uncreatednet/wikilab-ufabc/folhas/completo.pdf

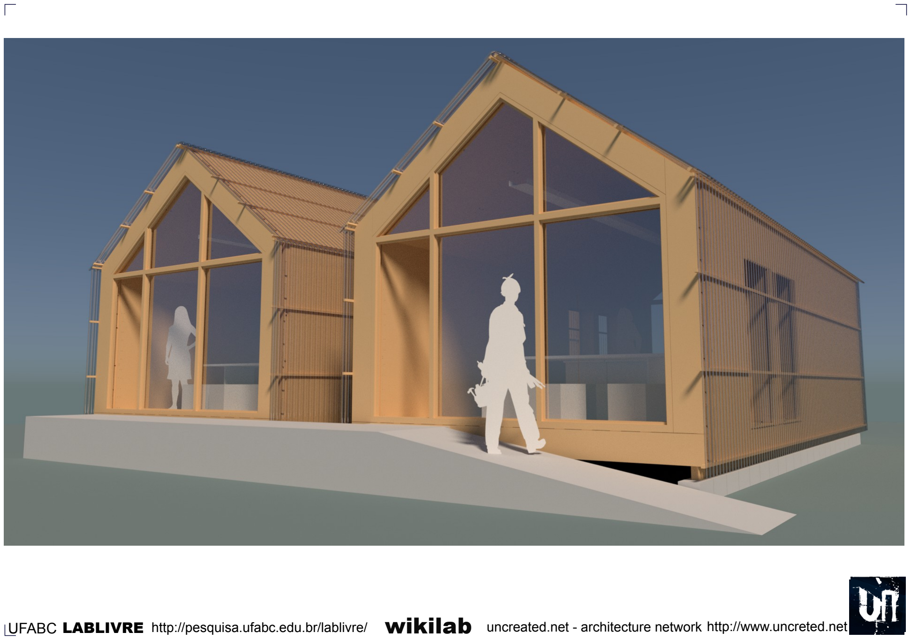
[picture p20: page 1]

UFABC LABLIVRE http://pesquisa.ufabc.edu.br/lablivre/ wikilab uncreated.net - architecture network http://www.uncreted.net

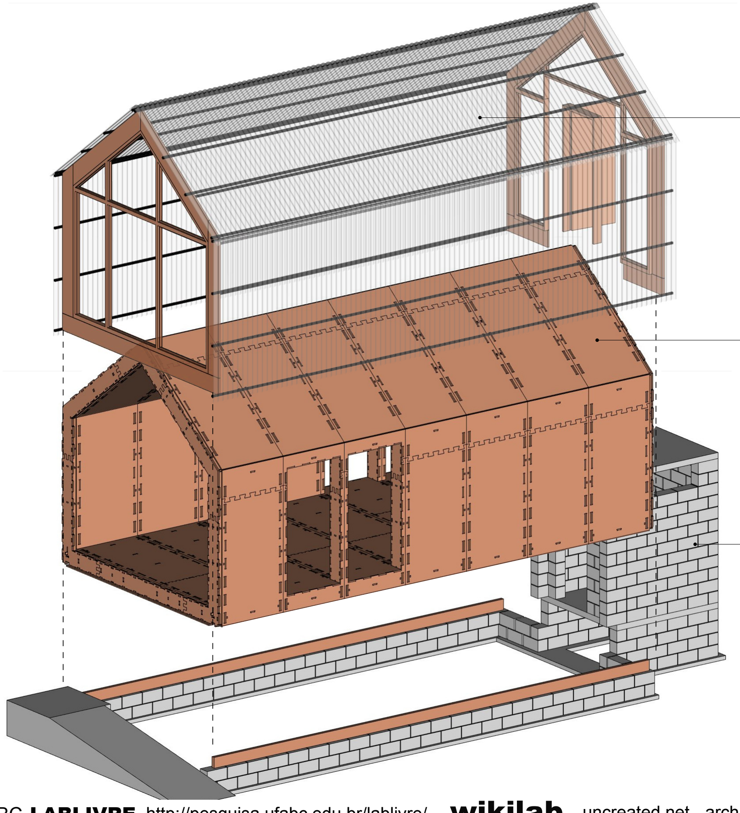
[picture p21: figure]

Fase 1

Feita por empreiteira
Construção da base de alvenaria Equipamentos sanitários
Vigas-guia

Fase 2

Feita por voluntários e comunidade Montagem dos módulos Wikihouse

Fase 3

Feita por voluntários e comunidade com apoio de empreiteira
Montagem da cobertura
Colocação dos caixilhos

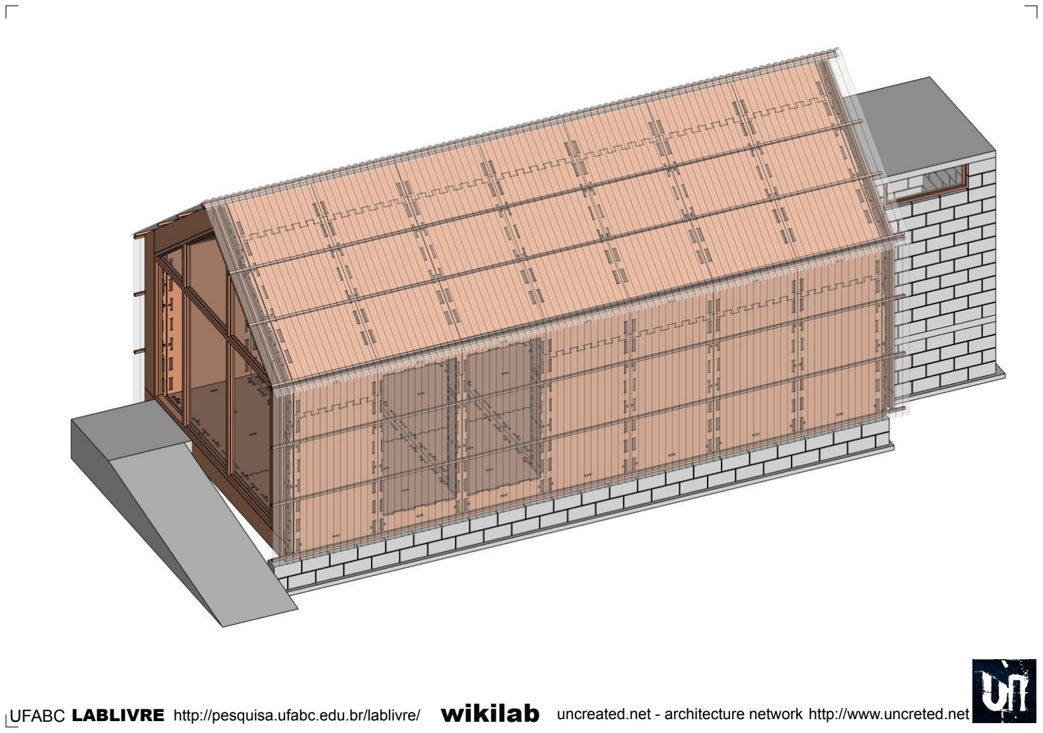
[picture p22: page 3]
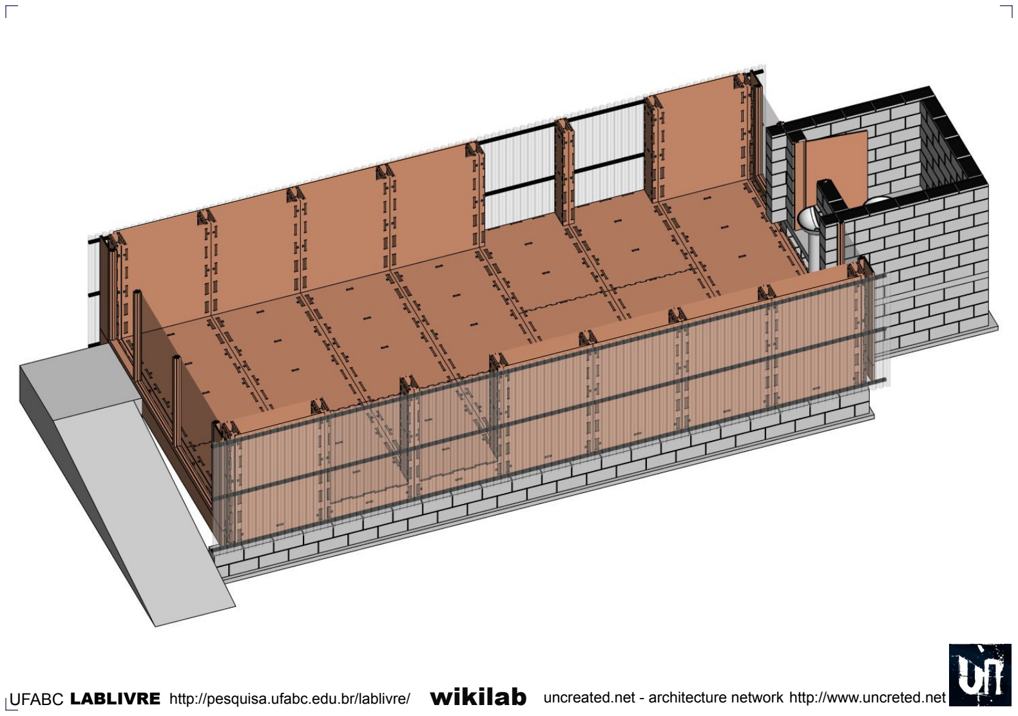
[picture p23: page 4]
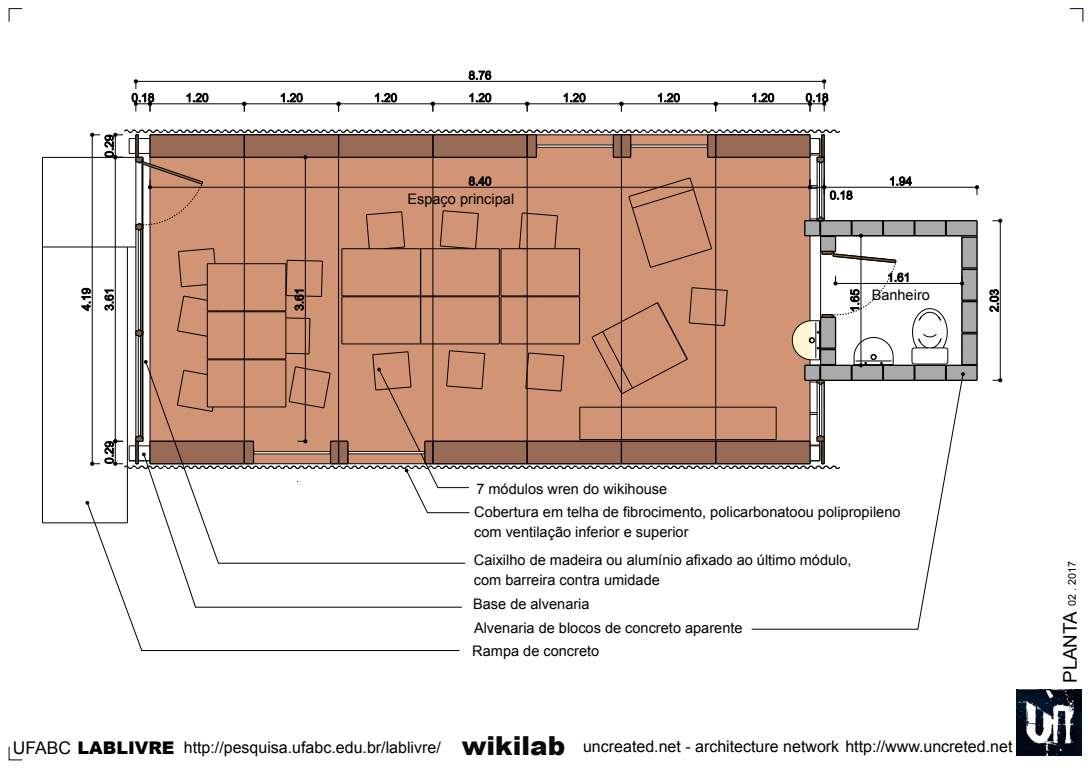
[picture p24: page 5]
wikilab; Espaço principal; Banheiro; UFABC LABLIVRE; PLANTA 02 . 2017; http://pesquisa.ufabc.edu.br/lablivre/; uncreated.net - architecture network http://www.uncreted.net

7 módulos wren do wikihouse
Cobertura em telha de fibrocimento, policarbonatoou polipropileno
com ventilação inferior e superior
Caixilho de madeira ou alumínio afixado ao último módulo,
com barreira contra umidade
Base de alvenaria
Alvenaria de blocos de concreto aparente
Rampa de concreto

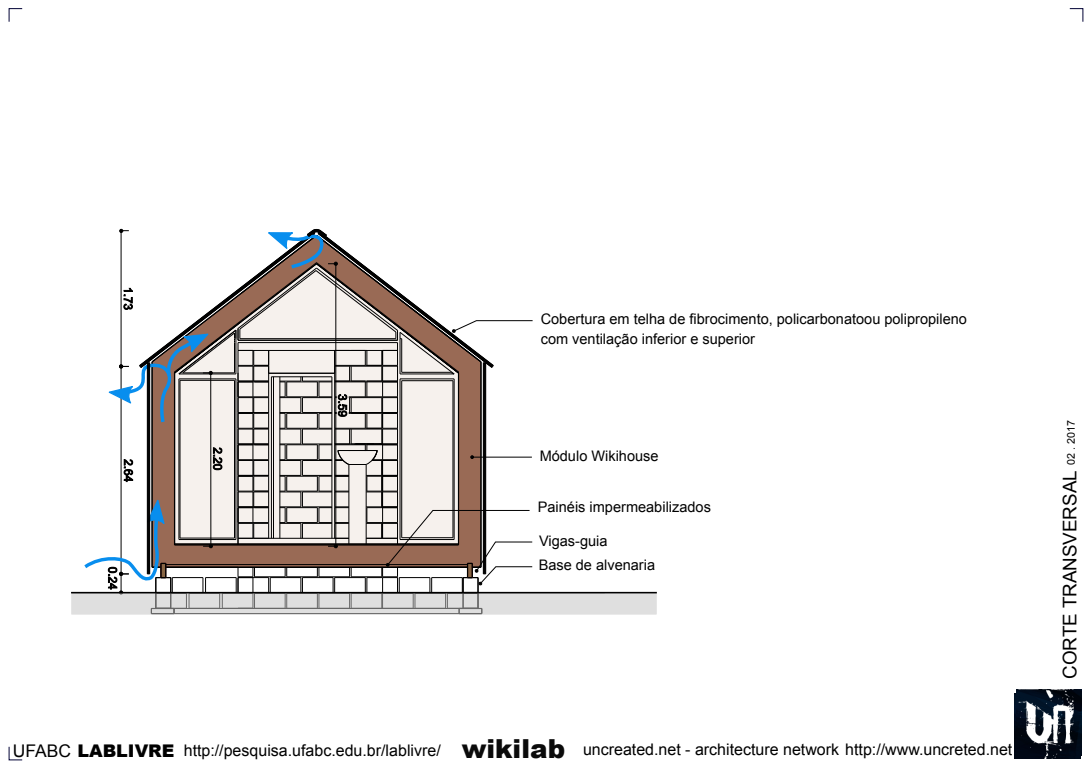
[picture p25: page 6]
CORTE TRANSVERSAL 02 . 2017; Módulo Wikihouse; Painéis impermeabilizados

Cobertura em telha de fibrocimento, policarbonatoou polipropileno
com ventilação inferior e superior

Vigas-guia
Base de alvenaria

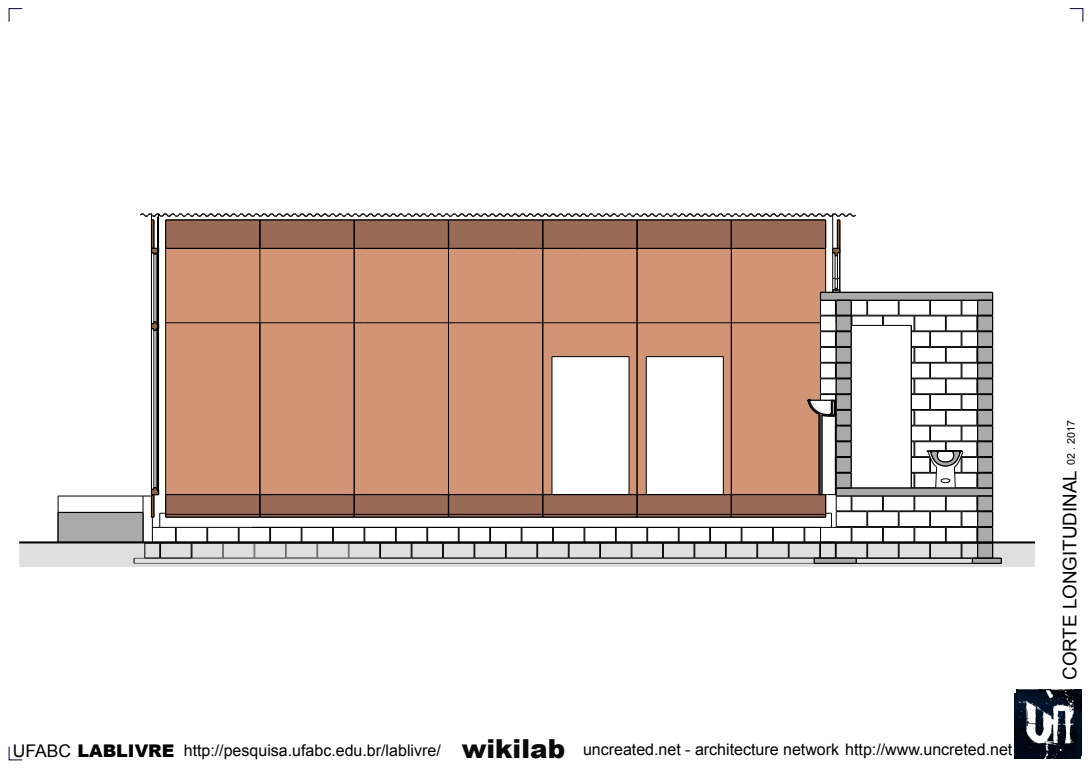
[picture p26: page 7]
CORTE LONGITUDINAL 02 . 2017

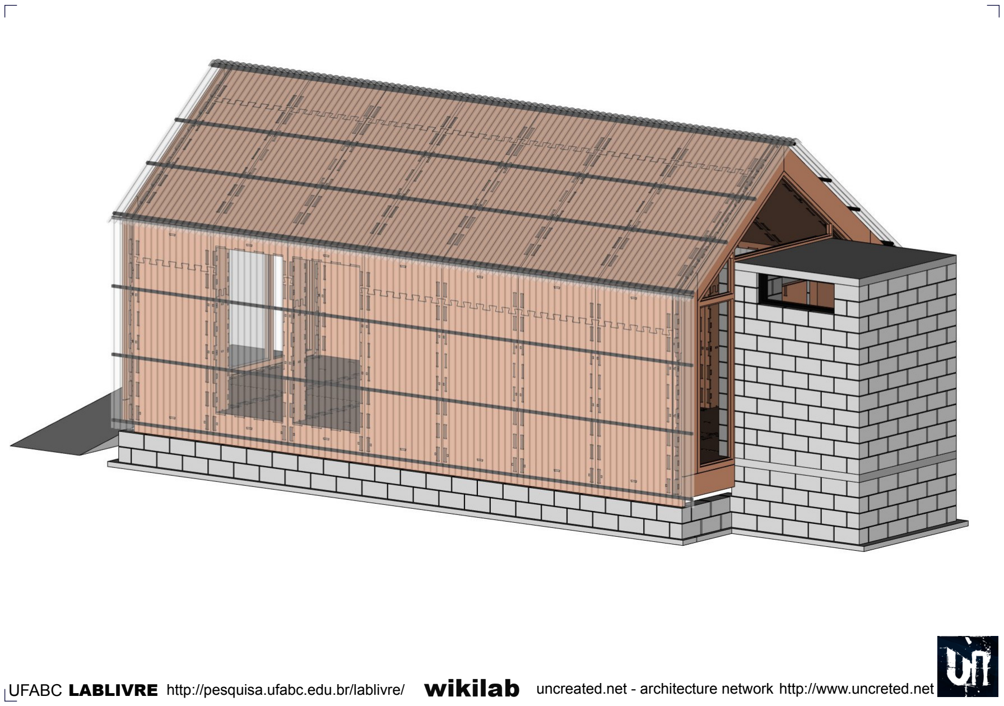
[picture p27: page 8]
