uncreatednet/wikilab-ufabc/elétrico/final/1718-EL-MC-01-R00.pdf

1/16

DESCRIÇÃO DA REVISÃO / PROPÓSITO DA EMISSÃO

0 | AVG | CS | MI | 09/10/17 | EMISSÃO INICIAL / PARA INFORMAÇÃO
REVISÃO | ELABORADO | VERIFICADO | APROVADO
ELÉTRICA | N° DOC: | 1718-EL-MC-01

MEMÓRIA DE CÁLCULO DE SPDA

N° CLIENTE: | ---
OS: | 1718 | REV.:
DATA: | 09/10/2017 | FL.:

0

CLIENTE: | IGMA - CONSTRUÇÕES LTDA | LOCAL: | SÃO BERNARDO DO CAMPO
PROJETO: | WIKILAB | ATIVIDADE: | ELÉTRICA

MARIO IKEDA
Engenheiro Eletricista
CREA Nº0600918701

DATA

### ELÉTRICA MEMÓRIA DE CÁLCULO DE SPDA

### PDF created with pdfFactory Pro trial version www.pdffactory.com

2/16
CLIENTE: | IGMA - CONSTRUÇÕES LTDA | LOCAL: | SÃO BERNARDO DO CAMPO
PROJETO: | WIKILAB | ATIVIDADE: | ELÉTRICA
Revisão | 0 | 1 | 2 | 3 | 4 | 5 | Revisão | 0 | 1 | 2 | 3 | 4 | 5 | Revisão | 0 | 1 | 2 | 3 | 4 | 5
Folha | | | | | | | Folha | | | | | | | Folha
1 | X | | | | | | 21 | | | | | | | 41
2 | X | | | | | | 22 | | | | | | | 42
3 | X | | | | | | 23 | | | | | | | 43
4 | X | | | | | | 24 | | | | | | | 44
5 | X | | | | | | 25 | | | | | | | 45
6 | X | | | | | | 26 | | | | | | | 46
7 | X | | | | | | 27 | | | | | | | 47
8 | X | | | | | | 28 | | | | | | | 48
9 | X | | | | | | 29 | | | | | | | 49
10 | X | | | | | | 30 | | | | | | | 50
11 | X | | | | | | 31 | | | | | | | 51
12 | X | | | | | | 32 | | | | | | | 52
13 | X | | | | | | 33 | | | | | | | 53
14 | X | | | | | | 34 | | | | | | | 54
15 | X | | | | | | 35 | | | | | | | 55
16 | X | | | | | | 36 | | | | | | | 56
17 | | | | | | | 37 | | | | | | | 57
18 | | | | | | | 38 | | | | | | | 58
19 | | | | | | | 39 | | | | | | | 59
20 | | | | | | | 40 | | | | | | | 60

DOCUMENTOS DE REFERÊNCIA

NOTAS

CONTROLE DE REVISÃO DO DOCUMENTO
1. Deverá ser emitidoo documento completo onde será indicadoa folha revisada, conforme tabela abaixo.
01) Projeto Executivo - Wikilab

3/16
CLIENTE: | IGMA - CONSTRUÇÕES LTDA | LOCAL: | SÃO BERNARDO DO CAMPO
PROJETO: | WIKILAB | ATIVIDADE: | ELÉTRICA

1- Objetivo:

Este documento tem por finalidade determinar a necessidade, de implantação de uma proteção contra descargas atmosféricas e nos casos onde for necessária a implantação calcular os parâmetros necessários para a elaboração do projeto de SPDA.

2- Introdução:

Descargas atmosféricas para a terra podem ser perigosas para as estruturas e para as linhas de energia e de sinal.
Os perigos para uma estrutura podem resultar em:
a) Danos à estrutura e ao seu conteúdo;
b) Falhas aos sistemas eletroeletrônicos associados;
c) Ferimentos a seres vivos dentro ou perto das estruturas.

Os efeitos consequentes dos danos e falhas podem ser estendidos às vizinhanças da estrutura ou podem envolver o meio ambiente.
Para reduzir as perdas devidos às descargas atmosféricas, podem ser necessárias medidas de proteção. Quando estas são necessárias, e em qual medida, deve ser determinado pela análise de risco.
O risco, definido pela norma ABNT NBR 5419:2015 como a provável perda média anual em uma estrutura devido às descargas atmosféricas, depende de:
a) O número anual de descargas atmosféricas que influenciam a estrutura;
b) A probabilidade de dano por uma das descargas atmosféricas que influenciam;
c) A quantidade média das perdas causadas.

As descargas atmosféricas que influenciam a estrutura podem ser divididas em:

a) Descargas diretas à estrutura;
b) Descargas próximas à estrutura, diretas às linhas conectadas (linhas de energia, linhas de telecomunicações) ou perto das linhas.

Descargas atmosféricas diretas à estrutura ou a uma linha conectada podem causar danos físicos e perigo à vida.
Descargas atmosféricas próximas à estrutura ou à linha, assim como as descargas atmosféricas diretas à estrutura ou à linha, podem causar falhas dos sistemas eletroeletrônicos devido às sobretensões resultantes do acoplamento resistivo e indutivo destes sistemas com a corrente da descarga atmosférica.
Entretanto, as falhas causadas pelas sobretensões atmosféricas nas instalações do usuário e nas linhas de suprimento de energia podem também gerar sobretensões do tipo de chaveamento nas instalações.

NOTA: O mau funcionamento dos sistemas eletroeletrônicos não é coberto pela série ABNT NBR 5419:2015. Para tanto, recomenda-se consultar a IEC 61000-4-5.

O número das descargas atmosféricas que influenciam a estrutura depende das dimensões e das características das estruturas e das linhas conectadas, das características do ambiente da estrutura e das linhas, assim como da densidade de descargas atmosféricas para a terra na região onde estão localizadas a estrutura e as linhas.
A probabilidade de danos devido à descarga atmosférica depende da estrutura, das linhas conectadas, e das características da corrente da descarga atmosférica, assim como do tipo e da eficiência das medidas de proteção efetuadas.
A quantidade média da perda consequente depende da extensão dos danos e dos efeitos consequentes, os quais podem ocorrer como resultado de uma descarga atmosférica.

4/16
CLIENTE: | IGMA - CONSTRUÇÕES LTDA | LOCAL: | SÃO BERNARDO DO CAMPO
PROJETO: | WIKILAB | ATIVIDADE: | ELÉTRICA

O efeito das medias de proteção resulta das características de cada medida de proteção e pode reduzir as probabilidades de danos ou a quantidade média da perda consequente.
A decisão de prover uma proteção contra descargas atmosféricas pode ser tomada independente-mente do resultado da análise de risco, onde exista o desejo de que não haja este.

3- Referências normativas:

ABNT NBR 5419-1:2015 – Proteção contra descargas atmosféricas – Parte 1: Princípios Gerais; ABNT NBR 5419-2:2015 – Proteção contra descargas atmosféricas – Parte 2: Gerenciamento de Risco;
ABNT NBR 5419-3:2015 –Proteção contra descargas atmosféricas – Parte 3: Danos físicos a estrutura e perigos à vida;
ABNT NBR 5419-4:2015 –Proteção contra descargas atmosféricas – Parte 4: Sistemas elétricos e eletrônicos internos na estrutura;

4- Símbolos e abreviaturas:

a | Taxa de amortização
AD | Área de exposição equivalente para descargas atmosféricas a uma estrutura isolada
ADJ | Área de exposição equivalente para descargas atmosféricas a uma estrutura adjacente
AD | Área de exposição equivalente atribuída a uma saliência elevada na cobertura
AI | Área de exposição equivalente para descargas atmosféricas perto de uma linha
AL | Área de exposição equivalente para descargas atmosféricas em uma linha
AM | Área de exposição equivalente para descargas atmosféricas perto de uma estrutura
B | Edificação
CD | Fator de localização
CDJ | Fator de localização de uma estrutura adjacente
CE | Fator ambiental
CI | Fator de uma instalação de uma linha
CL | Custo anual das perdas totais na ausência de medidas de proteção
CLD | Fator dependente da blindagem, aterramento e condições de isolação da linha para
descargas atmosféricas na linha
CLI Fator dependente da blindagem, aterramento e condições de isolação da linha para descargas atmosféricas perto da linha
CLZ | Custo de perdas em uma zona
CP | Custo das medidas de proteção
COM | Custo anual das medidas de proteção selecionadas
CRL | Custo anual de perdas residuais
CRLZ | Custo de perdas residuais em uma zona
CT | Fator de tipo de linha para um transformador AT/BT na linha
Ca | Valor de animais em uma zona, em espécie
Cb | Valor do edifício relevante a zona, em espécie
Cc | Valor do conteúdo em uma zona, em espécie
Ce | Valor total dos bens em locais perigosos fora da estrutura, em espécie
Cs | Valor dos sistemas internos (incluindo suas atividades) em uma zona, em espécie
Ct | Valor total da estrutura, em espécie
Cz | Valor do patrimônio cultural em uma zona, em espécie
D1 | Ferimentos a seres vivos por choque elétrico
D2 | Danos físicos
D3 | Falhas de sistemas eletroeletrônicos
hZ | Fator de aumento de perda quando um perigo especial está presente
H | Altura da estrutura
HJ | Altura de uma estrutura adjacente
i | Taxa de juros
KMS | Fator relevante ao desempenho das medidas de proteção contra LEMP
KS1 | Fator relevante à efetividade da blindagem por malha de uma estrutura

5/16
CLIENTE: | IGMA - CONSTRUÇÕES LTDA | LOCAL: | SÃO BERNARDO DO CAMPO
PROJETO: | WIKILAB | ATIVIDADE: | ELÉTRICA
KS2 | Fator relevante à efetividade da blindagem por malha dos campos internos de uma estrutura
KS3 | Fator relevante as características do cabeamento interno
KS4 | Fator relevante à tensão suportável de impulso de um sistema
L | Comprimento da estrutura
La | Comprimento da estrutura adjacente
LA | Perda relacionada aos ferimentos a seres vivos por choque elétrico (descargas atmosféricas
à estrutura)
LB Perda em uma estrutura relacionada a danos físicos (descargas atmosféricas à estrutura) Comprimento de uma seção da linha
LC | Perda relacionada a falha dos sitemas internas (descargas atmosféricas à estrutura)
LE | Perda adicional quando os danos envolvem estruturas ao redor
LF | Perda em uma estrutura devido a danos físicos
LFE | Perda devido a danos físicos fora da estrutura
LFT | Perda total devido a danos físicos dentro e fora da estrutura
LM | Perda relacionada à falha de sistemas internas (descargas atmosféricas perto de uma
estrutura)
LO | Perda em uma estrutura devido à falha de sistemas internos
LT | Perda devido a ferimentos por choque elétrico
LU | Perda relacionada a ferimentos de seres vivos por choque elétrico (descargas atmosféricas
na linha
LV | Perda em uma estrutura devido a danos físicos (descargas atmosféricas na linha)
LW | Perda devido à falha de sistemas internos (descargas atmosféricas na linha)
LX | Perda consequente a danos relevantes a estrutura
LZ | Perda relacionada à falha de sistemas internos (descargas atmosféricas na linha)
L1 | Perda de vida humana
L2 | Perda de serviço ao público
L3 | Perda de patrimônio cultural
L4 | Perda de valor econômico
m | Taxa de manutenção
NX | Número de eventos perigosos por ano
ND | Número de eventos perigosos devido às descargas atmosféricas em uma estrutura
NDJ | Número de eventos perigosos devido às descargas atmosféricas em uma estrutura adjacente
NG | Densidade de descargas atmosféricas para a terra
NI | Número de eventos perigosos devido às descargas atmosféricas perto de uma linha
NL | Número de eventos perigosos devido às descargas atmosféricas a uma linha
NM | Número de eventos perigosos devido às descargas atmosféricas perto de uma estrutura
nZ | Número de possíveis pessoas em perigo (vítimas ou usuários não servidos)
nt | Número total de pessoas (ou usuários atendidos) esperado
P | Probabilidade de danos
PA | Probabilidade de ferimentos de seres vivos por choque elétrico (descargas atmosféricas à
estrutura)
PB | Probabilidade de danos físicos à estrutura (descargas atmosféricas à estrutura)
PC | Probabilidade de falha de sistemas internos (descargas atmosféricas à estrutura)
PEB | Probabilidade de reduzir PU e PV dependendo das características da linha e da tensão
suportável do equipamento quando EB (ligação equipotencial) é instalada
PLD Probabilidade de reduzir PU, PV e PW dependendo das características da linha e da tensão suportável do equipamento (descargas atmosféricas na linha conectada)
PLI Probabilidade de reduzir PZ dependendo das características da linha e da tensão suportável do equipamento (descargas atmosféricas perto da linha conectada)
PM Probabilidade de falha de sistemas internos (descargas atmosféricas perto da linha conectada)
PMSI Probabilidade de reduzir PM dependendo da blindagem, cabeamento e da tensão suportável do equipamento
PSPD Probabilidade de reduzir PC, PM, PW e PZ quando um sistema coordenado de DPS está instalado
PTA Probabilidade de reduzir PA dependendo das medidas de proteção contra tensões de toque e

6/16
CLIENTE: | IGMA - CONSTRUÇÕES LTDA | LOCAL: | SÃO BERNARDO DO CAMPO
PROJETO: | WIKILAB | ATIVIDADE: | ELÉTRICA

passo
PU Probabilidade de ferimentos de seres vivos por choque elétrico (descargas atmosféricas perto da linha conectada)
PV | Probabilidade de danos físicos à estrutura (descargas atmosféricas perto da linha conectada)
PW | Probabilidade de falha de sistemas internos (descargas atmosféricas na conectada)
PX | Probabilidade de danos relevantes à estrutura (descargas atmosféricas à estrutura)
PZ | Probabilidade de falha de sistemas internos (descargas atmosféricas perto da linha
conectada)
rt | Fator de redução associado ao tipo de superfície do solo
rf | Fator redutor de perda dependente do risco de incêndio
rp | Fator redutor de perda devido às precauções contra incêndio
R | Risco
RA | Componente de risco (ferimentos a seres vivos - descarga atmosférica na estrutura)
RB | Componente de risco (danos físicos na estrutura - descarga atmosférica na estrutura)
RC | Componente de risco (falha dos sistemas internos - descarga atmosférica na estrutura)
RM | Componente de risco (falha dos sistemas internos - descarga atmosférica perto da estrutura)
RS | Resistência da blindagem por unidade de comprimento de um cabo
RT | Risco tolerável
RU | Componente de risco (ferimentos a seres vivos - descarga atmosférica na linha conectada)
RV | Componente de risco (danos físicos na estrutura - descarga atmosférica na linha conectada)
RW | Componente de risco (falha dos sistemas internos - descarga atmosférica na linha conectada)
RX | Componente de risco para uma estrutura
RZ | Componente de risco (falha dos sistemas internos - descarga atmosférica perto da linha)
R1 | Risco de perda de vida humana em uma estrutura
R2 | Risco de perda de serviço ao público em uma estrutura
R3 | Risco de perda de patrimônio cultural em uma estrutura
R4 | Risco de perda de valor econômico em uma estrutura
R'4 | Risco R4

quando medidas de proteção forem adotadas
S | Estrutura
S | Economia anual de dinheiro
SL | Seção de uma linha
S1 | Fonte de dano - descargas atmosféricas na estrutura
S2 | Fonte de dano - descargas atmosféricas perto da estrutura
S3 | Fonte de dano - descargas atmosféricas na linha
S4 | Fonte de dano - descargas atmosféricas perto da linha
te | Tempo, em horas por ano, da presença de pessoas em locais perigosos fora da estrutura
tz | Tempo, em horas por ano, que pessoas estão presentes em um local perigoso
TD | Dias de tempestades por ano
UW | Tensão suportável nominal de impulso de um sistema
w | Largura da malha
W | Largura da estrutura
WJ | Largura da estrutura adjacente
X | Identificador subscrito do componente de risco relevante
ZS | Zonas de uma estrutura

7/16
CLIENTE: | IGMA - CONSTRUÇÕES LTDA | LOCAL: | SÃO BERNARDO DO CAMPO
PROJETO: | WIKILAB | ATIVIDADE: | ELÉTRICA

5- Análise da quantidade de perda Lx

:

A perda Lx se refere à quantidade relativa média de um tipo particular de dano para um evento perigoso causado por uma descarga atmosférica considerando a sua extensão e os efeitos. O valor de perda Lx varia com o tipo de perda considerada:

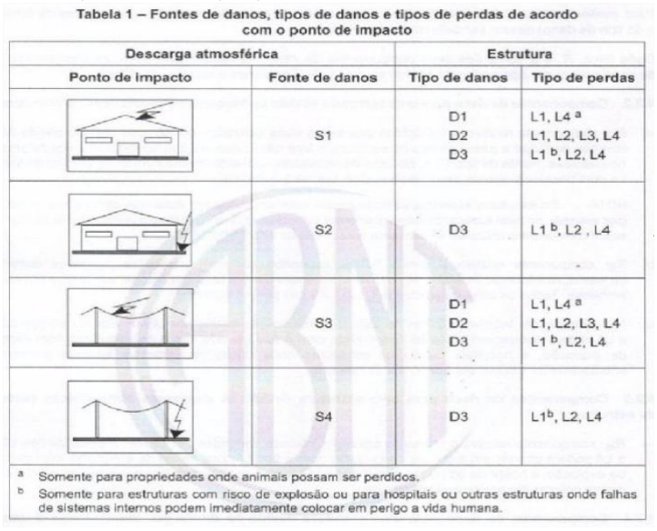
[picture p28: figure]

Tabela 1, ABNT NBR 5419-2:2015, pg.15

Fontes dos danos
a) S1: descargas atmosféricas na estrutura;
b) S2: descargas atmosféricas perto da estrutura;
c) S3: descargas atmosféricas na linha;
d) S4: descargas atmosféricas perto da linha.
Tipos de danos:
a) D1: ferimentos aos seres vivos por choque elétrico;
b) D2: danos físicos;
c) D3: falhas de sistemas eletroeletrônicos.
Tipos de perdas:
a) L1: perda de vida humana (incluindo ferimentos permanentes);
b) L2: perda de serviço ao público;
c) L3: perda de patrimônio cultural;
d) L4: perda de valores econômicos (estrutura, conteúdo e perdas de atividades).

8/16
CLIENTE: | IGMA - CONSTRUÇÕES LTDA | LOCAL: | SÃO BERNARDO DO CAMPO
PROJETO: | WIKILAB | ATIVIDADE: | ELÉTRICA

Relevância de perdas para o tipo de estrutura:

É de responsabilidade da autoridade que tenha jurisdição identificar o valor do risco tolerável. Valores representativos de risco tolerável RT, onde as descargas atmosféricas envolvem perdas de vida humana ou perda de valores sociais ou culturais, são fornecidos na Tabela 4 da ABNT NBR 5419-2:2015.
Em princípio, para perda de valor econômico (L4), a rotina a ser seguida é a comparação custo/ benefício dada no anexo D da NBR 5419-2:2015. Se os dados para esta análise não estão disponíveis, o valor representativo de risco tolerável RT= 10⁻³ pode ser utilizado.

6-Características da estrutura e do meio ambiente:

Para a determinação do valor da Densidade de descargas atmosféricas para terra NG, consultar o site: http://www.inpe.br/webelat/ABNT_NBR5419_Ng/

| O valor adotado é de | Ng.

Os dados da dimensão da estrutura (largura, comprimento e altura) são obtidos através de levantamento de campo ou informações de projeto e foram adotadas as seguintes dimensões:

Comprimento (m): | Largura (m): | Altura (m):

Os dados para o fator de localização da estrutura CD são dados na tabela A.1 da ABNT NBR 5419-2:2015, e foi adotada a seguinte opção:

Os dados para a probabilidade PB de uma descarga atmosférica em uma estrutura causar danos físicos são dados na tabela B.2 da ABNT NBR 5419-2:2015, e foi adotada a seguinte opção:

Na tabela B.7 da ABNT NBR 5419-2:2015 é dado o valor da probabilidade PEB em função do NP para o qual os DPS foram projetados. Para a definição de valor para ligação equipotencial foi adotado:

Para os valores da blindagem espacial externa, dados na Tabela B.5 da ABNT NBR 5419-2:2015, foi adotada a seguinte opção:

7-Linha de energia:

Definir o comprimento de uma seção da linha LL

(em m). Quando o comprimento LL

da seção da
linha é desconhecido, LL = 1000 m é assumido conforme itens A.4 e A.5, da ABNT NBR 5419-2:2015.

Comprimento (m):

O fator de instalação da linha CI

é encontrado na Tabela A.2 da ABNT NBR 5419-2:2015 e foi adotada a seguinte opção:

10,7

4,7

25

Enterrado

10,9 | 4,5
Área de exposição equivalente da estrutura (m²): | 1107,91003546

Estrutura cercada por objetos mais altos

Não blindado (grandes laços > 10 m²)

DPS: III-IV

Estrutura não protegida por SPDA

9/16
CLIENTE: | IGMA - CONSTRUÇÕES LTDA | LOCAL: | SÃO BERNARDO DO CAMPO
PROJETO: | WIKILAB | ATIVIDADE: | ELÉTRICA

O fator tipo de linha CT é encontrado na Tabela A.3 da ABNT NBR 5419-2:2015 e foi adotada a seguinte opção:

O fator ambiental da linha CE é encontrado na Tabela A.4 da ABNT NBR 5419-2:2015 e foi adotada a seguinte opção:

O valor para a blindagem da linha (Ω/Km) é encontrado na Tabela B.8 da ABNT NBR 5419-2:2015 e foi adotada a seguinte opção:

Os valores CLD (Fator dependente da blindagem, aterramento e condições de isolação da linha para descargas atmosféricas na linha) e CLI (Fator dependente da blindagem, aterramento e condições de isolação da linha para descargas atmosféricas perto da linha) podem ser encontrados na Tabela B.4 da ABNT NBR 5419-2:2015 e foi adotada a seguinte opção:

CLD =

CLI =

Os dados da dimensão da estrutura adjacente (largura, comprimento e altura) são obtidos através de levantamento de campo ou informações de projeto e foram adotadas as seguintes dimensões:

Comprimento (m): | Largura (m): | Altura (m):

Os dados do fator de localização da estrutura adjacente são obtidos na Tabela A.1 da ABNT NBR 5419-2:2015 e foi adotada a seguinte opção:

A tensão suportável nominal de impulso dos sitemas internos UW é dado em (KV) em valor constante constante de 2,5.
O fator KS4 é dado na equação Ks4 = 1/UW. O valor máximo de KS4 é limitado a 1. Se existirem equipamentos com níveis diferentes de tensão suportável a impulso em um sistema interno, o fator KS4 correspondente ao menor nível de tensão suportável de impulso deve ser escolhido.

KS4 =

O valor de PLD ,Probabilidade de reduzir PU, PV e PW dependendo das características da linha e da tensão suportável do equipamento (descargas atmosféricas na linha conectada) é dado na Tabela B.8 da ABNT NBR 5419-2:2015 e foi adotado o seguinte valor:

PLD =

O valor de PLI, probabilidade de reduzir PZ dependendo das características da linha e da tensão suportável do equipamento (descargas atmosféricas perto da linha conectada) é dado na Tabela B.9 da ABNT NBR 5419-2:2015 e foi adotado o seguinte valor:

PLI =

Linha de energia ou sinal

Urbano

0

Nenhuma

0,40

1,00

0,30

Linha aérea ou enterrada, não blindada ou com blindagem não interligada

Linha enterrada não blindada

Linha enterrada não blindada

0 | 0

10/16
CLIENTE: | IGMA - CONSTRUÇÕES LTDA | LOCAL: | SÃO BERNARDO DO CAMPO
PROJETO: | WIKILAB | ATIVIDADE: | ELÉTRICA

8-Linha de sinal:

Definir o comprimento de uma seção da linha LL

(em m). Quando o comprimento LL

da seção da
linha é desconhecido, LL = 1000 m é assumido conforme itens A.4 e A.5, da ABNT NBR 5419-2:2015.

Comprimento (m):

O fator de instalação da linha CI

é encontrado na Tabela A.2 da ABNT NBR 5419-2:2015 e foi adotada a seguinte opção:

O fator tipo de linha CT é encontrado na Tabela A.3 da ABNT NBR 5419-2:2015 e foi adotada a seguinte opção:

O fator ambiental da linha CE é encontrado na Tabela A.4 da ABNT NBR 5419-2:2015 e foi adotada a seguinte opção:

O valor para a blindagem da linha (Ω/Km) é encontrado na Tabela B.8 da ABNT NBR 5419-2:2015 e foi adotada a seguinte opção:

Os valores CLD (Fator dependente da blindagem, aterramento e condições de isolação da linha para descargas atmosféricas na linha) e CLI (Fator dependente da blindagem, aterramento e condições de isolação da linha para descargas atmosféricas perto da linha) podem ser encontrados na Tabela B.4 da ABNT NBR 5419-2:2015 e foi adotada a seguinte opção:

CLD =

CLI =

Os dados da dimensão da estrutura adjacente (largura, comprimento e altura) são obtidos através de levantamento de campo ou informações de projeto e foram adotadas as seguintes dimensões:

Comprimento (m): | Largura (m): | Altura (m):

Os dados do fator de localização da estrutura adjacente são obtidos na Tabela A.1 da ABNT NBR 5419-2:2015 e foi adotada a seguinte opção:

A tensão suportável nominal de impulso dos sitemas internos UW é dado em (KV) em valor constante constante de 2,5.
O fator KS4 é dado na equação Ks4 = 1/UW. O valor máximo de KS4 é limitado a 1. Se existirem equipamentos com níveis diferentes de tensão suportável a impulso em um sistema interno, o fator KS4 correspondente ao menor nível de tensão suportável de impulso deve ser escolhido.

KS4 =

0 | 0

25

Enterrado

Linha de energia ou sinal

Urbano

Linha aérea ou enterrada, não blindada ou com blindagem não interligada

Linha enterrada não blindada

Linha enterrada não blindada

0

Nenhuma

0,40

11/16
CLIENTE: | IGMA - CONSTRUÇÕES LTDA | LOCAL: | SÃO BERNARDO DO CAMPO
PROJETO: | WIKILAB | ATIVIDADE: | ELÉTRICA

O valor de PLD ,Probabilidade de reduzir PU, PV e PW dependendo das características da linha e da tensão suportável do equipamento (descargas atmosféricas na linha conectada) é dado na Tabela B.8 da ABNT NBR 5419-2:2015 e foi adotado o seguinte valor:

PLD =

O valor de PLI, probabilidade de reduzir PZ dependendo das características da linha e da tensão suportável do equipamento (descargas atmosféricas perto da linha conectada) é dado na Tabela B.9 da ABNT NBR 5419-2:2015 e foi adotado o seguinte valor:

PLI =

9- Fatores para definição das Zonas:

Para avaliar cada componente de risco, a estrutura pode ser dividida em zonas ZS cada uma com características homogêneas. Entretanto, a estrutura pode ser, ou pode assumir ser, uma zona única.

a) Zonas ZS são principalmente definidas por:
* tipo de solo ou piso (componentes de risco RA e RU);
* compartimentos à prova de fogo (componentes de risco RB e RV);
* blindagem espacial (componentes de risco RC e RM).
b) Zonas adicionais podem ser definidas de acordo com:
* leiaute dos sistemas internos (componentes de risco RC e RM);
* medidas de proteção existentes ou a serem instaladas (todos componentes de risco);
* valores de perdas LX (todos componentes de risco).

A divisão da estrutura em zona ZS deve levar em conta a exequibilidade da implementação da maioria das medidas de proteção adequadas.

Fatores válidos para a zona:

Para a definição do fator de redução rt

em função do tipo da superfície do solo ou piso, são dados os valores na Tabela C.3 da ABNT NBR 5419-2:2015 e foi adotado a seguinte opção:

Os valores da probabilidade PTA de uma descarga atmosférica em uma estrutura causar ferimentos a seres vivos por meio de choque elétrico, são dados na Tabela B.1 da ABNT NBR 5419-2:2015 e foi adotado a seguinte opção:

Os valores da probabilidade PTU de uma descarga atmosférica em uma linha que adentre a estrutura causar choque a seres vivos devido a tensões de toque perigosas, não são aplicáveis para área externa e são dados na Tabela B.6 da ABNT NBR 5419-2:2015 e foi adotado a seguinte opção:

Agricultura, concreto

Z1

Não Aplicável

0,20

Zona | Nº pessoas | Tempo de Presença (Horas)
Z1 | Externo | 1 | 8760
Z2 | Interno | 21 | 8760

1,00

Nenhuma medida de proteção

12/16
CLIENTE: | IGMA - CONSTRUÇÕES LTDA | LOCAL: | SÃO BERNARDO DO CAMPO
PROJETO: | WIKILAB | ATIVIDADE: | ELÉTRICA

Os valores do fator de redução rf

em função do risco de incêndio ou explosão na estrutura são dados na Tabela C.5 da ABNT NBR 5419-2:2015 e foi adotado a seguinte opção:

Os valores do fator de redução rp

em função das providências tomadas para reduzir as consequências de um incêndio, são dados na Tabela C.4 da ABNT NBR 5419-2:2015 e foi adotado a seguinte opção:

Os valores da blindagem espacial interna, dentro de uma ZPR (zona de proteção contra descarga atmosférica), em uma distância de segurança do limite da malha no mínimo igual à largura da malha Wm, fator KS2 para SPDA ou blindagem tipo malha espacial podem ser avaliado como
KS2 = 0,12 x Wm2, onde Wm2 é a largura da blindagem em forma de grade, ou dos condutores de descidas do SPDA tipo malha ou o espaçamento entre as colunas metálicas da estrutura, ou o espaçamento entre as estruturas de concreto armado como um SPDA natural. Para blindagens metálicas contínuas com espessura não inferior a 0,1 mm KS1 = KS2 = 10⁻⁴

NOTA 1: Onde uma rede de equipotencialização tipo malha for utilizada de acordo com a ABNT NBR 5419-4, valores de KS1 e KS2 podem ser repartidos ao meio.
Onde o laço de indução estiver passando próximo aos condutores do limite da malha da ZPR a uma distância da blindagem menor que a distância de segurança, os valores de KS1 e KS2 devem ser dobrados onde a distância para a blindagem varia de 0,1 Wm a 0,2 Wm. Para uma cascata de ZPR, o valor final de KS2 é o produto dos KS2 resultantes de cada ZPR.

NOTA 2: Os valores máximos de KS1 e KS2 são limitados a 1.

O valor do fator KS3 dependendo da fiação interna (Energia e Telecom) não é aplicável para área externa e é obtido na Tabela B.5 da ABNT NBR 5419-2:2015. Foi adotado a seguinte opção:

Energia

Telecom

O valor de probabilidade de PSPD (probabilidade de reduzir PC, PM, PW e PZ quando um sistema coordenado de DPS está instalado) em função do NP (nível de proteção) para o qual o DPS foi projetado (Energia e Telecom), não é aplicável para área externa, é dado na Tabela B.3 da ABNT NBR 5419-2:2015 e foi adotado a seguinte opção:

Energia

Telecom

NOTA 1: Um sistema DPS coordenado é efetivo na redução de PC (probabilidade de falha de sistemas internos - descargas atmosféricas à estrutura) somente em estruturas protegidas por um SPDA ou estruturas com colunas metálicas contínuas ou com colunas de concreto armado atuando como um SPDA natural, onde os requisitos de interligação e aterramento descritos na ABNT NBR 5419-3 forem satisfeitos.

NOTA 2: Os valores de PSBD podem ser reduzidos para os DPS que tenham características melhores de proteção (maior corrente nominal IN, menor nível de proteção Up

, etc.) comparados com os
requisitos definidos para NP I nos locais relevantes da instalação (ver ABNT NBR 5419-1:2015, Tabela A.3 para informação das probabilidades de corrente da descarga atmosférica e ABNT NBR 5419-1:2015, Anexo E e ABNT NBR 5419-4:2015, Anexo D ou a divisão da corrente da descarga atmosférica). Os mesmos anexos podem ser utilizados para DPS que tenham maiores probabilidades
PSPD.

Incêndio - Baixo

Extintores, inst. Oper. Manual, hidrantes, etc.

Não Aplicável

Não Aplicável

Nenhum

Nenhum

13/16
CLIENTE: | IGMA - CONSTRUÇÕES LTDA | LOCAL: | SÃO BERNARDO DO CAMPO
PROJETO: | WIKILAB | ATIVIDADE: | ELÉTRICA

Os valores do fator Hz aumentando a quantidade relativa de perda na presença de um perigo especial, são dados na Tabela C.6 da ABNT NBR 5419-2:2015 e foi adotado a seguinte opção:

Os valores do tipo de perda L1: Valores médios típicos de LT, LF e LO, são obtidos na Tabela C.2 da ABNT NBR 5419-2:2015 e foi adotado a seguinte opção:

Tipo de Dano D1

Tipo de Dano D2

Tipo de Dano D3

NOTA 1: Os valores da Tabela C.2 se referem ao atendimento contínuo de pessoas na estrutura.

NOTA 2: No caso de uma estrutura com risco de explosão, os valores para LF e LO podem necessitar de uma avaliação mais detalhada, considerando o tipo de estrutura, risco de explosão, o conceito de zona de áreas perigosas e as medidas para encontrar o risco.

O fator para pessoas em perigo é dado na fórmula:

Os valores do tipo de perda L4: Valores médios típicos de LT, LF e LO, são obtidos na Tabela C.12 da ABNT NBR 5419-2:2015 e foi adotado a seguinte opção:

Tipo de Dano D2

Tipo de Dano D3

Fatores válidos para a zona:

Para a definição do fator de redução rt

em função do tipo da superfície do solo ou piso, são dados os valores na Tabela C.3 da ABNT NBR 5419-2:2015 e foi adotado a seguinte opção:

Os valores da probabilidade PTA de uma descarga atmosférica em uma estrutura causar ferimentos a seres vivos por meio de choque elétrico, são dados na Tabela B.1 da ABNT NBR 5419-2:2015 e foi adotado a seguinte opção:

Os valores da probabilidade PTU de uma descarga atmosférica em uma linha que adentre a estrutura causar choque a seres vivos devido a tensões de toque perigosas, não são aplicáveis para área externa e são dados na Tabela B.6 da ABNT NBR 5419-2:2015 e foi adotado a seguinte opção:

Os valores do fator de redução rf

em função do risco de incêndio ou explosão na estrutura são dados na Tabela C.5 da ABNT NBR 5419-2:2015 e foi adotado a seguinte opção:

Os valores do fator de redução rp

em função das providências tomadas para reduzir as consequências de um incêndio, são dados na Tabela C.4 da ABNT NBR 5419-2:2015 e foi adotado a seguinte opção:

Incêndio - Baixo

Nenhuma medida de proteção

Nenhuma medida de proteção

Nenhum

Não aplicável

Não aplicável

Mármore, cerâmica

Sem perigo especial

Todos os tipos

Hospital, hotel, escola, ed. cívico

Z2

# ÷ × ÷ 8760 (Horas)

14/16
CLIENTE: | IGMA - CONSTRUÇÕES LTDA | LOCAL: | SÃO BERNARDO DO CAMPO
PROJETO: | WIKILAB | ATIVIDADE: | ELÉTRICA

Os valores da blindagem espacial interna, dentro de uma ZPR (zona de proteção contra descarga atmosférica), em uma distância de segurança do limite da malha no mínimo igual à largura da malha Wm, fator KS2 para SPDA ou blindagem tipo malha espacial podem ser avaliado como
KS2 = 0,12 x Wm2, onde Wm2 é a largura da blindagem em forma de grade, ou dos condutores de descidas do SPDA tipo malha ou o espaçamento entre as colunas metálicas da estrutura, ou o espaçamento entre as estruturas de concreto armado como um SPDA natural. Para blindagens metálicas contínuas com espessura não inferior a 0,1 mm KS1 = KS2 = 10⁻⁴

NOTA 1: Onde uma rede de equipotencialização tipo malha for utilizada de acordo com a ABNT NBR 5419-4, valores de KS1 e KS2 podem ser repartidos ao meio.
Onde o laço de indução estiver passando próximo aos condutores do limite da malha da ZPR a uma distância da blindagem menor que a distância de segurança, os valores de KS1 e KS2 devem ser dobrados onde a distância para a blindagem varia de 0,1 Wm a 0,2 Wm. Para uma cascata de ZPR, o valor final de KS2 é o produto dos KS2 resultantes de cada ZPR.

NOTA 2: Os valores máximos de KS1 e KS2 são limitados a 1.

O valor do fator KS3 dependendo da fiação interna (Energia e Telecom) não é aplicável para área externa e é obtido na Tabela B.5 da ABNT NBR 5419-2:2015. Foi adotado a seguinte opção:

Energia

Telecom

O valor de probabilidade de PSPD (probabilidade de reduzir PC, PM, PW e PZ quando um sistema coordenado de DPS está instalado) em função do NP (nível de proteção) para o qual o DPS foi projetado (Energia e Telecom), não é aplicável para área externa, é dado na Tabela B.3 da ABNT NBR 5419-2:2015 e foi adotado a seguinte opção:

Energia

Telecom

NOTA 1: Um sistema DPS coordenado é efetivo na redução de PC (probabilidade de falha de sistemas internos - descargas atmosféricas à estrutura) somente em estruturas protegidas por um SPDA ou estruturas com colunas metálicas contínuas ou com colunas de concreto armado atuando como um SPDA natural, onde os requisitos de interligação e aterramento descritos na ABNT NBR 5419-3 forem satisfeitos.

NOTA 2: Os valores de PSBD podem ser reduzidos para os DPS que tenham características melhores de proteção (maior corrente nominal IN, menor nível de proteção Up

, etc.) comparados com os
requisitos definidos para NP I nos locais relevantes da instalação (ver ABNT NBR 5419-1:2015, Tabela A.3 para informação das probabilidades de corrente da descarga atmosférica e ABNT NBR 5419-1:2015, Anexo E e ABNT NBR 5419-4:2015, Anexo D ou a divisão da corrente da descarga atmosférica). Os mesmos anexos podem ser utilizados para DPS que tenham maiores probabilidades
PSPD.

Os valores do fator Hz aumentando a quantidade relativa de perda na presença de um perigo especial, são dados na Tabela C.6 da ABNT NBR 5419-2:2015 e foi adotado a seguinte opção:

Os valores do tipo de perda L1: Valores médios típicos de LT, LF e LO, são obtidos na Tabela C.2 da ABNT NBR 5419-2:2015 e foi adotado a seguinte opção:

Extintores, inst. Oper. Manual, hidrantes, etc.

Não blindado (grandes laços > 10 m²)

Não blindado (grandes laços > 10 m²)

Nenhum

Nenhum

Baixo nível de pânico (2 pav. até 100 pessoas)

15/16
CLIENTE: | IGMA - CONSTRUÇÕES LTDA | LOCAL: | SÃO BERNARDO DO CAMPO
PROJETO: | WIKILAB | ATIVIDADE: | ELÉTRICA

Tipo de Dano D1

Tipo de Dano D2

Tipo de Dano D3

NOTA 1: Os valores da Tabela C.2 se referem ao atendimento contínuo de pessoas na estrutura.

NOTA 2: No caso de uma estrutura com risco de explosão, os valores para LF e LO podem necessitar de uma avaliação mais detalhada, considerando o tipo de estrutura, risco de explosão, o conceito de zona de áreas perigosas e as medidas para encontrar o risco.

O fator para pessoas em perigo é dado na fórmula:

Os valores do tipo de perda L4: Valores médios típicos de LT, LF e LO, são obtidos na Tabela C.12 da ABNT NBR 5419-2:2015 e foi adotado a seguinte opção:

Tipo de Dano D2

Tipo de Dano D3

10- Cálculo das quantidades relevantes:

Cálculo das áreas de exposição equivalentes da estrutura e das linhas:

Cálculo do número anual de eventos perigosos esperados:

| Símbolo | Resultado (m²)
Estrutura | ND | 2,96E-03
| NM | 8,57E+00
Linha de energia | NL/P | 5,35E-04
| NI/P | 5,35E-02
| NDA/P | 0
Linha de sinal | NL/T | 5,35E-04
| NI/T | 5,35E-02
| NDA/T | 0,00E+00
| Símbolo | Resultado (m²)
Estrutura | AD | 1,11E+03
| AM | 8,01E+05
Linha de energia | AL/P | 1,00E+03
| AI/P | 1,00E+05
| ADA/P | 0
Linha de sinal | AL/T | 1,00E+03
| AI/T | 1,00E+05
| ADA/T | 0,00E+00

Não aplicável

Não aplicável

Todos os tipos

Hospital, hotel, escola, ed. cívico

Nenhum

# ÷ × ÷ 8760 (Horas)

16/16
CLIENTE: | IGMA - CONSTRUÇÕES LTDA | LOCAL: | SÃO BERNARDO DO CAMPO
PROJETO: | WIKILAB | ATIVIDADE: | ELÉTRICA

11- Risco R1 - Decisão das medidas de proteção:

R1 ≥ RT: Proteção contra descargas atmosféricas é necessária. (RT = 1).

12- Risco R1 - Seleção das medidas de proteção:

Resultado após seleção da medida de proteção:

R1 ≥ RT: Proteção contra descargas atmosféricas é necessária. (RT = 1).

13- Conclusão:

De acordo com os dados fornecidos para este projeto, analisados conforme a norma ABNT NBR 5419:2015 PARTES 1 a 4, a estrutura dispensa a instalação do Sistema de Proteção de Descarga atmosférica (SPDA).

R1= | 0,04 | Proteção contra descargas atmosféricas foi atendida

Proteção contra descargas atmosféricas é desnecessária

Tipos de danos | Símbolo | Z1 | Z2 | Estrutura
D1 Ferimentos devido a choque | RA | 0,001 | 0,003 | 0,004
| RU=RU/P+RU/T | 0,000 | 0,001 | 0,002
D2 Danos físicos | RB | 0,001 | 0,028 | 0,029
| RV=RV/P+RV/T | 0,000 | 0,001 | 0,001
D3 Falha de sistemas interno | RC | 0,000 | 0,000 | 0,000
| RM | 0,000 | 0,000 | 0,000
| RW=RW/P+RW/T | 0,000 | 0,000 | 0,000
| RZ=RZ/P+RZ/T | 0,000 | 0,000 | 0,000
TOTAL | | 0,003 | 0,03265 | R1= 0,04
SPDA | Nenhuma aplicação
Ligação equipotencial | Nenhuma aplicação
R1= | 0,04
Tipos de danos | Símbolo | Z1 | Z2 | Estrutura
D1 Ferimentos devido a choque | RA | 0,001 | 0,003 | 0,004
| RU=RU/P+RU/T | 0,000 | 0,001 | 0,002
físicos | RB | 0,001 | 0,028 D2 Danos | 0,029
| RV=RV/P+RV/T | 0,000 | 0,001 | 0,001
D3 Falha de sistemas interno | RC | 0,000 | 0,000 | 0,000
| RM | 0,000 | 0,000 | 0,000
| RW=RW/P+RW/T | 0,000 | 0,000 | 0,000
| RZ=RZ/P+RZ/T | 0,000 | 0,000 | 0,000
TOTAL | | 0,003 | 0,033 | R1= 0,04
