uncreatednet/wikilab-ufabc/elétrico/final/1718-EL-MC-02-R00.pdf

1/6

DESCRIÇÃO DA REVISÃO / PROPÓSITO DA EMISSÃO

0 | AVG | CS | MI | 09/10/17 | EMISSÃO INICIAL / PARA INFORMAÇÃO
REVISÃO | ELABORADO | VERIFICADO | APROVADO
ELÉTRICA | N° DOC: | 1718-EL-MC-02

MEMÓRIA DE CÁLCULO DE ILUMINAÇÃO

N° CLIENTE: | ---
OS: | 1718 | REV.:
DATA: | 09/10/2017 | FL.:

0

CLIENTE: | IGMA - CONSTRUÇÕES LTDA | LOCAL: | SÃO BERNARDO DO CAMPO
PROJETO: | WIKILAB | ATIVIDADE: | ELÉTRICA

MARIO IKEDA
Engenheiro Eletricista
CREA Nº0600918701

DATA

### ELÉTRICA MEMÓRIA DE CÁLCULO DE ILUMINAÇÃO

### PDF created with pdfFactory Pro trial version www.pdffactory.com

2/6
CLIENTE: | IGMA - CONSTRUÇÕES LTDA | LOCAL: | SÃO BERNARDO DO CAMPO
PROJETO: | WIKILAB | ATIVIDADE: | ELÉTRICA
Revisão | 0 | 1 | 2 | 3 | 4 | 5 | Revisão | 0 | 1 | 2 | 3 | 4 | 5 | Revisão | 0 | 1 | 2 | 3 | 4 | 5
Folha | | | | | | | Folha | | | | | | | Folha
1 | X | | | | | | 21 | | | | | | | 41
2 | X | | | | | | 22 | | | | | | | 42
3 | X | | | | | | 23 | | | | | | | 43
4 | X | | | | | | 24 | | | | | | | 44
5 | X | | | | | | 25 | | | | | | | 45
6 | X | | | | | | 26 | | | | | | | 46
7 | | | | | | | 27 | | | | | | | 47
8 | | | | | | | 28 | | | | | | | 48
9 | | | | | | | 29 | | | | | | | 49
10 | | | | | | | 30 | | | | | | | 50
11 | | | | | | | 31 | | | | | | | 51
12 | | | | | | | 32 | | | | | | | 52
13 | | | | | | | 33 | | | | | | | 53
14 | | | | | | | 34 | | | | | | | 54
15 | | | | | | | 35 | | | | | | | 55
16 | | | | | | | 36 | | | | | | | 56
17 | | | | | | | 37 | | | | | | | 57
18 | | | | | | | 38 | | | | | | | 58
19 | | | | | | | 39 | | | | | | | 59
20 | | | | | | | 40 | | | | | | | 60

DOCUMENTOS DE REFERÊNCIA

NOTAS

CONTROLE DE REVISÃO DO DOCUMENTO
1. Deverá ser emitidoo documento completo onde será indicadoa folha revisada, conforme tabela abaixo.

1- MATERIAIS MISCELÂNEAS (PARAFUSOS, PORCAS, ARRUELAS, BUCHAS ETC.) DEVERÃO SER FORNECIDOS PELA MONTADORA COM ESPECIFICAÇÃO CONFORME DETALHES TÍPICOS.

01) Projeto Executivo - Wikilab

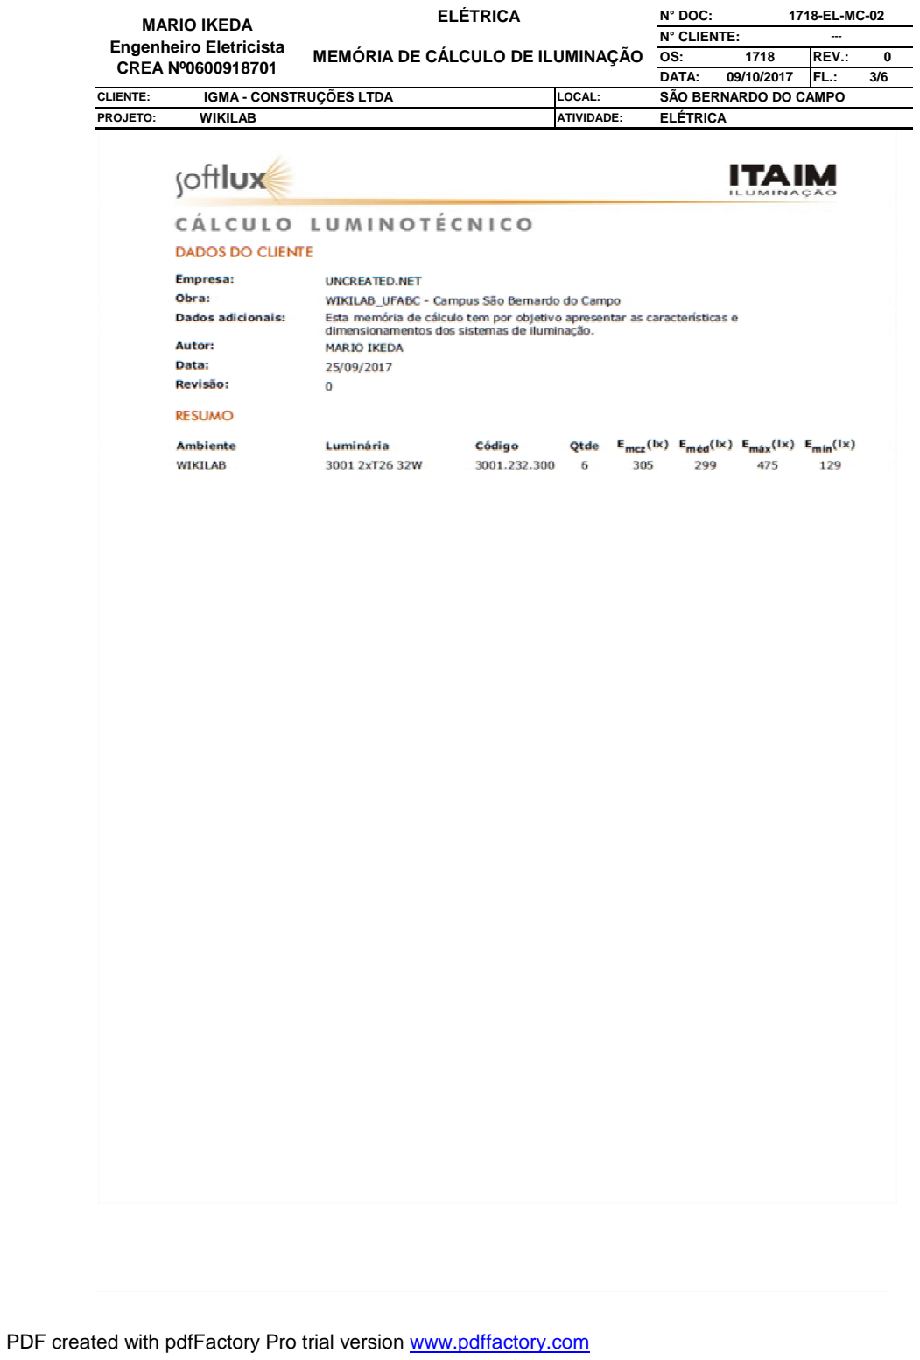
[picture p29: page 3]

3/6
CLIENTE: | IGMA - CONSTRUÇÕES LTDA | LOCAL: | SÃO BERNARDO DO CAMPO
PROJETO: | WIKILAB | ATIVIDADE: | ELÉTRICA

4/6
CLIENTE: | IGMA - CONSTRUÇÕES LTDA | LOCAL: | SÃO BERNARDO DO CAMPO
PROJETO: | WIKILAB | ATIVIDADE: | ELÉTRICA

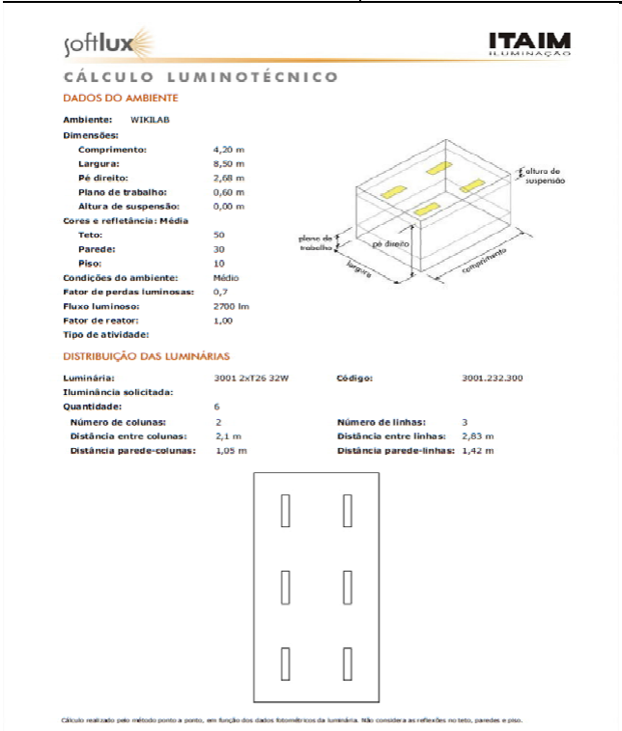
[picture p30: figure]

5/6
CLIENTE: | IGMA - CONSTRUÇÕES LTDA | LOCAL: | SÃO BERNARDO DO CAMPO
PROJETO: | WIKILAB | ATIVIDADE: | ELÉTRICA

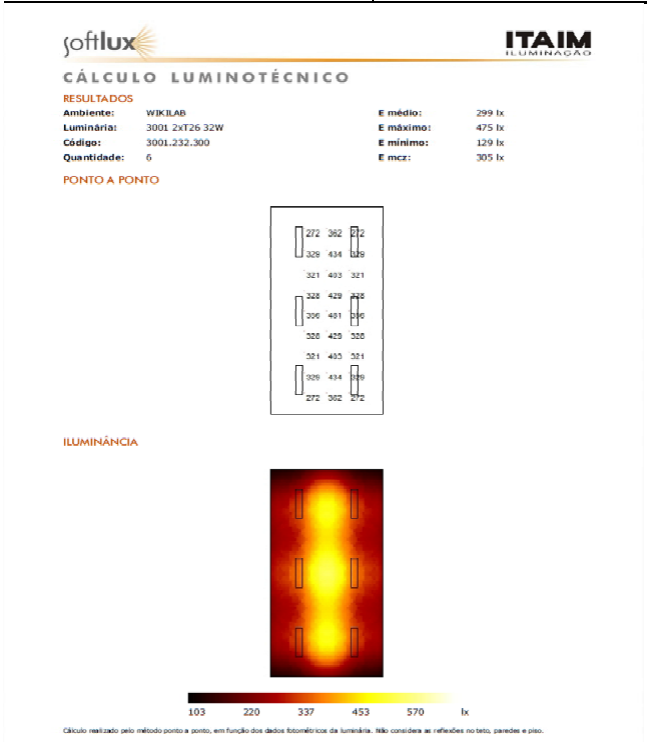
[picture p31: figure]

6/6
CLIENTE: | IGMA - CONSTRUÇÕES LTDA | LOCAL: | SÃO BERNARDO DO CAMPO
PROJETO: | WIKILAB | ATIVIDADE: | ELÉTRICA

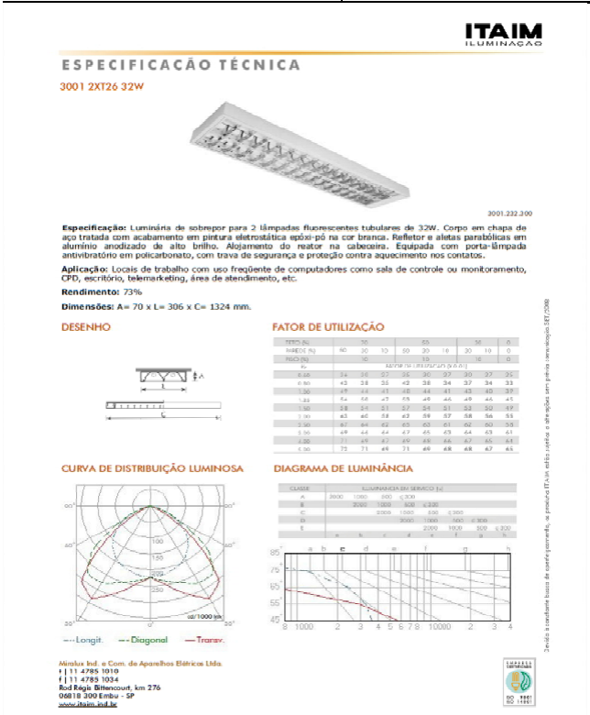
[picture p32: figure]
