uncreatednet/wikilab-ufabc/elétrico/anteprojeto/LUM-02.pdf

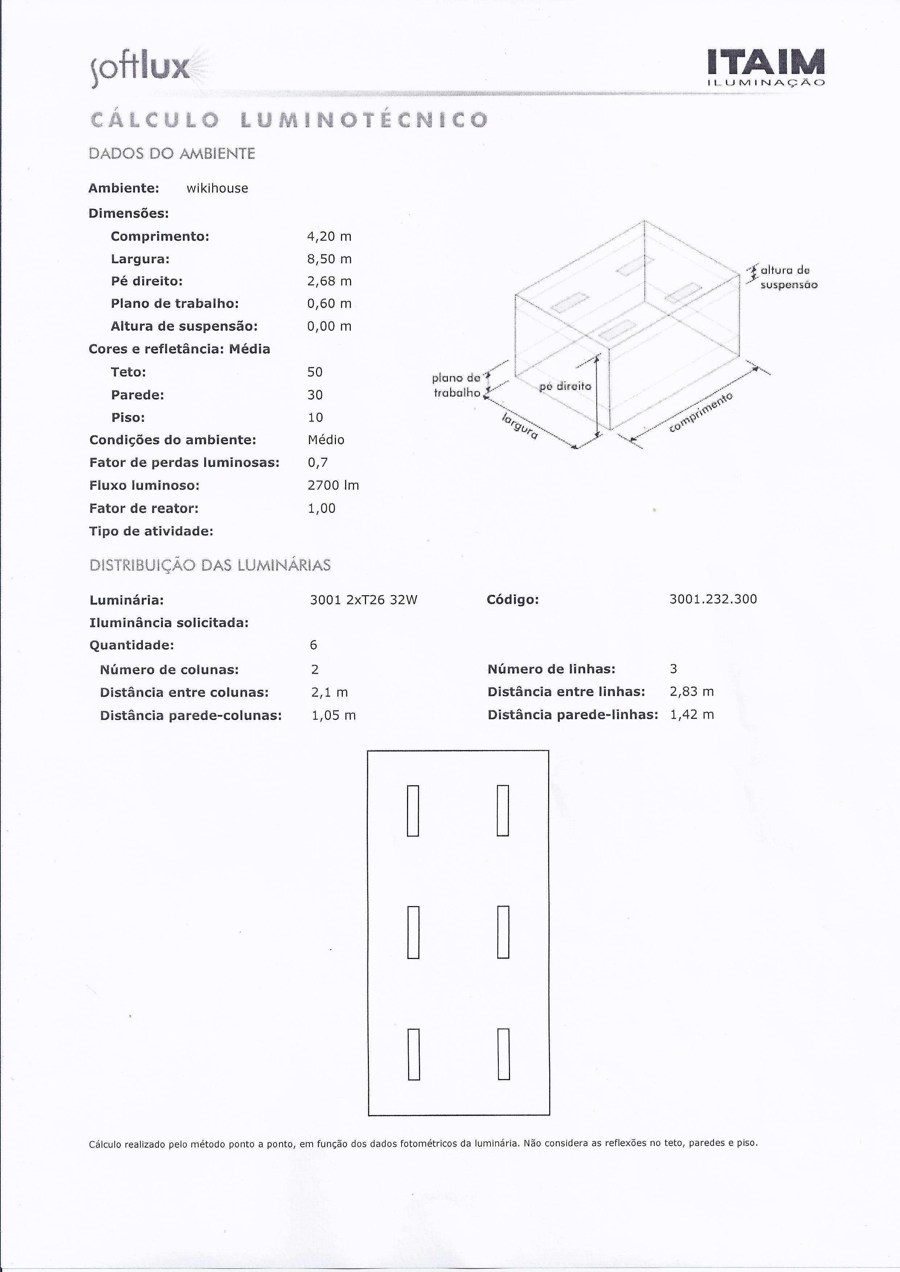
[picture p33: page 1]
