uncreatednet/wikilab-ufabc/elétrico/anteprojeto/LUM-03.pdf

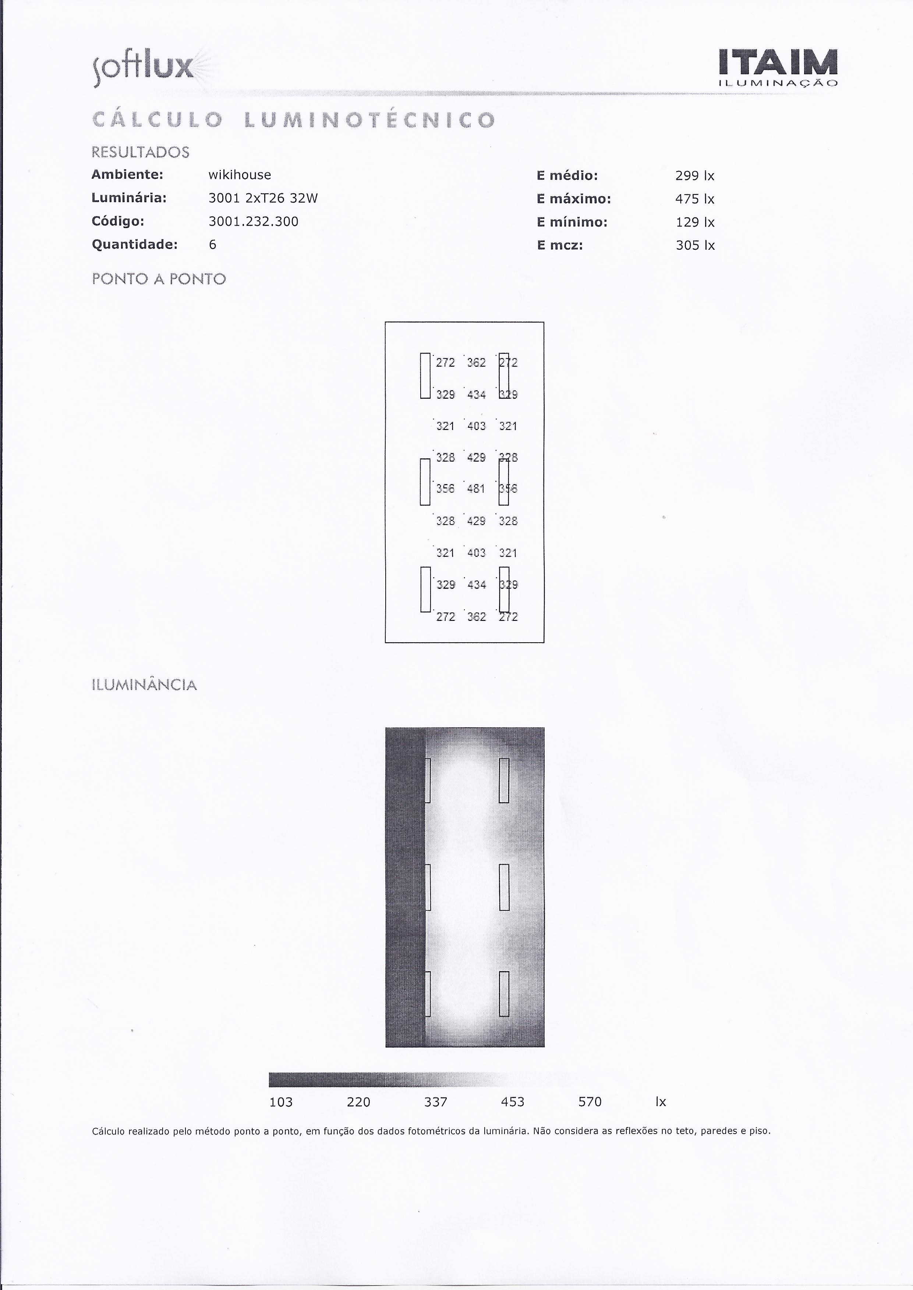
[picture p34: page 1]
