uncreatednet/wikilab-ufabc/elétrico/anteprojeto/LUM.-01.pdf

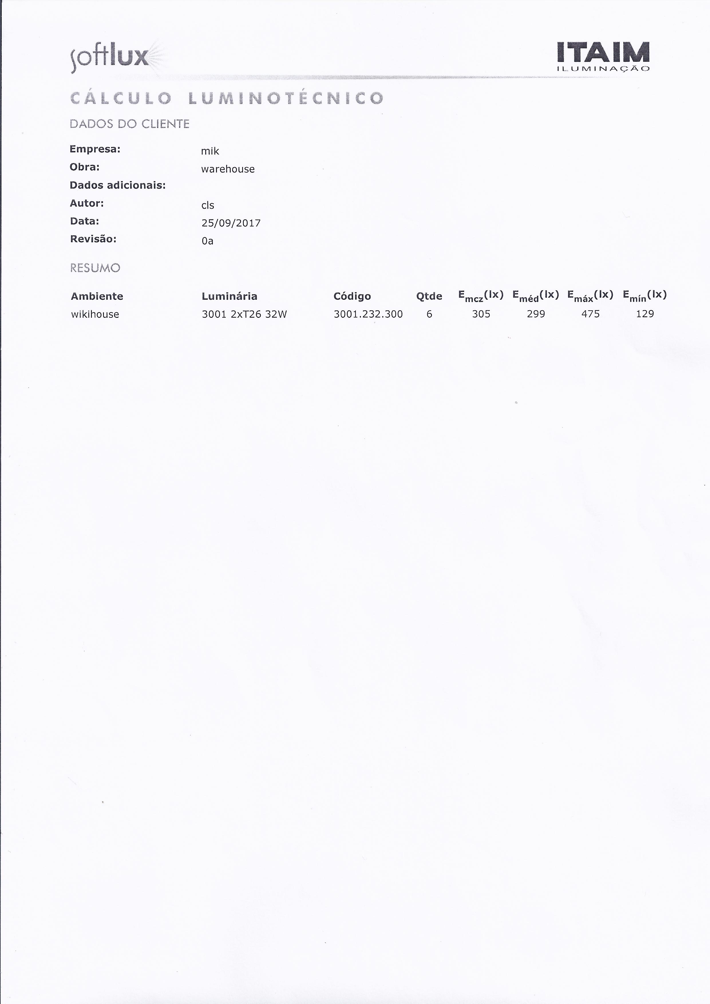
[picture p35: page 1]
