uncreatednet/wikilab-ufabc/elétrico/anteprojeto/LUM.-04.pdf

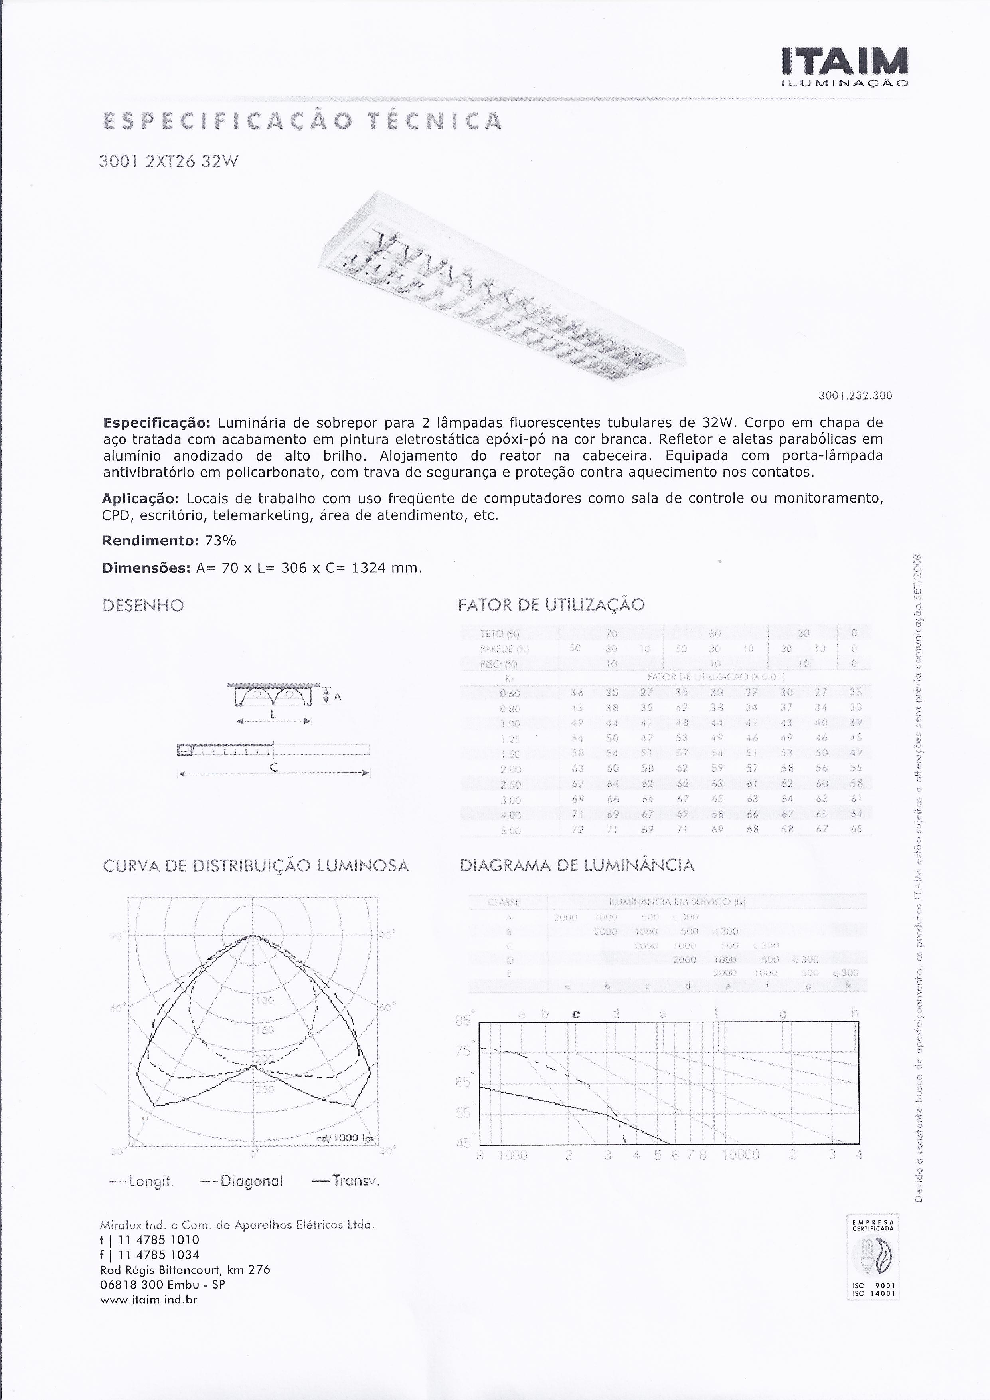
[picture p36: page 1]
