uncreatednet/wikilab-ufabc/orçamento/orçamento preliminar/cronograma.pdf

Wikilab - orçamento 24/02/2017 | 1/1
Cronograma | data: | 24.02.2017 | elaborado por:
Seção | Item | Mes 1 | Mes 2 | Mes 3 | Mes 4
1 | 2 | 3 | 4 | 5 | 6 | 7 | 8 | 9 | 10 | 11 | 12 | 13 | 14 | 15

Projeto

1 | Elaboração do projeto de arquitetura
2 | Campanha de crowdfunding
3
4 | Aprovação dos projetos junto a UFABC
5 | Outras aprovações (bombeiros, etc)

Contratação

6 | Contratação de empreiteira
7 | Formação da equipe de construção
8 | Contratação da empresa de corte de painéis

Construção

9 | Infraestrutura e ligação as redes hidro/esgoto
10 | Ligação a rede elétrica
11 | Fundações
12 | Construção da base de alvenaria
13 | Corte dos painéis & testes
14 | Construção da wikihouse
15 | Instalação da cobertura
16 | Instalação das esquadrias
17 | Instalações hidráulicas
18 | Instalações elétricas
19 | Construção da rampa e passeio
20 | Plantio da vegetação

## Lablivre Wikilab

uncreated.net

Elaboração dos projetos complementares (estrutural, hidro/eletro, incêndio)
