uncreatednet/wikilab-ufabc/apresentação/apresentação inicial/folhas pdf/mobiliário.pdf

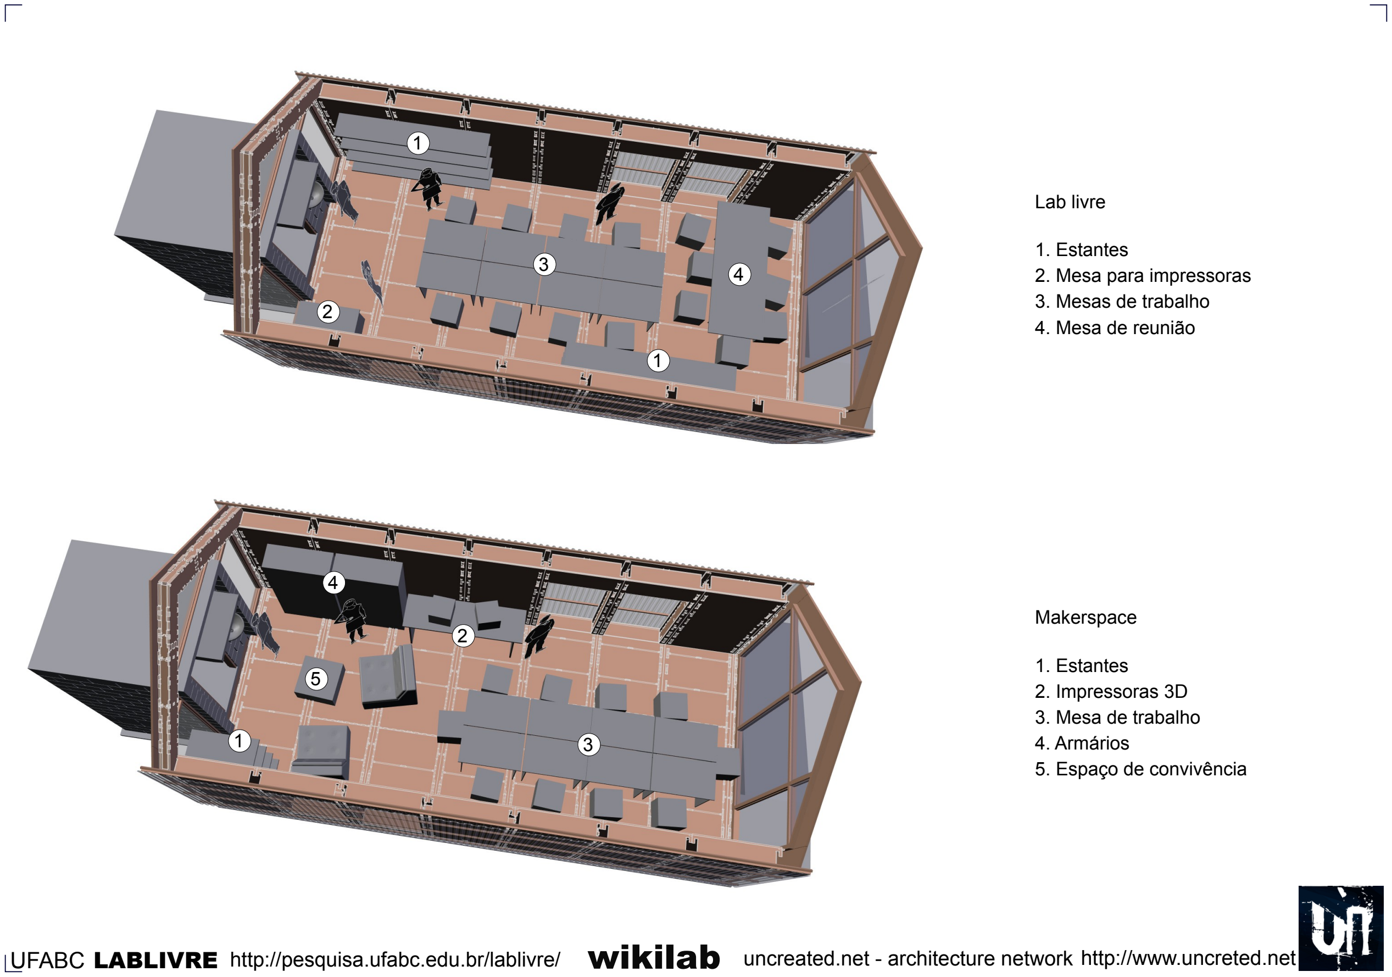
[picture p37: page 1]

Lab livre

1. Estantes
2. Mesa para impressoras
3. Mesas de trabalho
4. Mesa de reunião

UFABC LABLIVRE http://pesquisa.ufabc.edu.br/lablivre/ wikilab uncreated.net - architecture network http://www.uncreted.net

1

1

2

3 | 4

4

2

5

1 | 3

Makerspace

1. Estantes
2. Impressoras 3D
3. Mesa de trabalho
4. Armários
5. Espaço de convivência
