uncreatednet/wikilab-ufabc/apresentação/imagens/0003.jpg

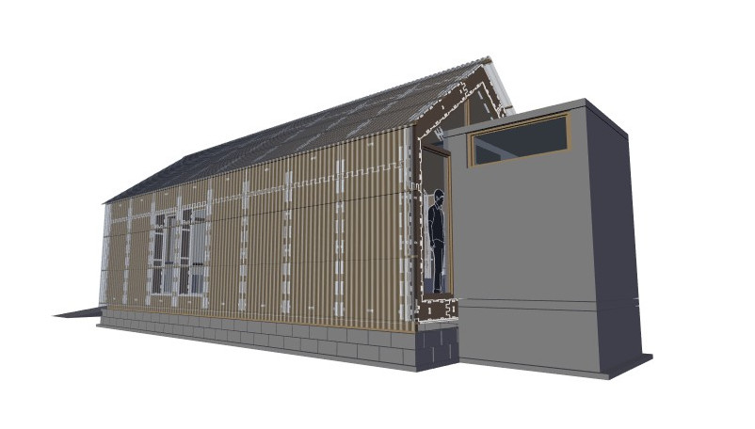
apresentação/imagens/0003.jpg
