uncreatednet/wikilab-ufabc/apresentação/imagens/0011.jpg

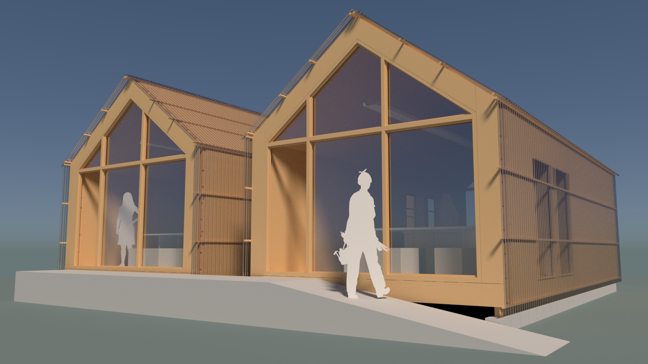
apresentação/imagens/0011.jpg
