uncreatednet/wikilab-ufabc/apresentação/imagens/0031.jpg

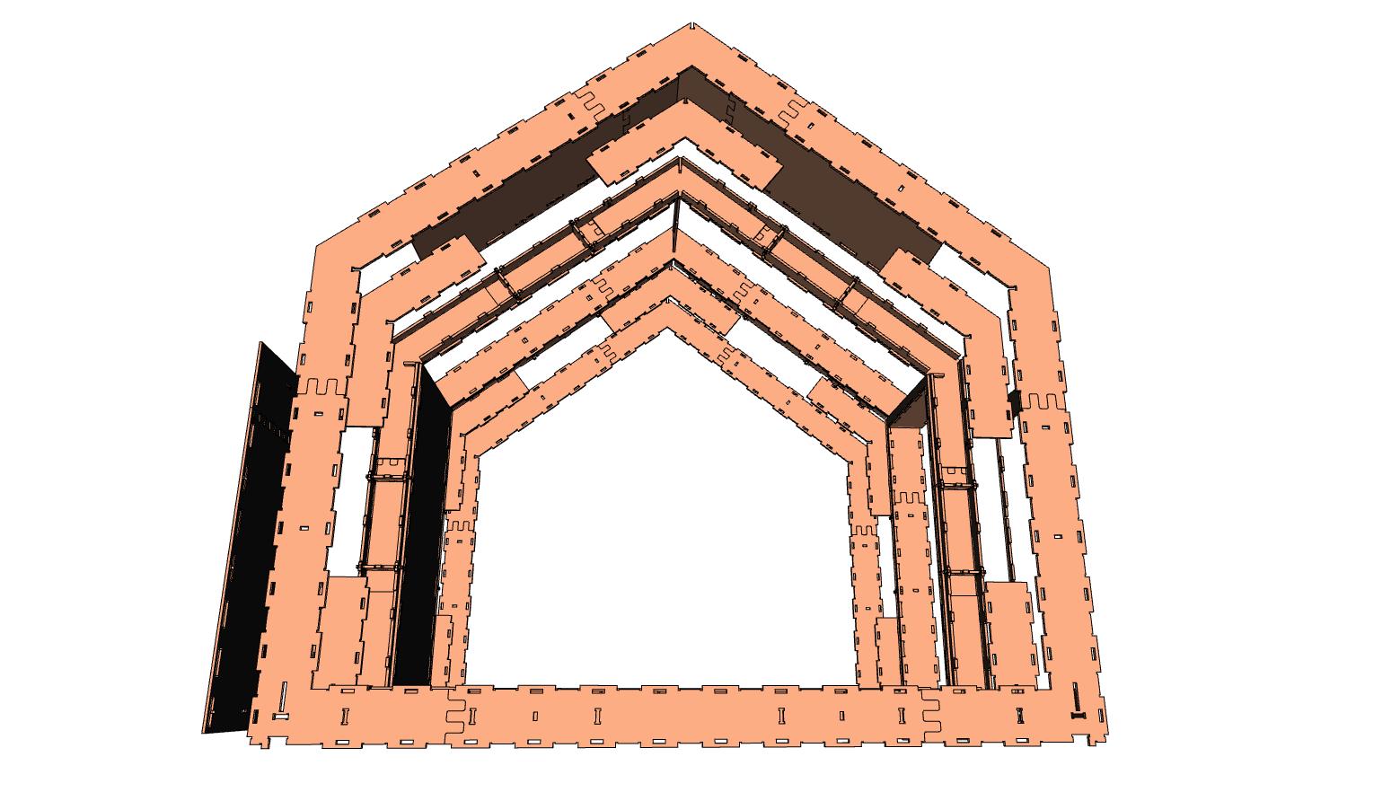
apresentação/imagens/0031.jpg
