uncreatednet/wikilab-ufabc/exemplos & referências/imagens/pinterest/0df7b17d2d5ed43fc183a7175f8ce0a0.jpg

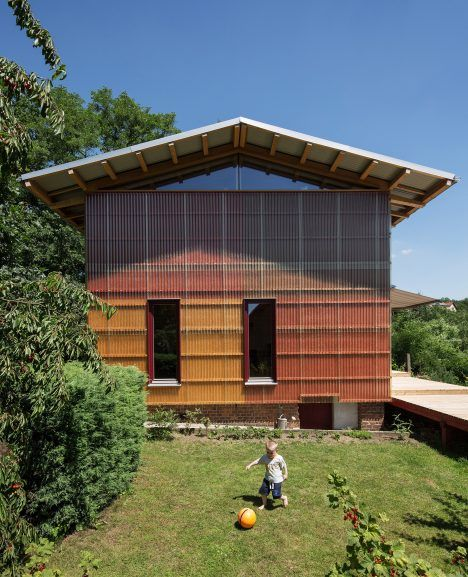
exemplos & referências/imagens/pinterest/0df7b17d2d5ed43fc183a7175f8ce0a0.jpg
