uncreatednet/wikilab-ufabc/exemplos & referências/imagens/pinterest/f43d1b91e330a0c5bda1e1e52bb69e60.jpg

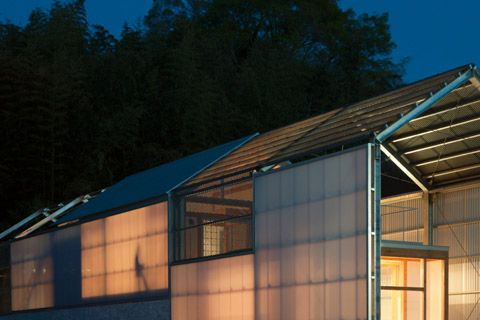
exemplos & referências/imagens/pinterest/f43d1b91e330a0c5bda1e1e52bb69e60.jpg
