uncreatednet/wikilab-ufabc/exemplos & referências/imagens/wikihouse/maxresdefault2.jpg

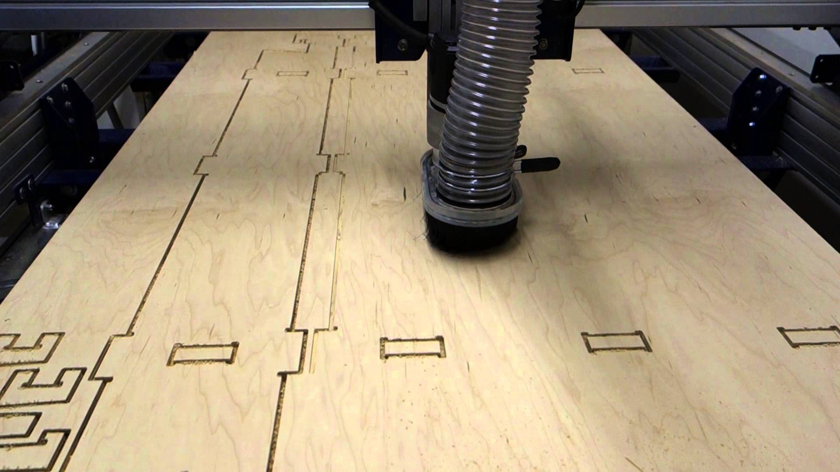
exemplos & referências/imagens/wikihouse/maxresdefault2.jpg
