uncreatednet/wikilab-ufabc/exemplos & referências/imagens/wikihouse/WikiHouse_starting_pieces.jpg

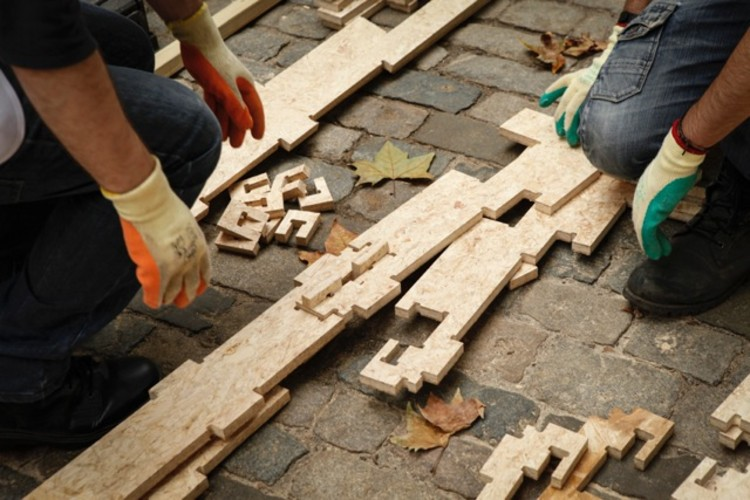
exemplos & referências/imagens/wikihouse/WikiHouse_starting_pieces.jpg
