uncreatednet/wikilab-ufabc/fotos/obra/2017.08.29/IMG_20170829_130421.jpg

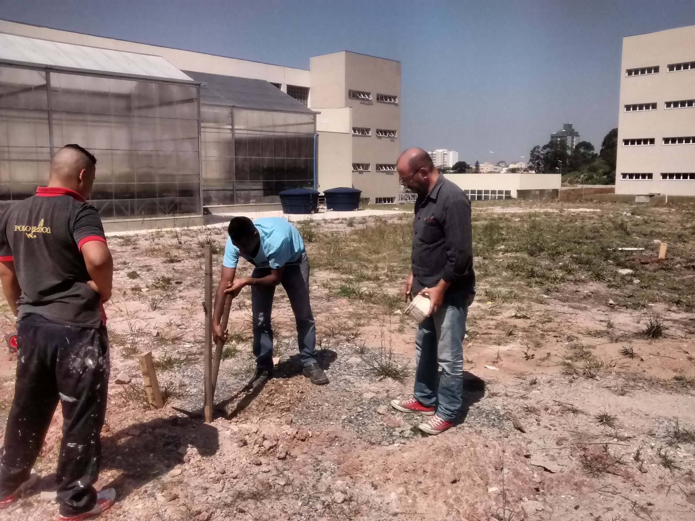
fotos/obra/2017.08.29/IMG_20170829_130421.jpg
