uncreatednet/wikilab-ufabc/fotos/obra/2017.09.04/IMG_20170904_112726.jpg

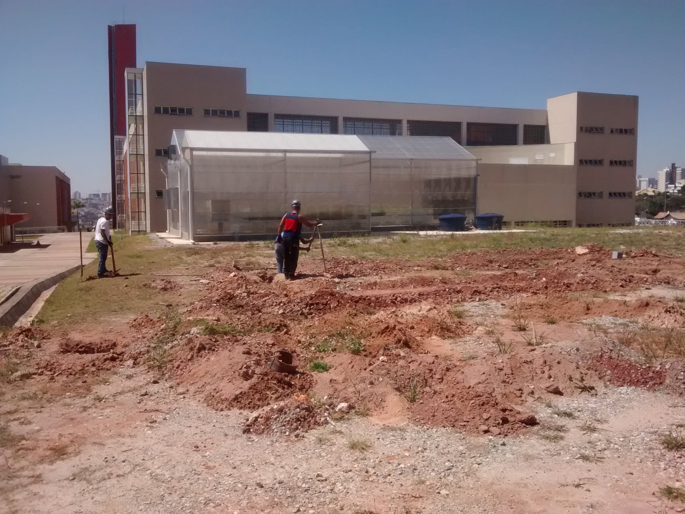
fotos/obra/2017.09.04/IMG_20170904_112726.jpg
