uncreatednet/wikilab-ufabc/fotos/obra/2017.09.12/IMG_20170912_114147.jpg

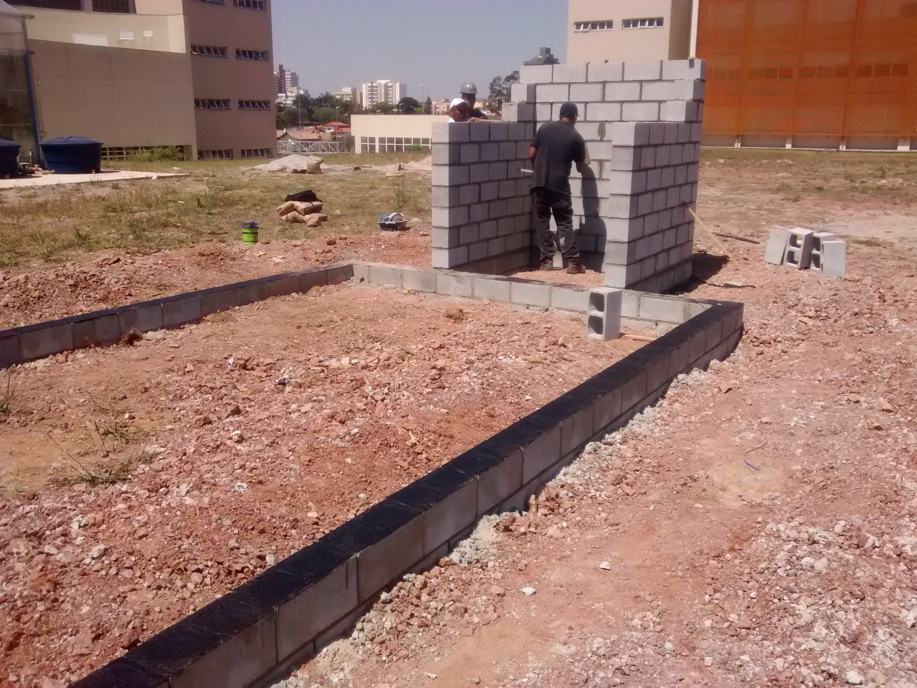
fotos/obra/2017.09.12/IMG_20170912_114147.jpg
