uncreatednet/wikilab-ufabc/fotos/obra/2017.09.13/IMG_20170913_134859.jpg

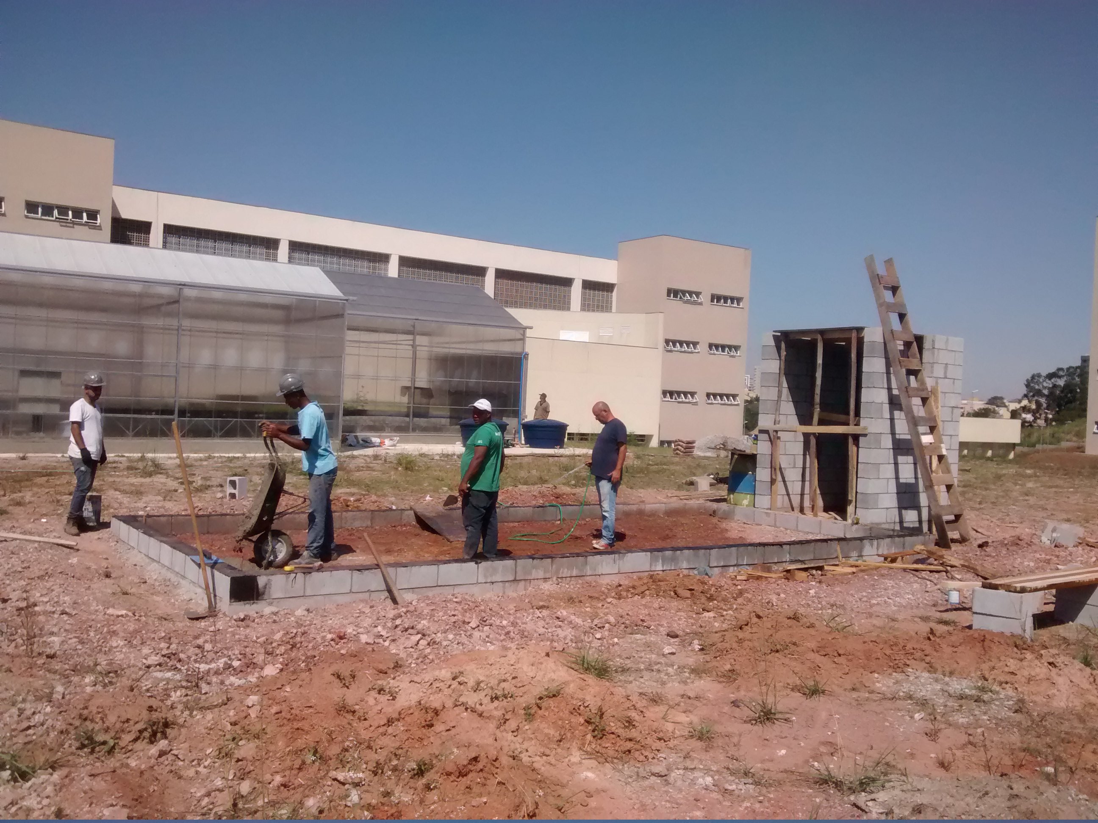
fotos/obra/2017.09.13/IMG_20170913_134859.jpg
