uncreatednet/wikilab-ufabc/fotos/obra/2017.09.14/IMG_20170914_144347.jpg

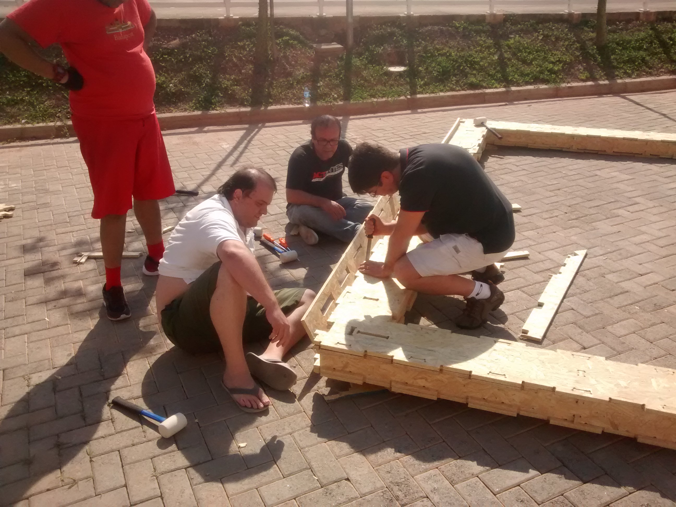
fotos/obra/2017.09.14/IMG_20170914_144347.jpg
