uncreatednet/wikilab-ufabc/fotos/obra/2017.09.15/21458060_10154816783790913_4699687172734866973_o.jpg

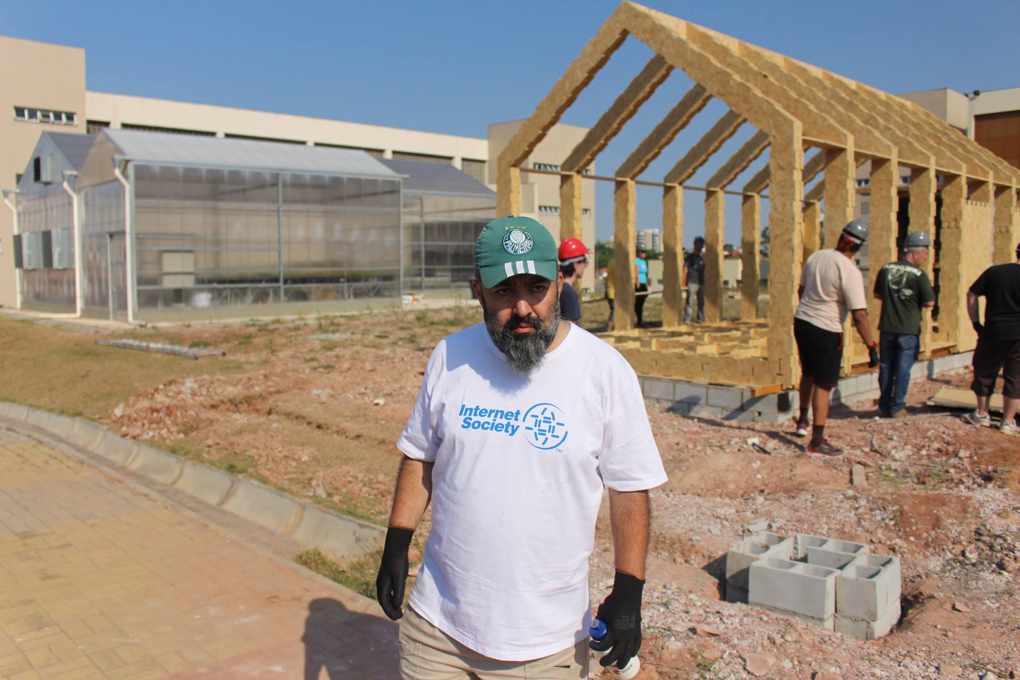
fotos/obra/2017.09.15/21458060_10154816783790913_4699687172734866973_o.jpg
