uncreatednet/wikilab-ufabc/fotos/obra/2017.09.15/21729027_10154816782985913_1850600895178764134_o.jpg

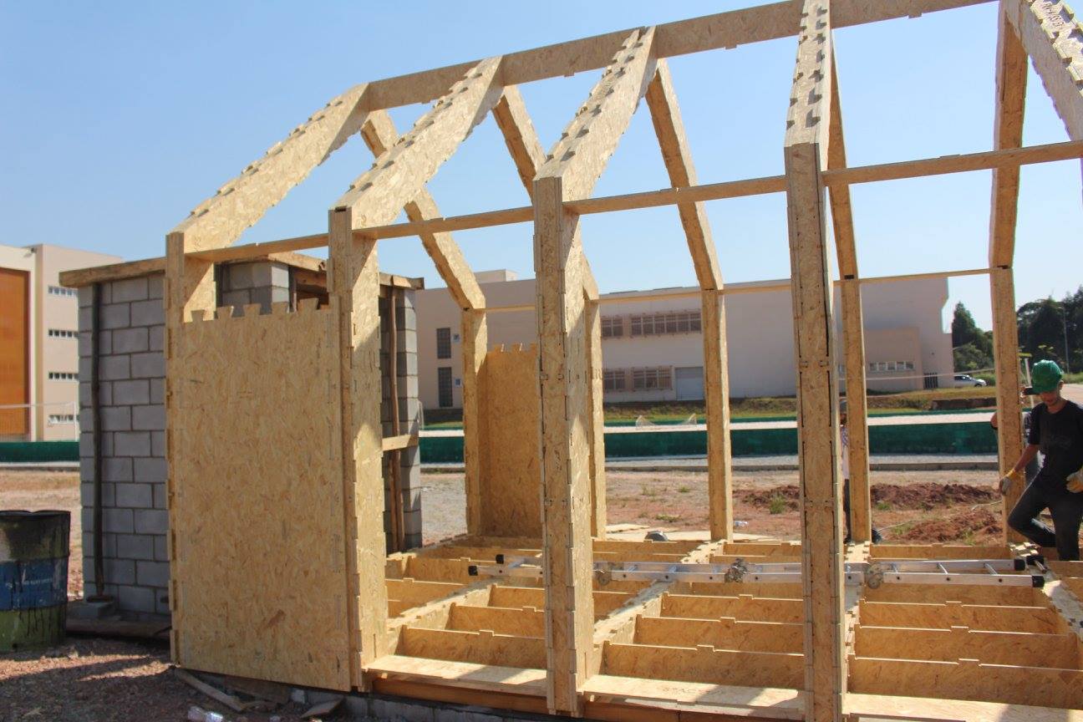
fotos/obra/2017.09.15/21729027_10154816782985913_1850600895178764134_o.jpg
