uncreatednet/wikilab-ufabc/fotos/obra/2017.09.15/21752830_10154816785540913_7124701061406327190_o.jpg

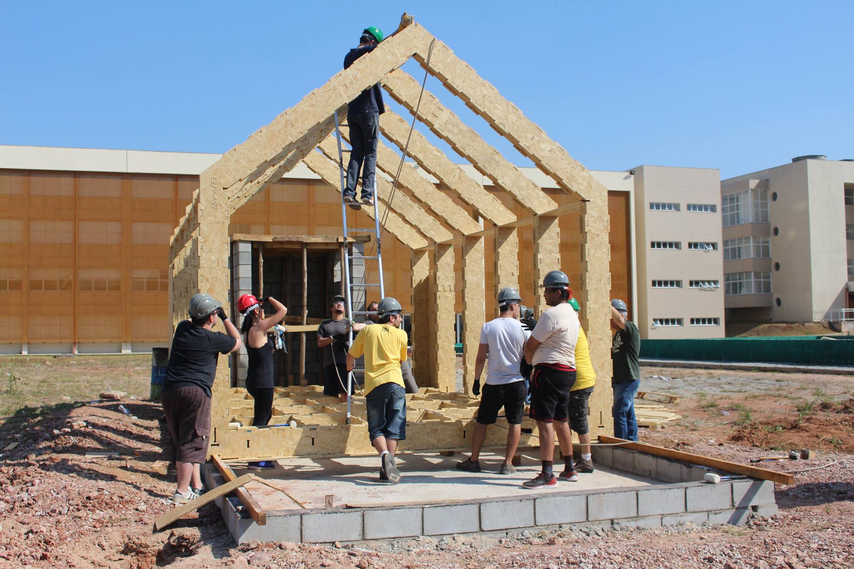
fotos/obra/2017.09.15/21752830_10154816785540913_7124701061406327190_o.jpg
