uncreatednet/wikilab-ufabc/fotos/obra/2017.09.15/21753210_10154816785710913_2247293847857239255_o.jpg

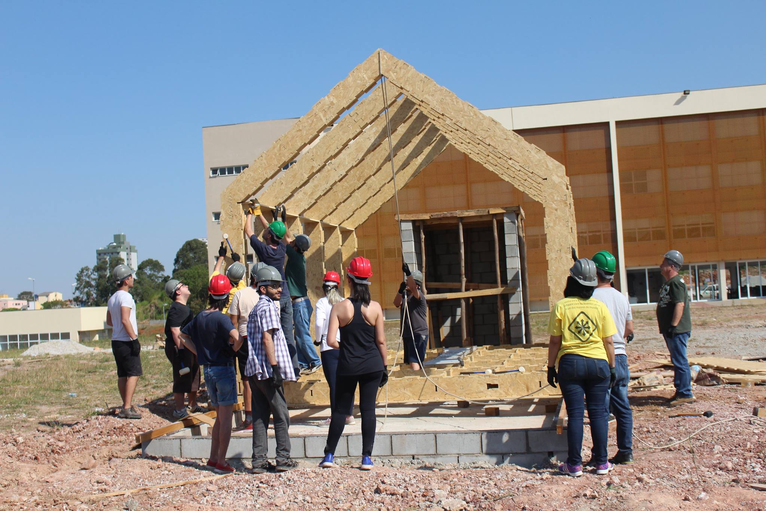
fotos/obra/2017.09.15/21753210_10154816785710913_2247293847857239255_o.jpg
