uncreatednet/wikilab-ufabc/fotos/obra/2017.09.15/21765426_10154816782690913_83979979562893622_o.jpg

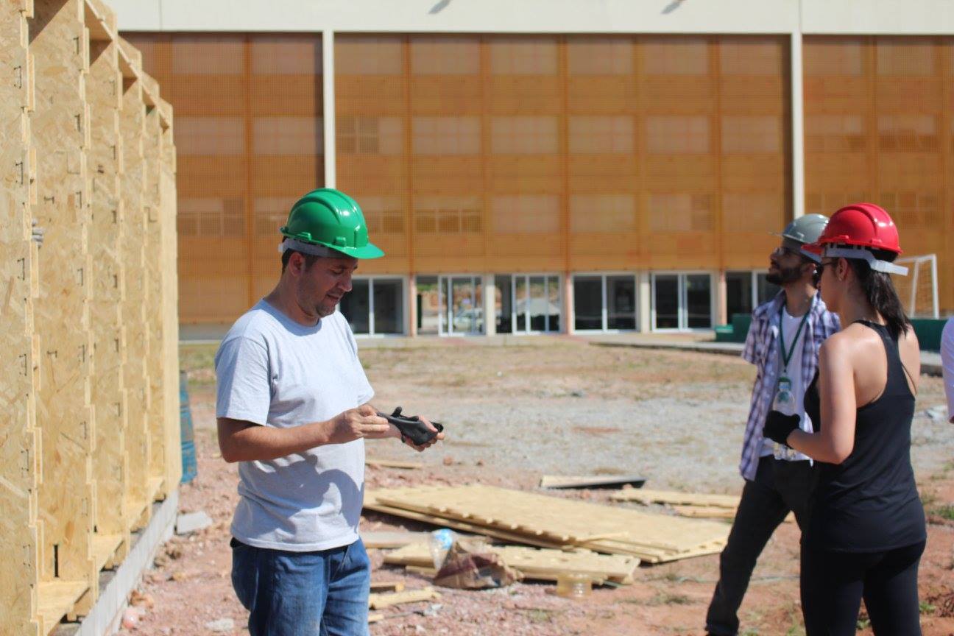
fotos/obra/2017.09.15/21765426_10154816782690913_83979979562893622_o.jpg
