uncreatednet/wikilab-ufabc/fotos/obra/2017.09.15/IMG-20170915-WA0026.jpg

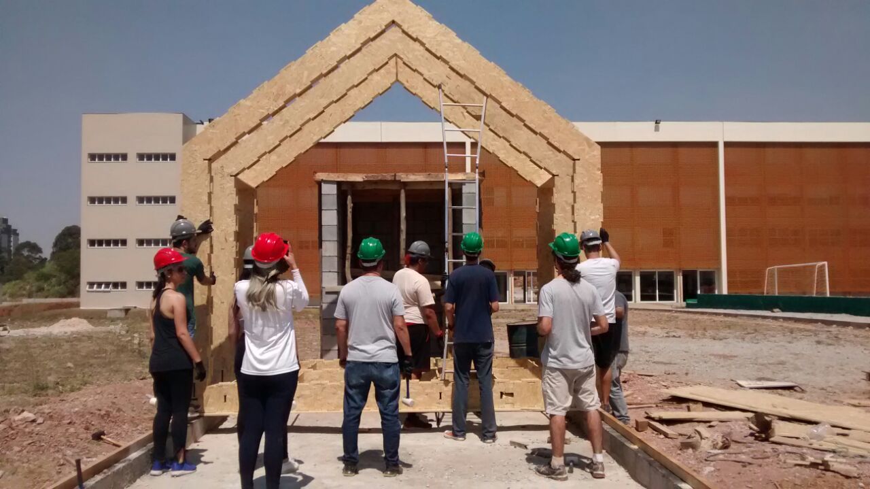
fotos/obra/2017.09.15/IMG-20170915-WA0026.jpg
