uncreatednet/wikilab-ufabc/fotos/obra/2017.09.15/IMG-20170915-WA0027.jpg

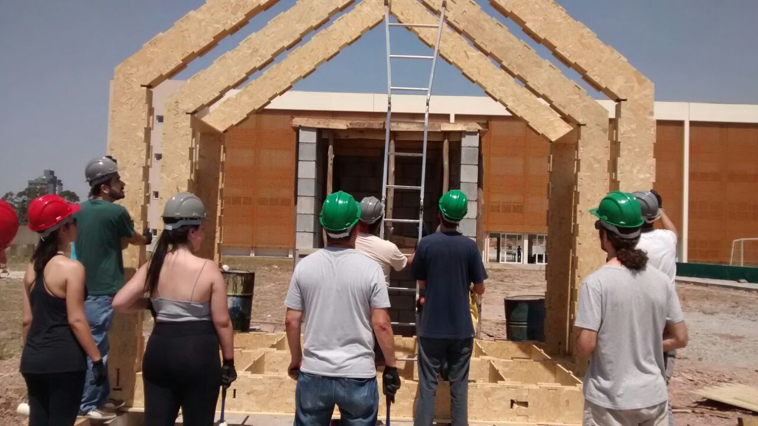
fotos/obra/2017.09.15/IMG-20170915-WA0027.jpg
