uncreatednet/wikilab-ufabc/fotos/obra/2017.09.23/IMG-20170924-WA0014.jpg

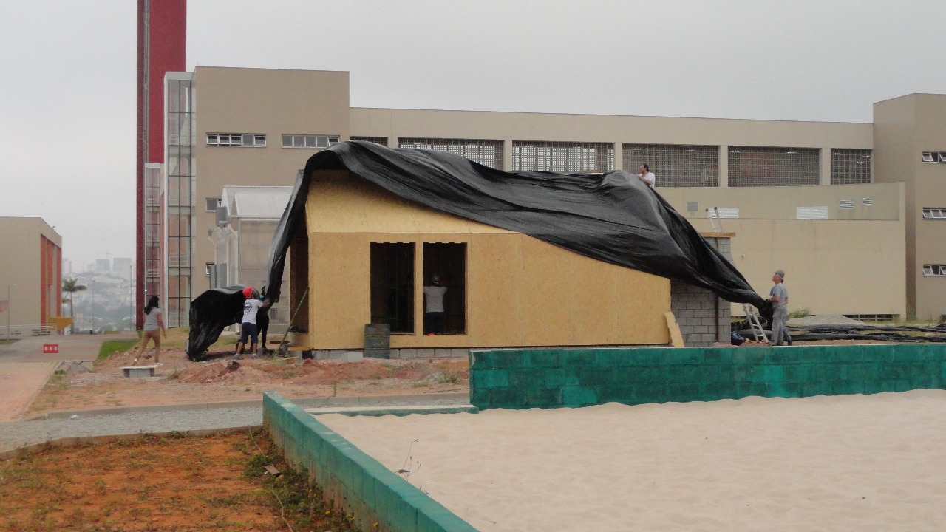
fotos/obra/2017.09.23/IMG-20170924-WA0014.jpg
