uncreatednet/wikilab-ufabc/fotos/obra/2017.09.23/IMG_20170923_152951.jpg

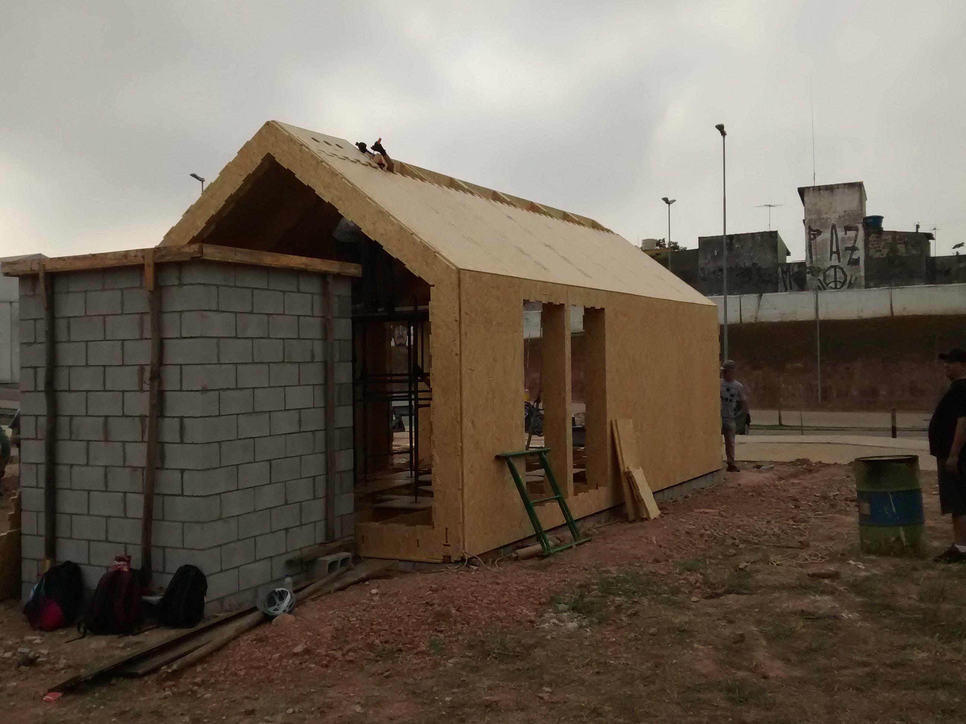
fotos/obra/2017.09.23/IMG_20170923_152951.jpg
