uncreatednet/wikilab-ufabc/fotos/obra/2017.09.27/IMG_20170927_140853.jpg

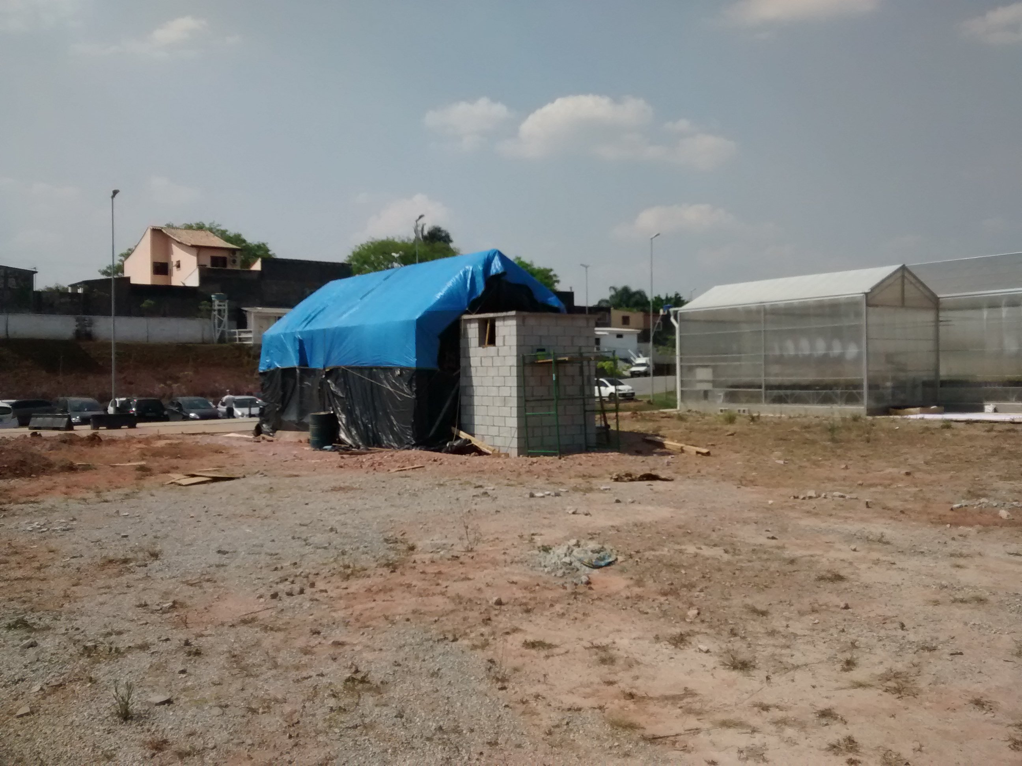
fotos/obra/2017.09.27/IMG_20170927_140853.jpg
