uncreatednet/wikilab-ufabc/fotos/obra/2017.09.28/IMG_20170928_115627.jpg

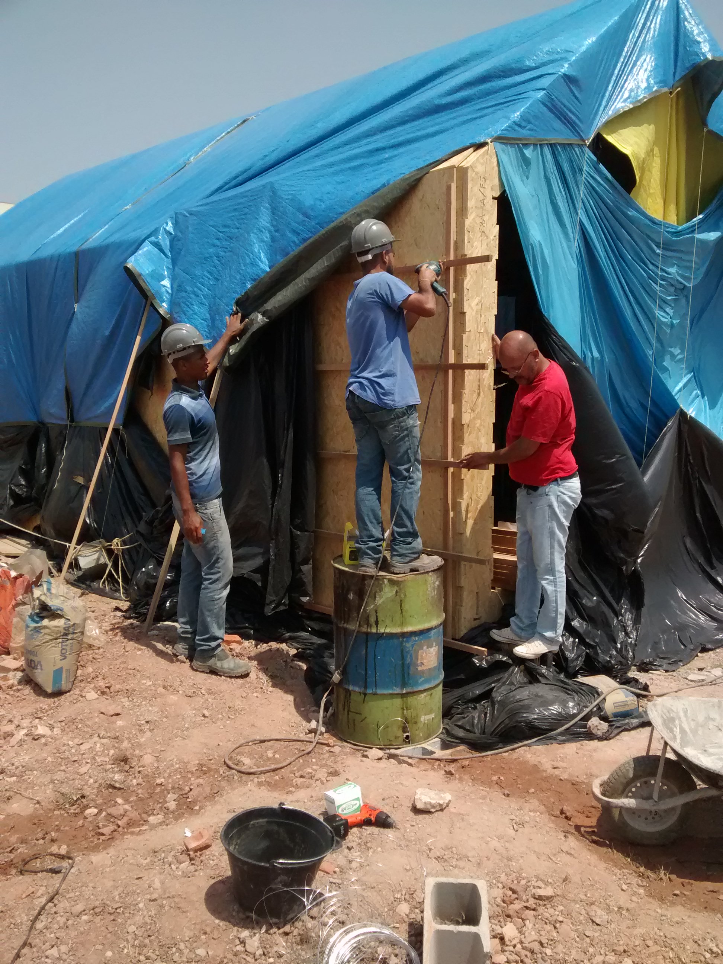
fotos/obra/2017.09.28/IMG_20170928_115627.jpg
