uncreatednet/wikilab-ufabc/fotos/obra/2017.09.28/IMG_20170928_115649.jpg

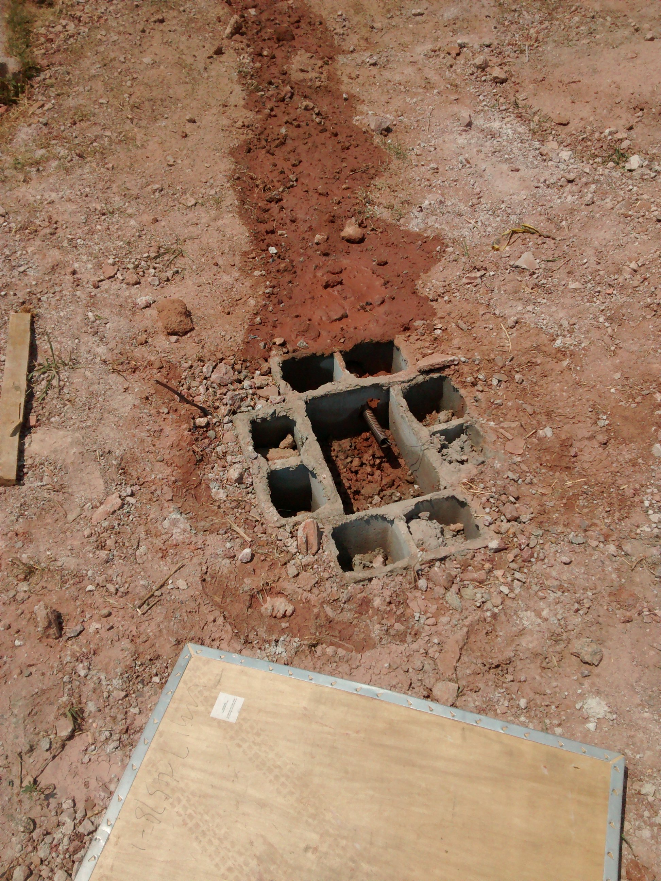
fotos/obra/2017.09.28/IMG_20170928_115649.jpg
