uncreatednet/wikilab-ufabc/fotos/obra/2017.10.03/IMG_20171003_153929.jpg

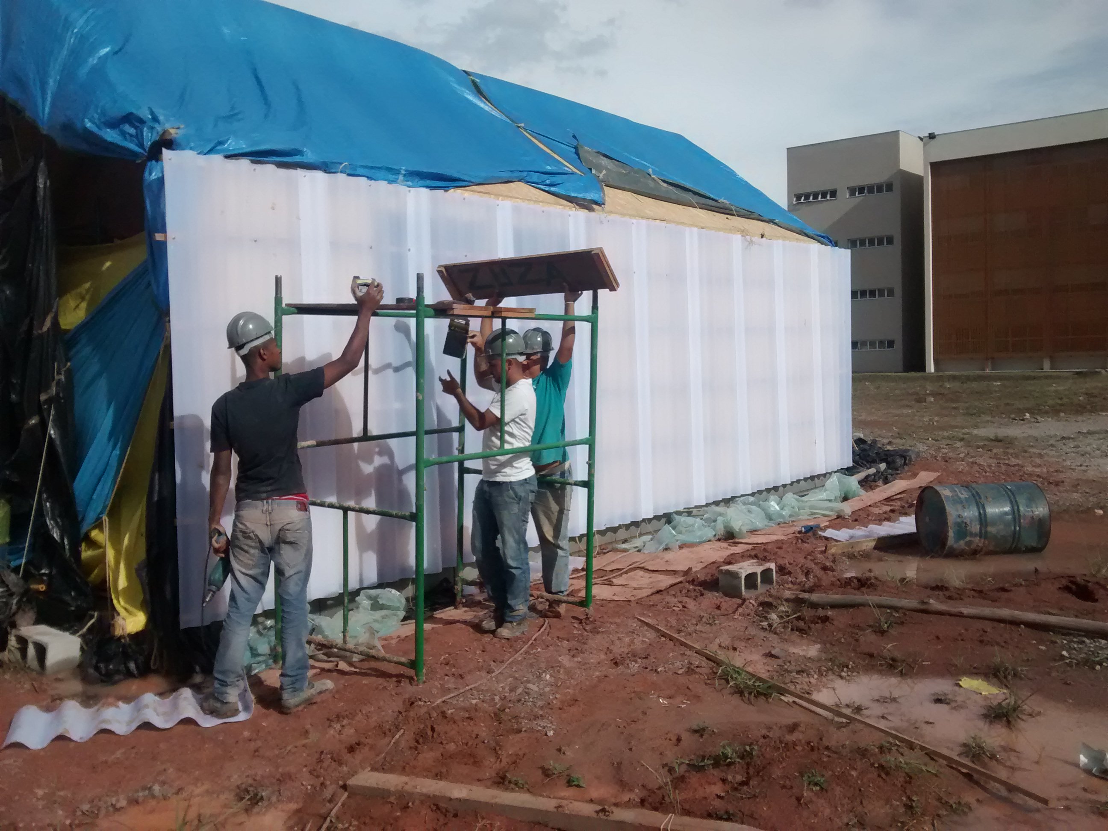
fotos/obra/2017.10.03/IMG_20171003_153929.jpg
