uncreatednet/wikilab-ufabc/fotos/obra/2017.10.03/IMG_20171003_155036.jpg

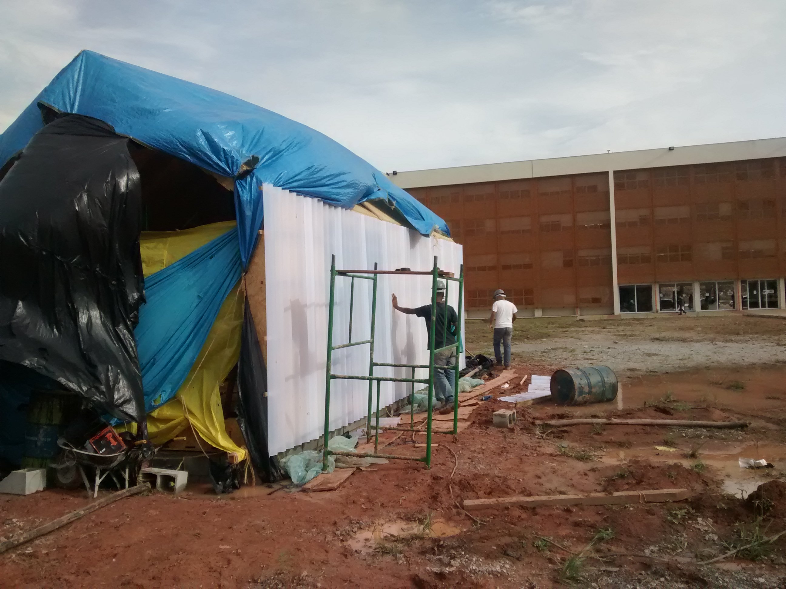
fotos/obra/2017.10.03/IMG_20171003_155036.jpg
