uncreatednet/wikilab-ufabc/fotos/obra/2017.10.04/IMG_20171004_105743.jpg

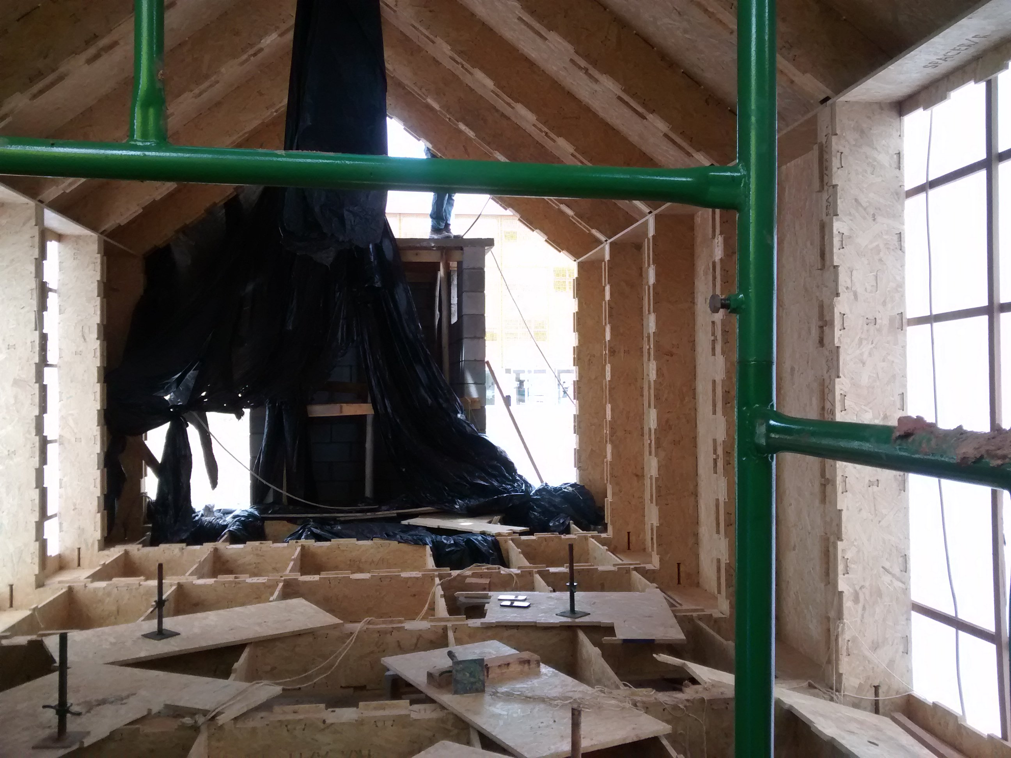
fotos/obra/2017.10.04/IMG_20171004_105743.jpg
