uncreatednet/wikilab-ufabc/fotos/obra/2017.10.06/IMG_20171006_143916.jpg

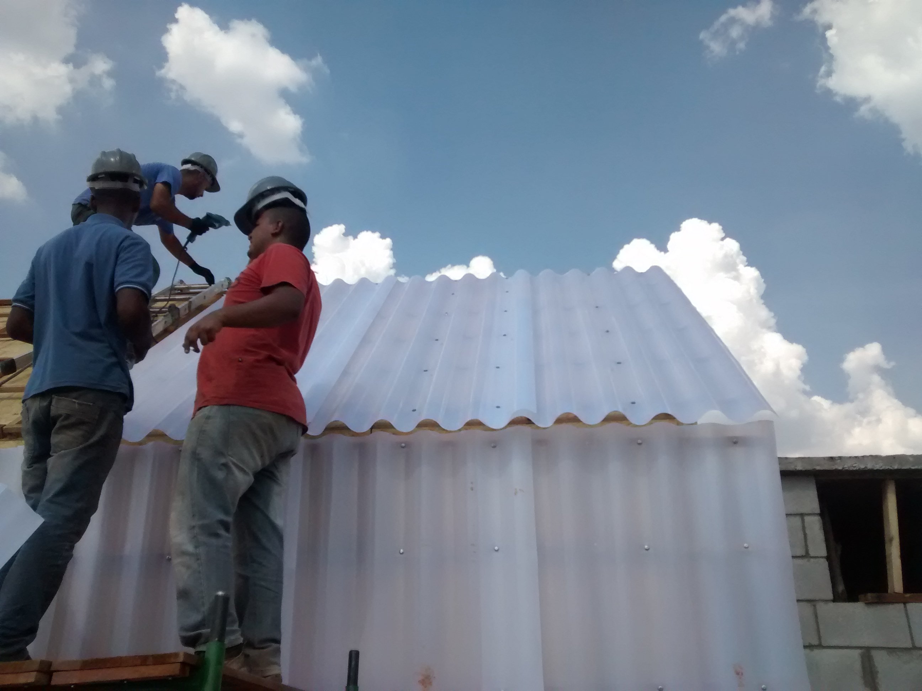
fotos/obra/2017.10.06/IMG_20171006_143916.jpg
