uncreatednet/wikilab-ufabc/fotos/obra/2017.10.09/IMG_20171009_153100.jpg

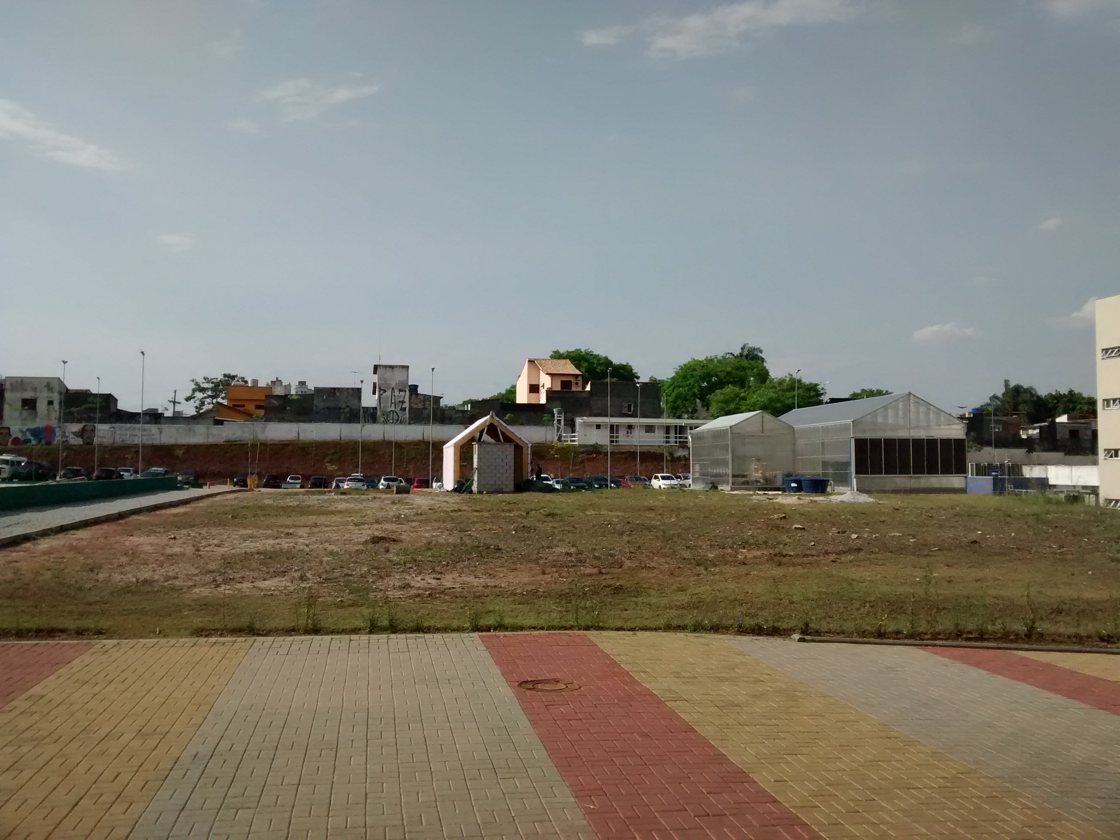
fotos/obra/2017.10.09/IMG_20171009_153100.jpg
