uncreatednet/wikilab-ufabc/fotos/obra/2017.11.07/IMG_20171107_162448.jpg

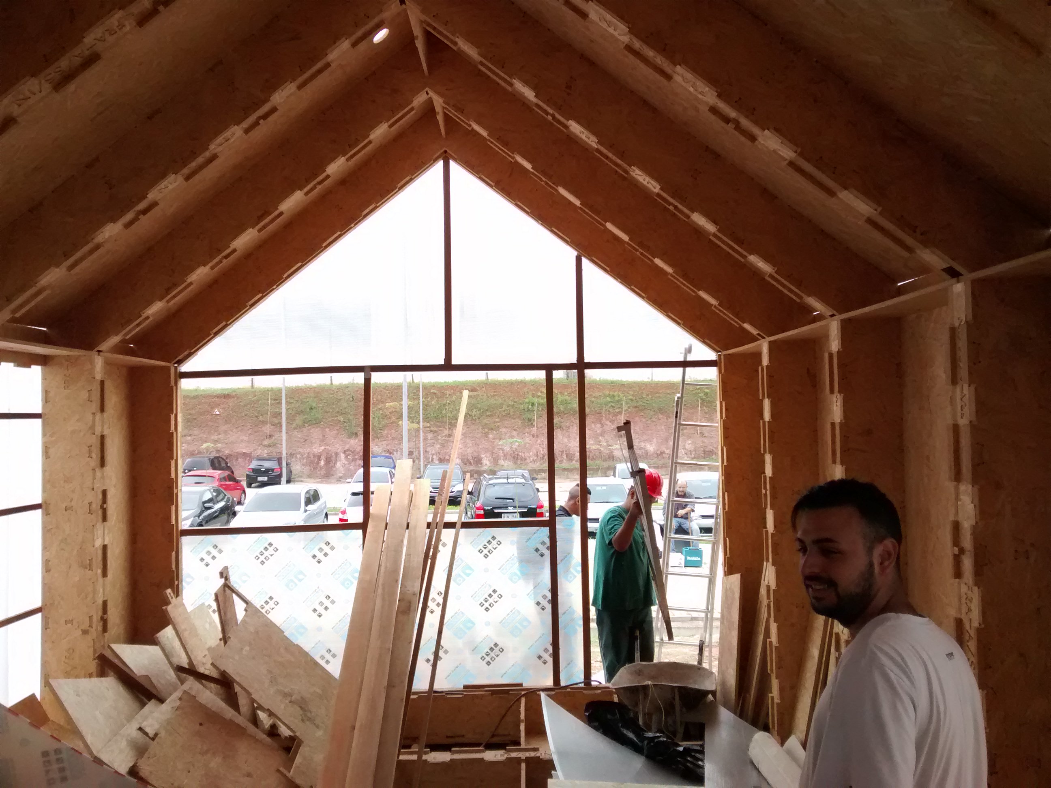
fotos/obra/2017.11.07/IMG_20171107_162448.jpg
