uncreatednet/wikilab-ufabc/fotos/obra/2017.11.08/IMG_20171108_163928.jpg

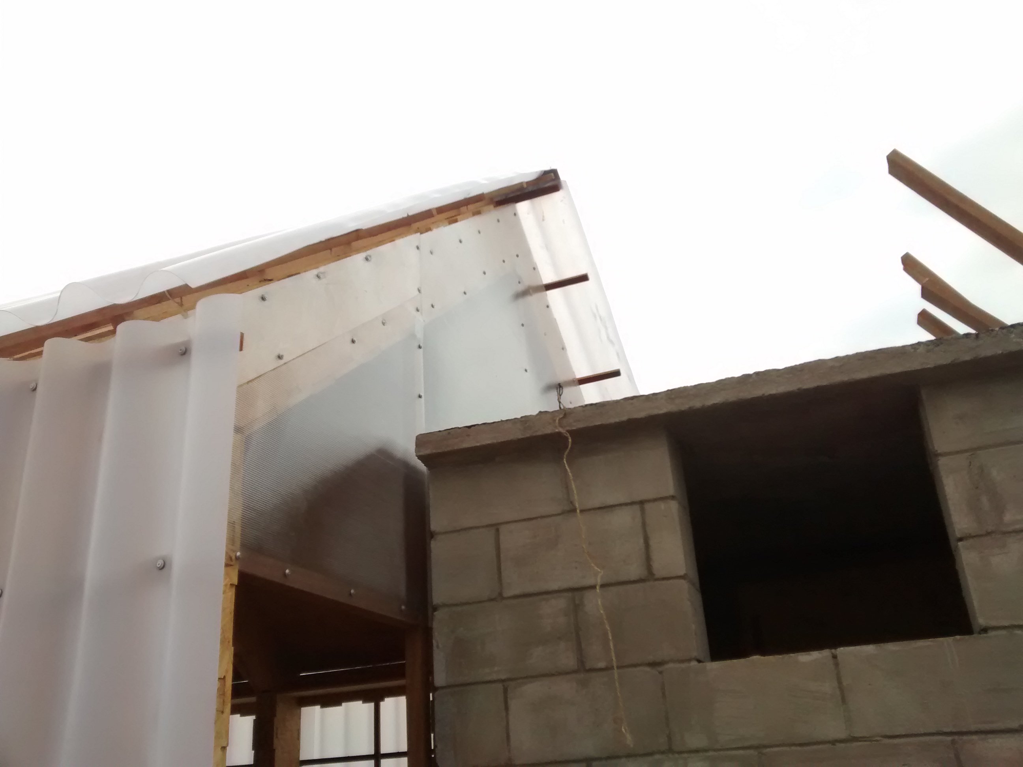
fotos/obra/2017.11.08/IMG_20171108_163928.jpg
