uncreatednet/wikilab-ufabc/fotos/obra/2017.11.09/IMG_20171109_163646.jpg

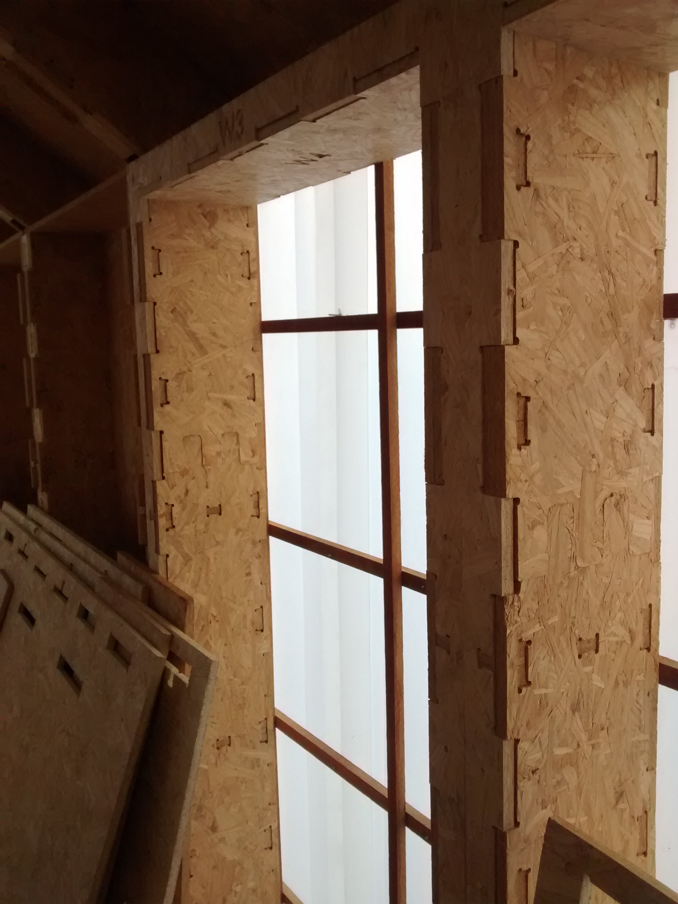
fotos/obra/2017.11.09/IMG_20171109_163646.jpg
