uncreatednet/wikilab-ufabc/fotos/obra/2017.11.10/IMG_20171110_190153.jpg

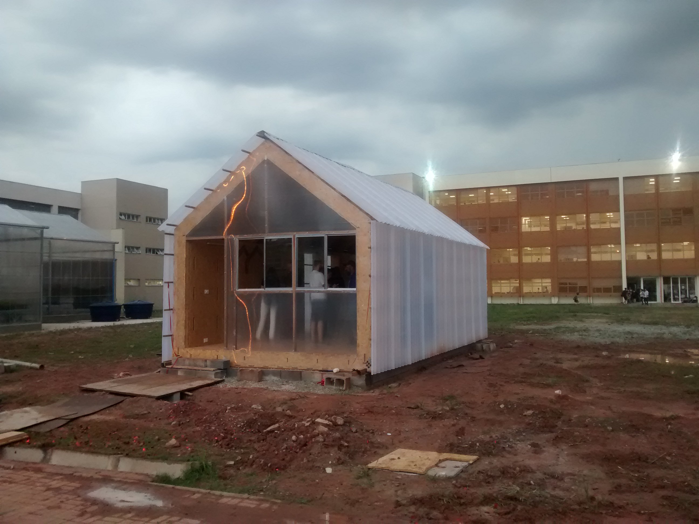
fotos/obra/2017.11.10/IMG_20171110_190153.jpg
