uncreatednet/wikilab-ufabc/fotos/obra/2017.11.29/IMG_20171129_092342.jpg

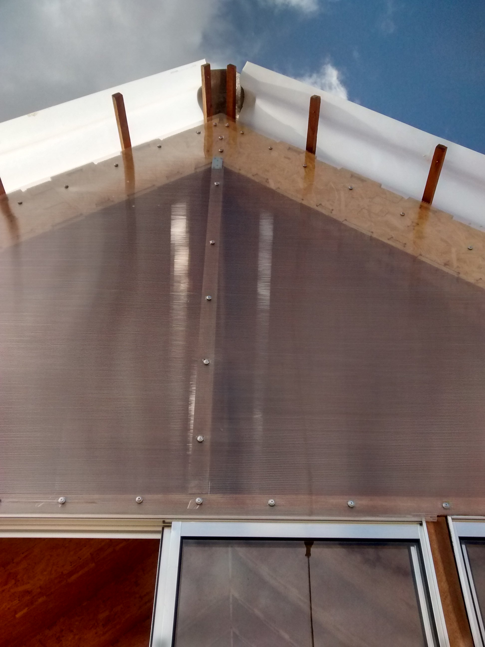
fotos/obra/2017.11.29/IMG_20171129_092342.jpg
