uncreatednet/wikilab-ufabc/fotos/obra/2017.12.06/IMG_20171206_141005.jpg

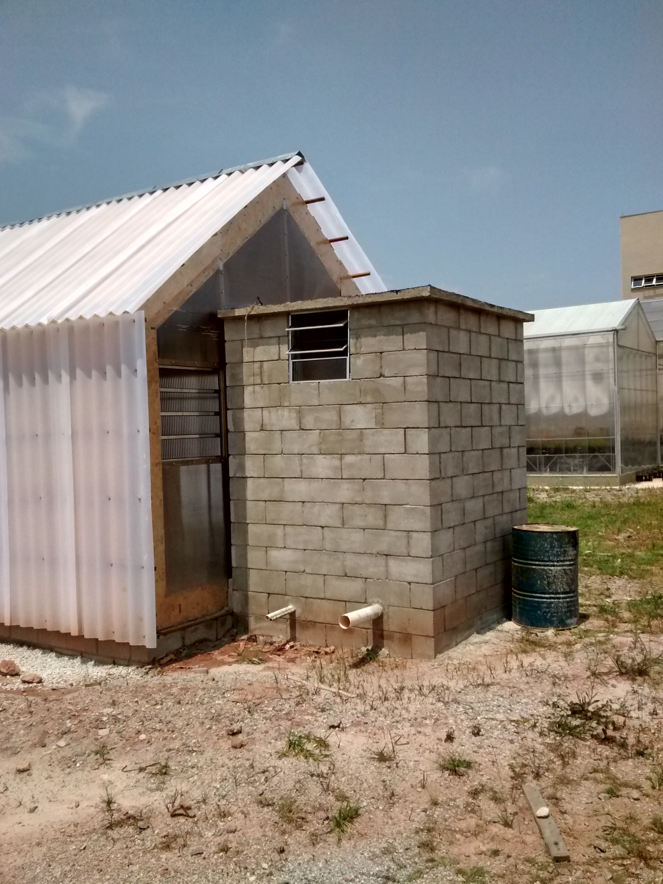
fotos/obra/2017.12.06/IMG_20171206_141005.jpg
