uncreatednet/wikilab-ufabc/fotos/obra/2018.02.23/IMG_20180223_161056.jpg

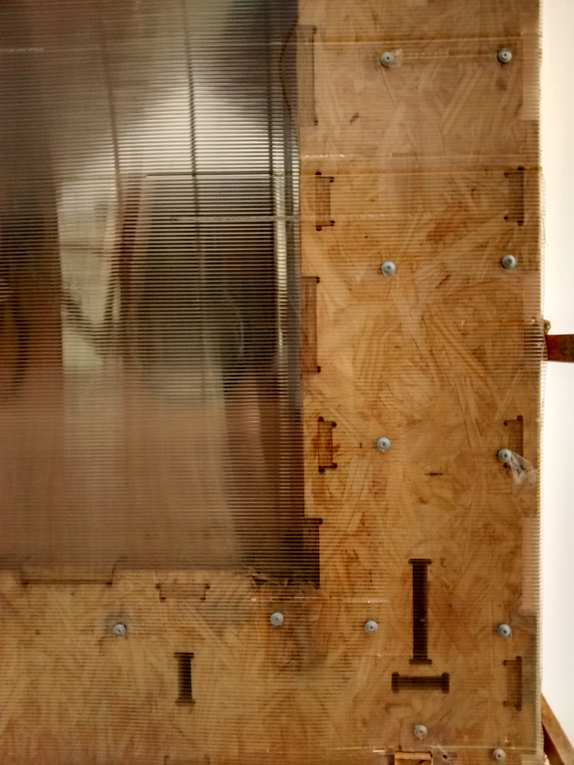
fotos/obra/2018.02.23/IMG_20180223_161056.jpg
