uncreatednet/wikilab-ufabc/fotos/obra/2018.05.09/IMG_20180508_192111.jpg

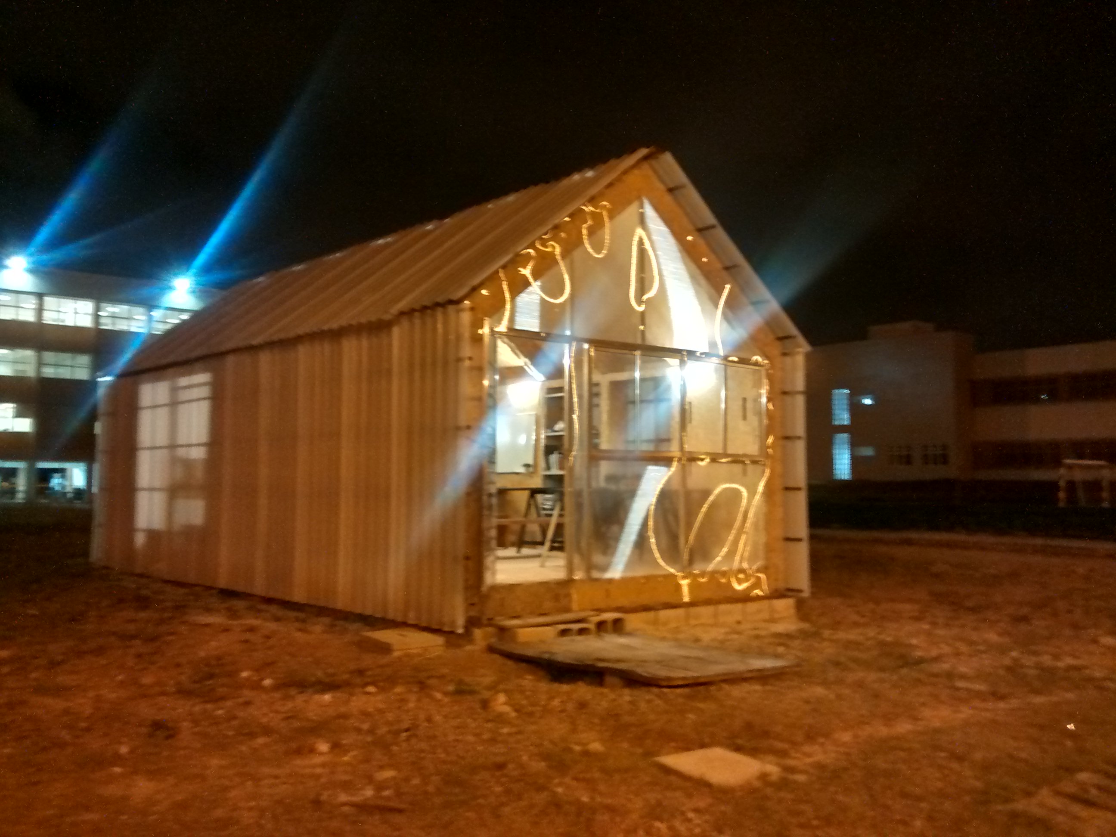
fotos/obra/2018.05.09/IMG_20180508_192111.jpg
