uncreatednet/wikilab-ufabc/fotos/obra/2018.05.09/IMG_20180508_202243.jpg

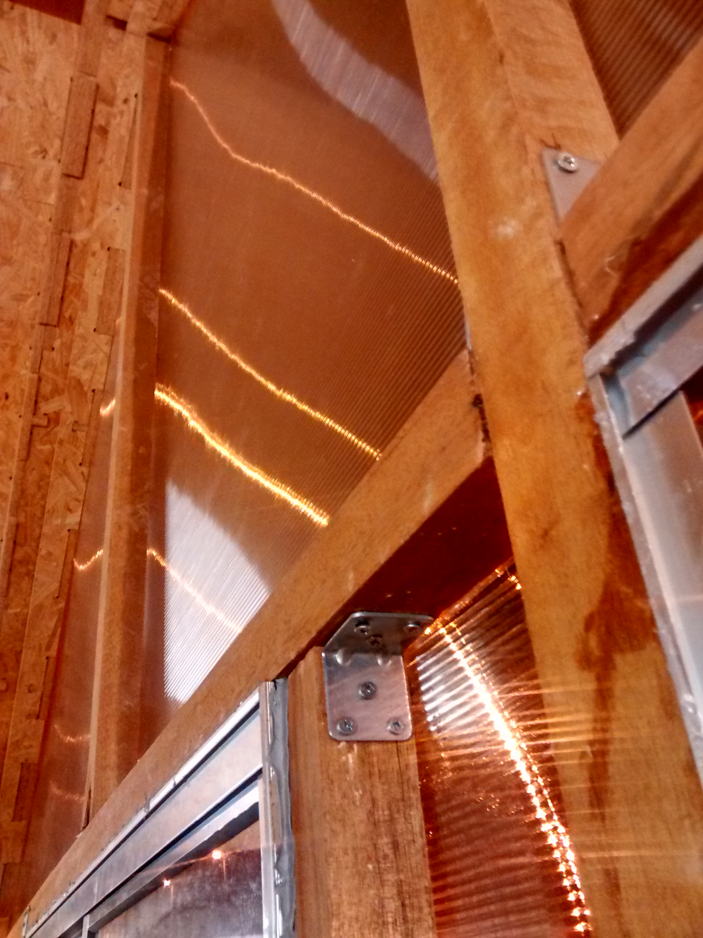
fotos/obra/2018.05.09/IMG_20180508_202243.jpg
