uncreatednet/wikilab-ufabc/fotos/parafusadeira/parafusos2.jpg

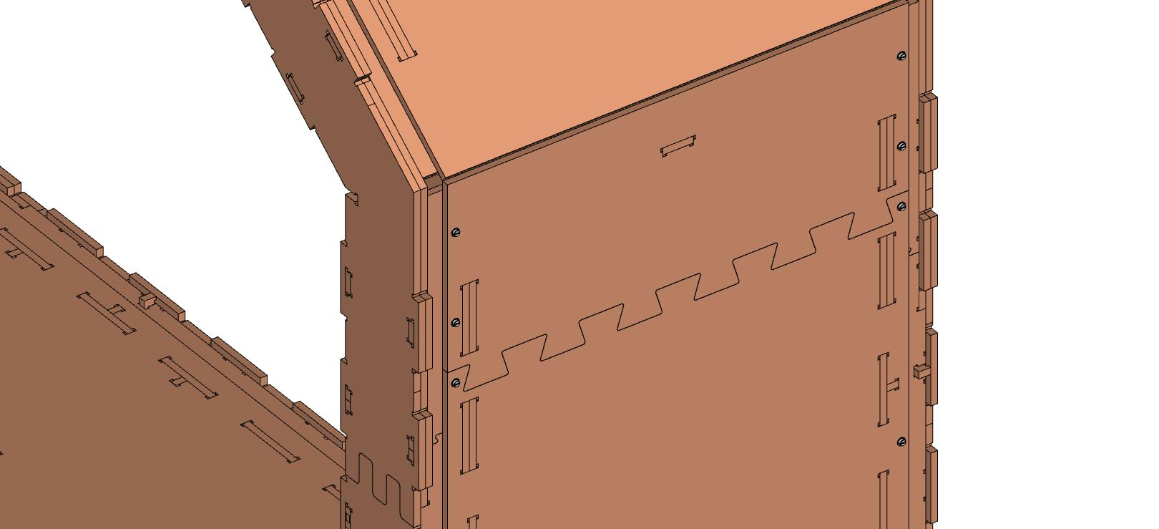
fotos/parafusadeira/parafusos2.jpg
