uncreatednet/wikilab-ufabc/fotos/parafusadeira/parafusos3.jpg

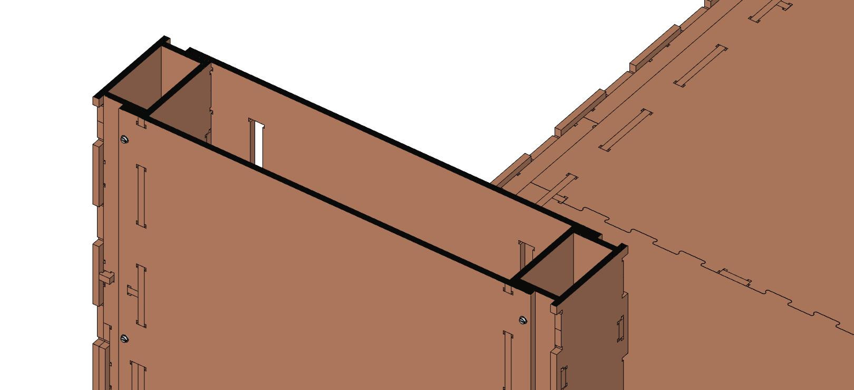
fotos/parafusadeira/parafusos3.jpg
