uncreatednet/wikilab-ufabc/fotos/parafusadeira/parafusos4.jpg

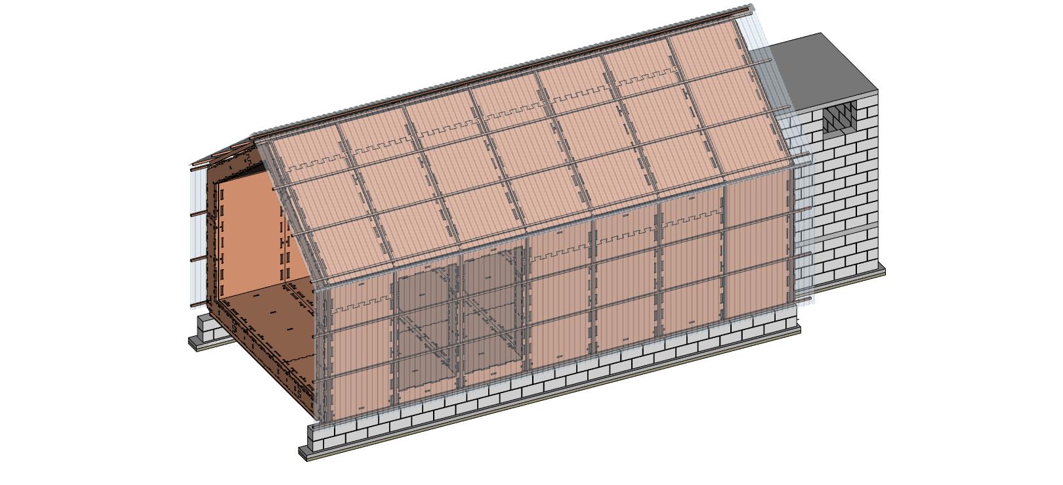
fotos/parafusadeira/parafusos4.jpg
