uncreatednet/wikilab-ufabc/fotos/Pioneerswoning - Leiden/IMG_20180206_141211.jpg

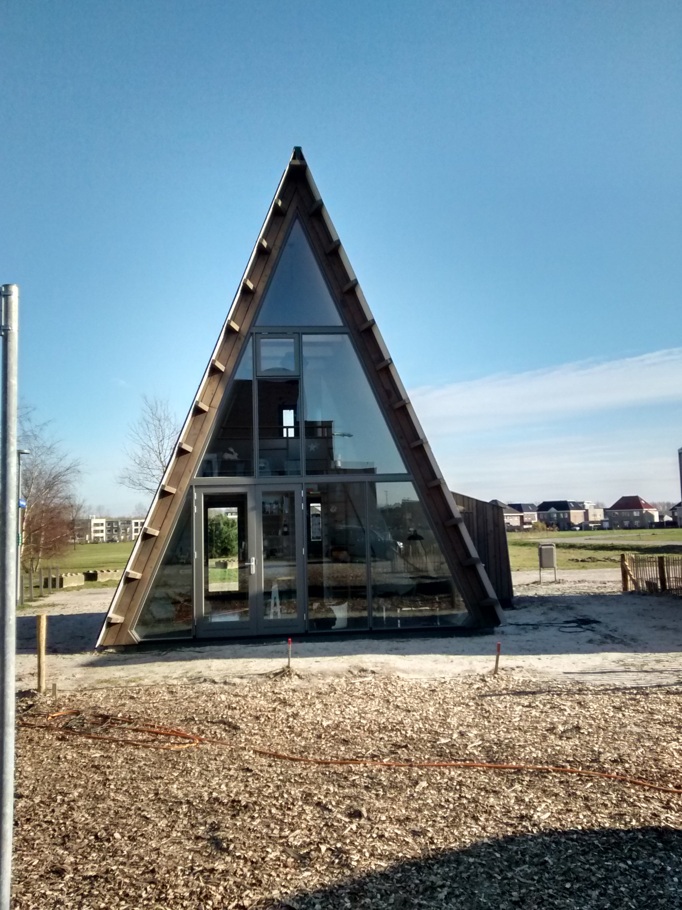
fotos/Pioneerswoning - Leiden/IMG_20180206_141211.jpg
