uncreatednet/wikilab-ufabc/fotos/Pioneerswoning - Leiden/IMG_20180206_141528.jpg

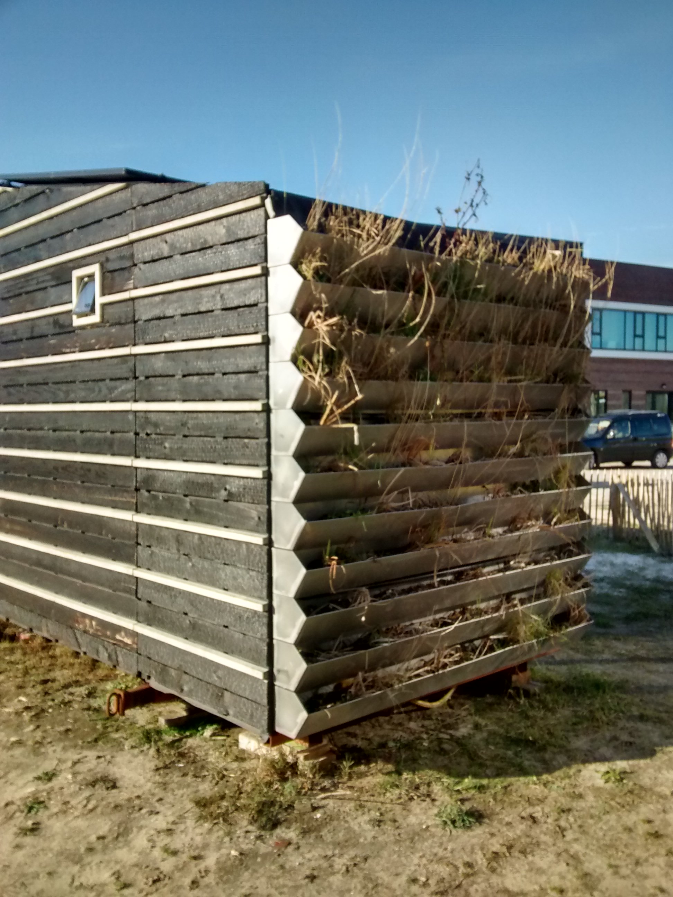
fotos/Pioneerswoning - Leiden/IMG_20180206_141528.jpg
