uncreatednet/wikilab-ufabc/fotos/Pioneerswoning - Leiden/IMG_20180206_141745.jpg

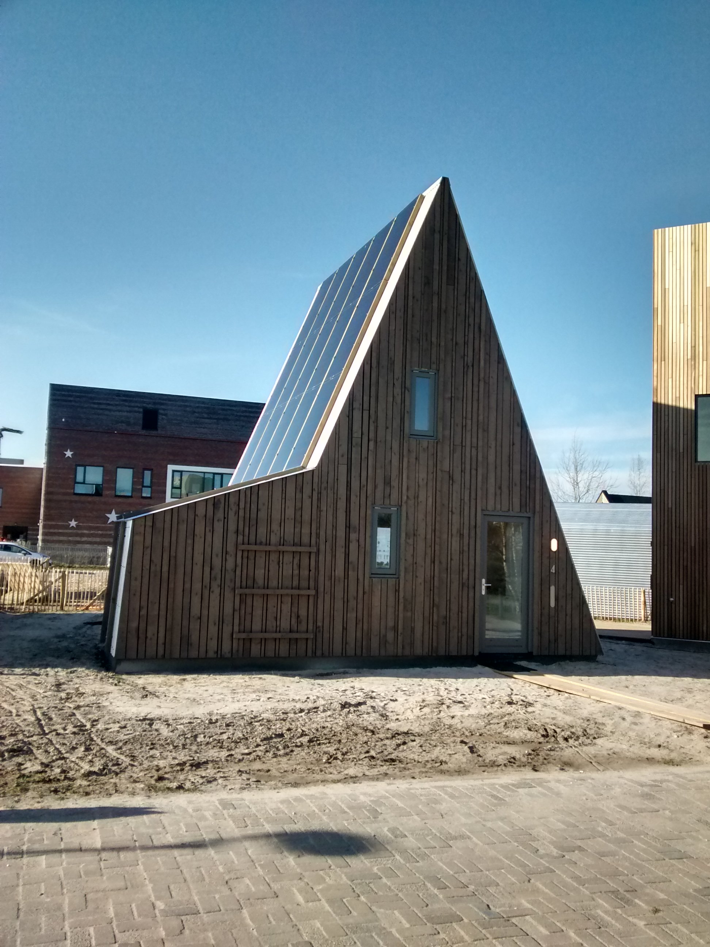
fotos/Pioneerswoning - Leiden/IMG_20180206_141745.jpg
