uncreatednet/wikilab-ufabc/fotos/Pioneerswoning - Leiden/IMG_20180206_142446.jpg

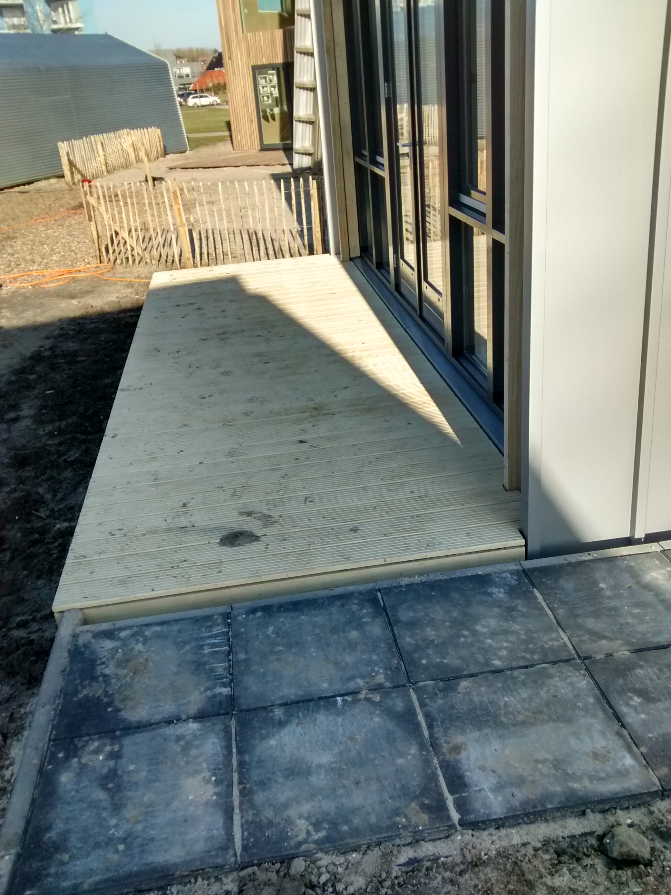
fotos/Pioneerswoning - Leiden/IMG_20180206_142446.jpg
