uncreatednet/wikilab-ufabc/fotos/Pioneerswoning - Leiden/IMG_20180206_152425.jpg

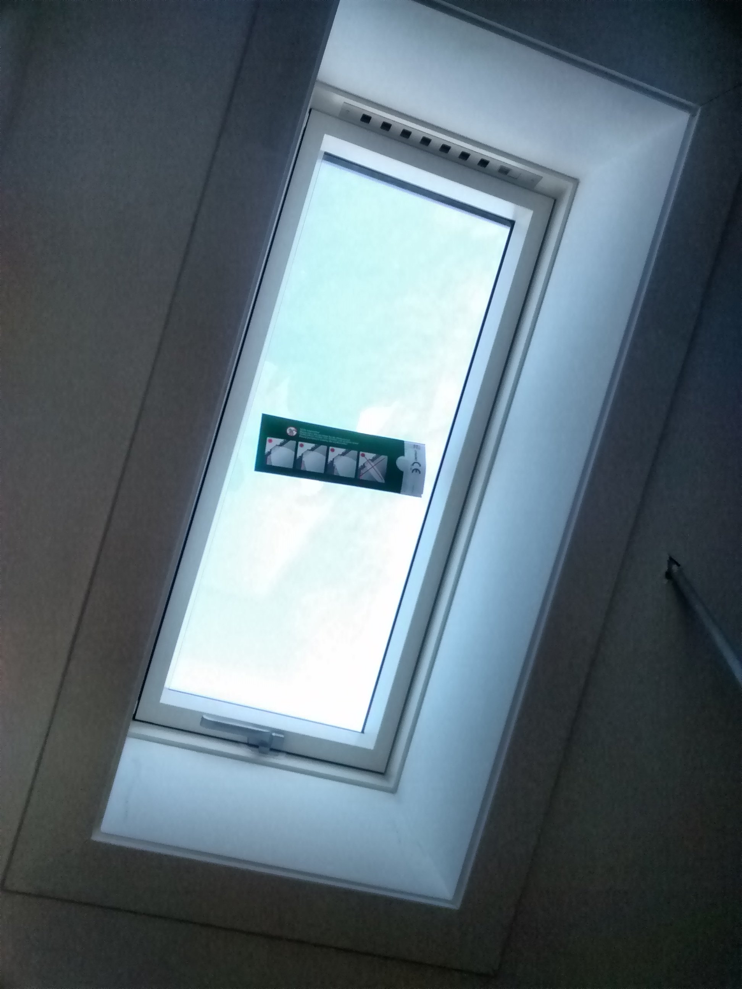
fotos/Pioneerswoning - Leiden/IMG_20180206_152425.jpg
