uncreatednet/wikilab-ufabc/fotos/Pioneerswoning - Leiden/IMG_20180206_152510.jpg

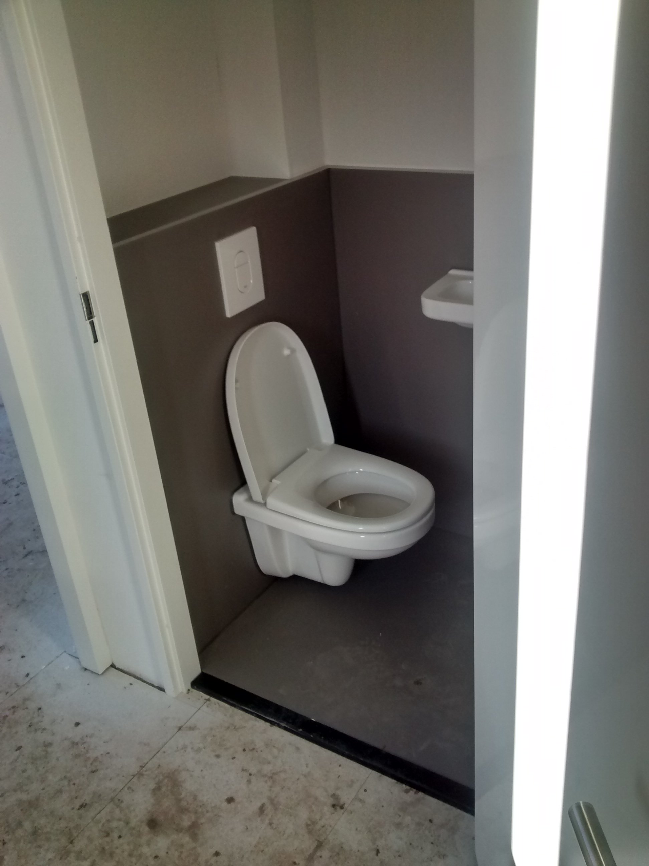
fotos/Pioneerswoning - Leiden/IMG_20180206_152510.jpg
