uncreatednet/wikilab-ufabc/fotos/Pioneerswoning - Leiden/IMG_20180206_152827.jpg

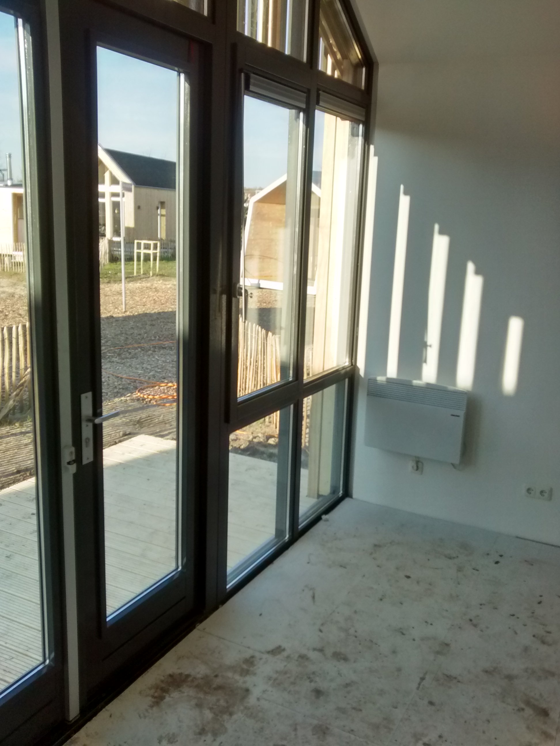
fotos/Pioneerswoning - Leiden/IMG_20180206_152827.jpg
