uncreatednet/wikilab-ufabc/fotos/relatorio-2019.03.15/IMG_20190315_112246.jpg

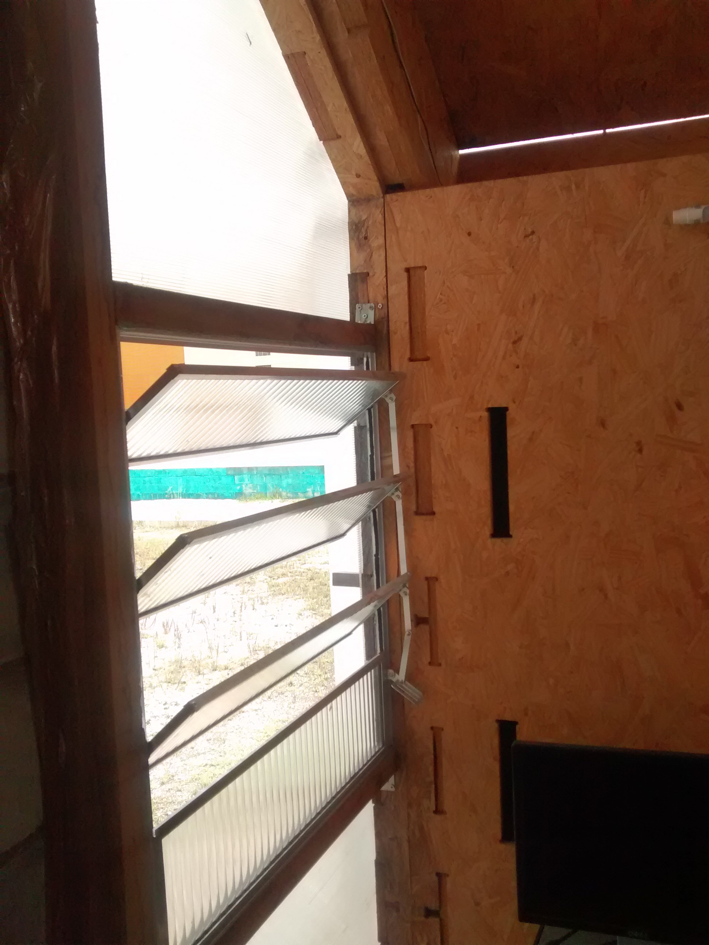
fotos/relatorio-2019.03.15/IMG_20190315_112246.jpg
