uncreatednet/wikilab-ufabc/fotos/relatorio-2019.03.15/IMG_20190315_120129.jpg

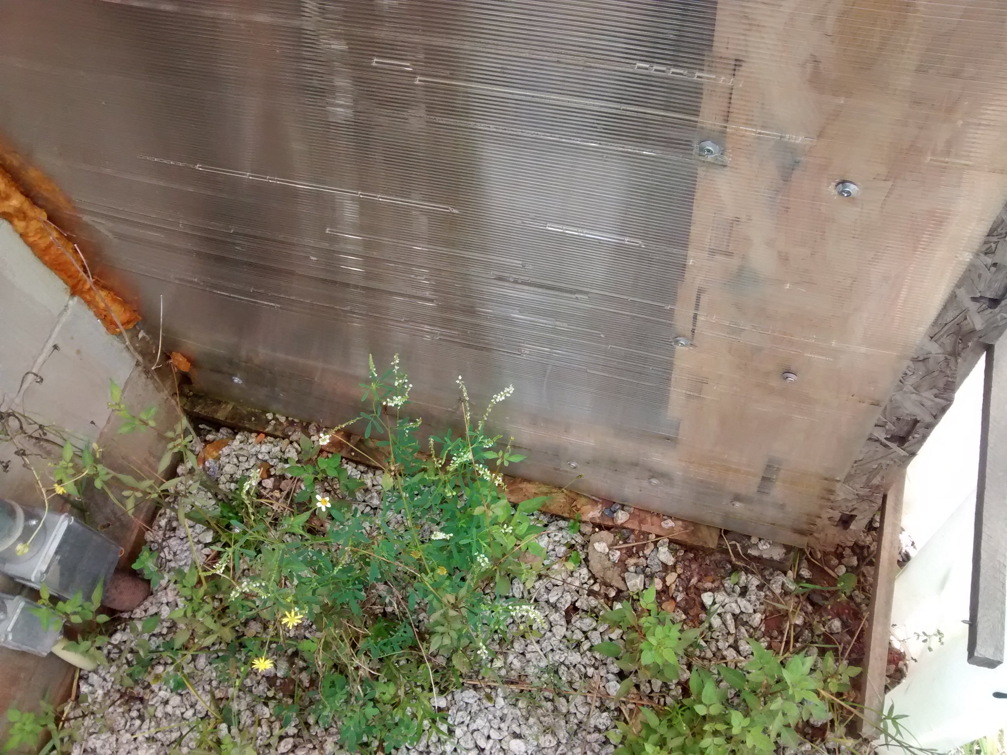
fotos/relatorio-2019.03.15/IMG_20190315_120129.jpg
