uncreatednet/wikilab-ufabc/fotos/terreno/IMG_20170131_151235.jpg

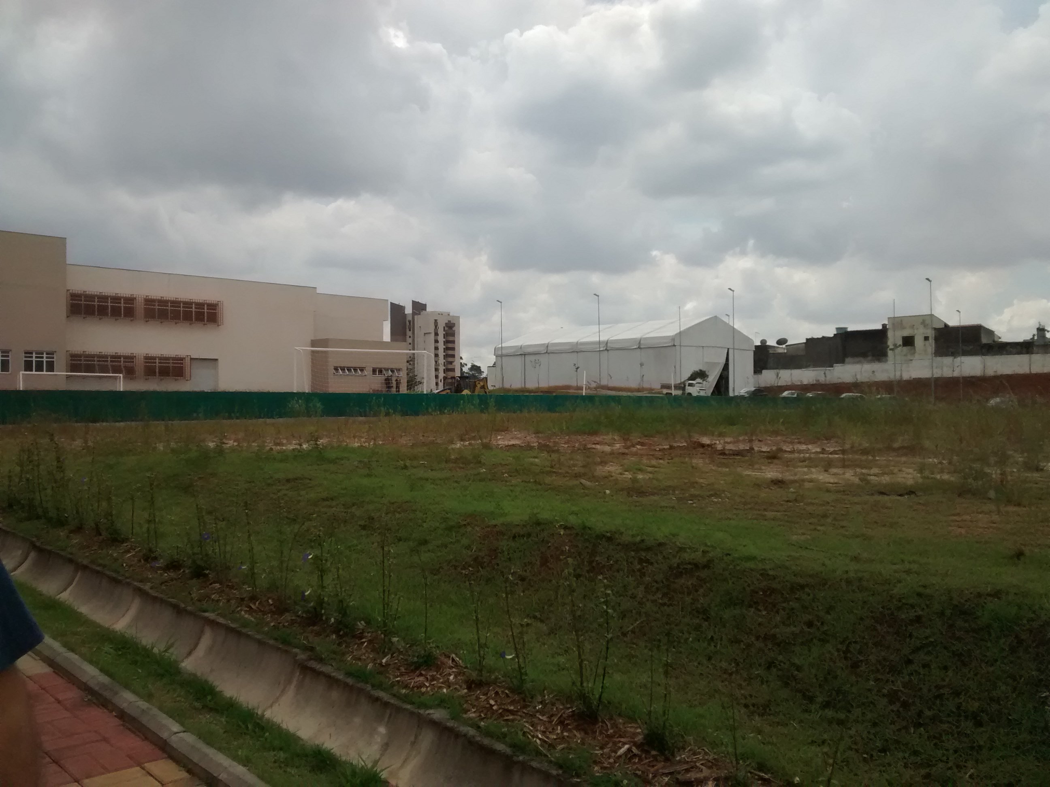
fotos/terreno/IMG_20170131_151235.jpg
