uncreatednet/wikilab-ufabc/elétrico/quantitativo.ods

Quantitativo projeto elétrico
Item | Quantidade | Unidade | Preço unitário material | Preço unitário mão de obra | Preço total material | Preço total mão de obra | Preço total item | Fonte do preço | Comprimento de cabos
 |  |  |  |  |  |  |  |  | Circuito | Comprimento | Cabos | Total | Eletroduto
 |  |  |  |  |  |  |  |  | Iluminação
Cabeamento alimentação 10mm | 430 | m | R$ 4.72 | R$ 3.45 | R$ 2,029.60 | R$ 1,483.50 | R$ 3,513.10 | PMSP 09-03-32
Eletroduto de PVC 50mm para cabo de alimentação | 14 | m | R$ 8.33 | R$ 19.40 | R$ 116.62 | R$ 271.60 | R$ 388.22 | PMSP 09-02-04 | L1E | 3.5 | 5 | 17.5
Quadro geral para 14 circuitos | 1 | un | R$ 291.85 | R$ 55.81 | R$ 291.85 | R$ 55.81 | R$ 347.66 | PMSP 09-05-06 | L1aE | 2.9 | 7 | 20.3
Disjuntor geral tripolar 40A | 1 | un | R$ 35.25 | R$ 37.63 | R$ 35.25 | R$ 37.63 | R$ 72.88 | PMSP 09-08-15 | L1abE | 2.9 | 9 | 26.1
Disjuntor tripolar 30A | 1 | un | R$ 35.25 | R$ 37.63 | R$ 35.25 | R$ 37.63 | R$ 72.88 | PMSP 09-08-15 | L1abc + L1ab | 4.5 | 13 | 58.5
DPS 20kA | 4 | un | R$ 135.49 | R$ 15.05 | R$ 541.96 | R$ 60.20 | R$ 602.16 | PMSP 09-17-01 | L1abE + L1ab | 2.9 | 12 | 34.8
Cabo de cobre nu 10mm para aterramento | 4 | m | R$ 3.60 | R$ 4.31 | R$ 14.40 | R$ 17.24 | R$ 31.64 | PMSP 09-06-91 | L1bE | 2.9 | 5 | 14.5
Aterramento com haste | 1 | un | R$ 137.23 | R$ 57.33 | R$ 137.23 | R$ 57.33 | R$ 194.56 | PMSP 09-06-99 | E | 4.9 | 3 | 14.7 | 1.5
Disjuntor unipolar 20A | 10 | un | R$ 12.31 | R$ 10.04 | R$ 123.10 | R$ 100.40 | R$ 223.50 | PMSP 09-08-10 | L1 | 1.8 | 3 | 5.4 | 1.8
Disjuntor bipolar 20A | 6 | un | R$ 33.47 | R$ 20.07 | R$ 200.82 | R$ 120.42 | R$ 321.24 | PMSP 09-08-12 | L1d | 1.8 | 4 | 7.2 | 1.8
Cabeamento 2.5mm iluminação | 214 | m | R$ 1.12 | R$ 2.16 | R$ 239.68 | R$ 462.24 | R$ 701.92 | PMSP 09-03-21 | L1cE | 3 | 5 | 15 | 3
Eletroduto aparente alimentação galvanizado 50mm | 1.5 | m | R$ 16.00 | R$ 32.33 | R$ 24.00 | R$ 48.50 | R$ 72.50 | PMSP 09-02-15 | Total |  |  | 214 | 8.1
Eletroduto aparente iluminação galvanizado 25mm | 8.1 | m | R$ 7.40 | R$ 21.55 | R$ 59.94 | R$ 174.56 | R$ 234.50 | PMSP 09-02-12
Luminária com duas lâmpadas fluorescentes 32W | 6 | un | R$ 94.58 | R$ 64.66 | R$ 567.48 | R$ 387.96 | R$ 955.44 | PMSP 09-09-75 | Tomadas
Luminária de sobrepor com lâmpada PL 18W | 1 | un | R$ 68.24 | R$ 47.41 | R$ 68.24 | R$ 47.41 | R$ 115.65 | PMSP 09-09-71 | T7 | 3.9 | 3 | 11.7 | 3.9
Arandela com lâmpada PL 18W | 1 | un | R$ 114.09 | R$ 34.49 | R$ 114.09 | R$ 34.49 | R$ 148.58 | PMSP 09-09-41 | T2T21 | 8.6 | 5 | 43 | 8.6
Calha metálica 38x38mm | 21 | m | R$ 18.20 | R$ 36.64 | R$ 382.20 | R$ 769.44 | R$ 1,151.64 | PMSP 09-13-07 | T3T4 | 4.8 | 5 | 24 | 4.8
Suportes para calha a cada 60cm | 35 | un | R$ 1.03 | R$ 8.62 | R$ 36.05 | R$ 301.70 | R$ 337.75 | PMSP 09-84-21 | T5 | 5.5 | 3 | 16.5 | 5.5
Emenda para calha metálica 38x38cm | 4 | un | R$ 0.94 | R$ 8.62 | R$ 3.76 | R$ 34.48 | R$ 38.24 | PMSP 09-84-25 | T3T4T21 | 6.2 | 7 | 43.4 | 6.2
Cabeamento 2.5mm tomadas | 228 | m | R$ 1.12 | R$ 2.16 | R$ 255.36 | R$ 492.48 | R$ 747.84 | PMSP 09-03-21 | T3T21 | 5 | 5 | 25 | 5
Eletroduto aparente tomadas galvanizado 25mm | 10.5 | m | R$ 7.40 | R$ 21.55 | R$ 77.70 | R$ 226.28 | R$ 303.98 | PMSP 09-02-12 | T6 | 1.9 | 3 | 5.7 | 1.9
Eletroduto PVC 25mm tomadas | 40.1 | m | R$ 2.96 | R$ 12.93 | R$ 118.70 | R$ 518.49 | R$ 637.19 | PMSP 09-02-02 | AC | 1.9 | 3 | 5.7 | 1.9
Tomada de piso | 20 | un | R$ 57.70 | R$ 107.76 | R$ 1,154.00 | R$ 2,155.20 | R$ 3,309.20 | PMSP 09-07-70 | T6 | 1.9 | 3 | 5.7 | 1.9
Tomada de parede | 18 | un | R$ 24.45 | R$ 86.21 | R$ 440.10 | R$ 1,551.78 | R$ 1,991.88 | PMSP 09-07-60 | T1T21 | 7.3 | 5 | 36.5 | 7.3
Ponto de força exterior | 1 | un | R$ 24.45 | R$ 86.21 | R$ 24.45 | R$ 86.21 | R$ 110.66 | PMSP 09-07-60 | T1 | 3.6 | 3 | 10.8 | 3.6
Interuptor bipolar simples em caixa de PVC 10x5cm | 4 | un | R$ 31.51 | R$ 133.63 | R$ 126.04 | R$ 534.52 | R$ 660.56 | PMSP 09-07-02 | Total |  |  | 228 | 50.6
Total |  |  |  |  | R$ 7,217.87 | R$ 10,067.49 | R$ 17,285.35
