uncreatednet/wikilab-ufabc/estudos/base.obj

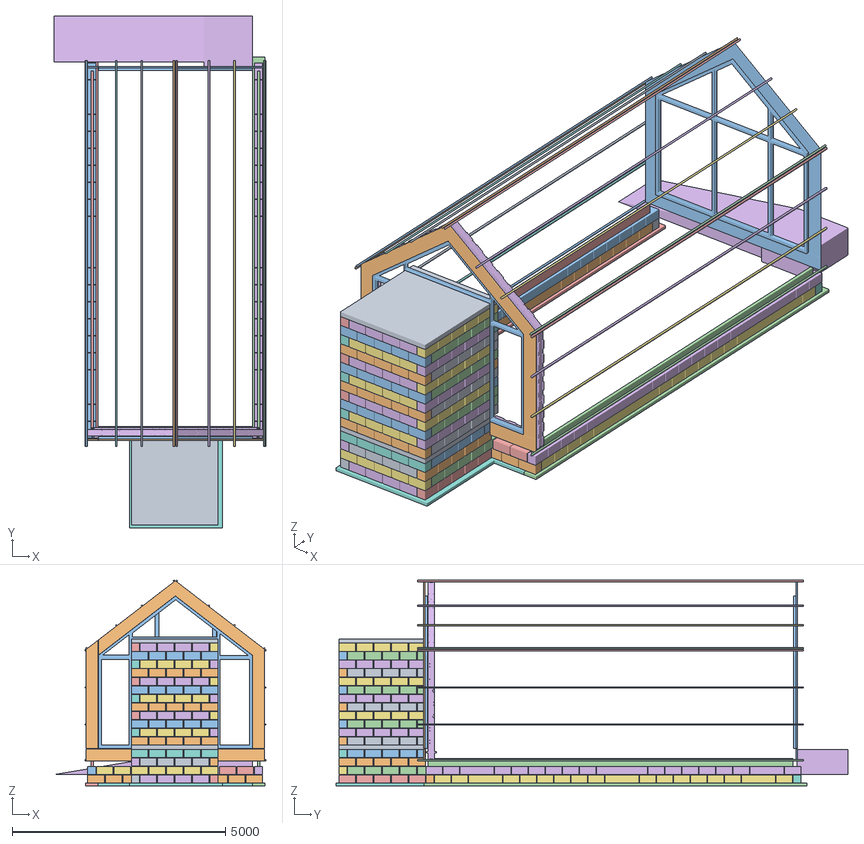
[picture p158: CAD file, 2017-02-05]
estudos/base.obj
4968.0 x 12004.3 x 4827.6
Porta.001_Plane.020
Tampa.001_Plane.019
Tampa_Plane.018
Meio-bloco_Plane.002
Meio-bloco.001_Plane.002
Bloco_Plane.001
Meio-bloco.002_Plane.002
Meio-bloco.003_Plane.002
Meio-bloco.004_Plane.002
Meio-bloco.005_Plane.002
Meio-bloco.006_Plane.002
Meio-bloco.007_Plane.002
Meio-bloco.008_Plane.002
Meio-bloco.009_Plane.002
Meio-bloco.010_Plane.002
Meio-bloco.011_Plane.002
Meio-bloco.012_Plane.002
Meio-bloco.013_Plane.002
Bloco.001_Plane.001
Bloco.002_Plane.001
Meio-bloco.014_Plane.002
Meio-bloco.015_Plane.002
Meio-bloco.016_Plane.002
Meio-bloco.017_Plane.002
Bloco.003_Plane.001
Bloco.004_Plane.001
Bloco.005_Plane.001
Bloco.006_Plane.001
Meio-bloco.018_Plane.002
Meio-bloco.019_Plane.002
Meio-bloco.020_Plane.002
Meio-bloco.021_Plane.002
Bloco.007_Plane.001
Bloco.008_Plane.001
Bloco.009_Plane.001
Bloco.010_Plane.001
Meio-bloco.022_Plane.002
Meio-bloco.023_Plane.002
Meio-bloco.024_Plane.002
Meio-bloco.025_Plane.002
Bloco.011_Plane.001
Bloco.012_Plane.001
Bloco.013_Plane.001
Bloco.014_Plane.001
Bloco.015_Plane.001
Bloco.016_Plane.001
Bloco.017_Plane.001
Bloco.018_Plane.001
Meio-bloco.026_Plane.002
Meio-bloco.027_Plane.002
Meio-bloco.028_Plane.002
Meio-bloco.029_Plane.002
Bloco.019_Plane.001
Bloco.020_Plane.001
Bloco.021_Plane.001
Bloco.022_Plane.001
Bloco.023_Plane.001
Bloco.024_Plane.001
Bloco.025_Plane.001
Bloco.026_Plane.001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
