uncreatednet/wikilab-ufabc/folhas de corte/plotsheet 1 - elemento final (1x).dxf

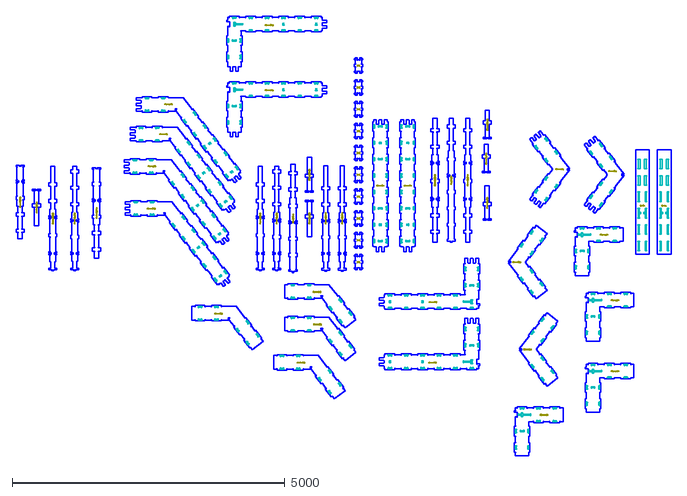
[picture p159: CAD file, 2017-06-28]
folhas de corte/plotsheet 1 - elemento final (1x).dxf
12000.0 x 8049.0
