uncreatednet/wikilab-ufabc/estudos/wren.obj

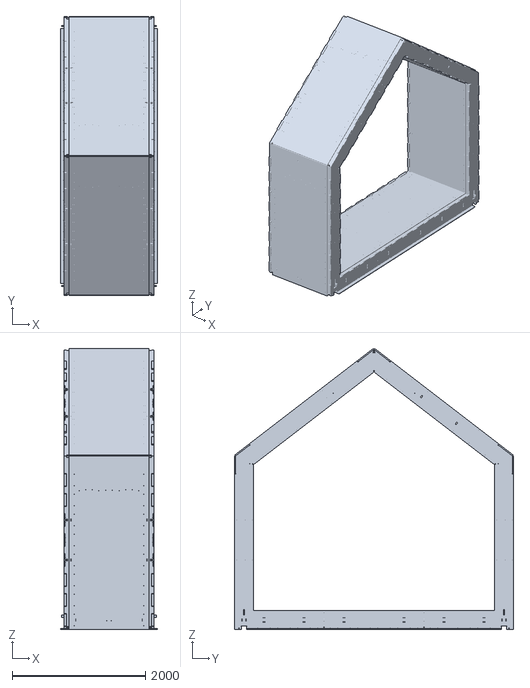
[picture p160: CAD file, 2017-01-31]
estudos/wren.obj
1450.0 x 4186.0 x 4215.0
