uncreatednet/wikilab-ufabc/folhas de corte/teste cut sheet.dxf

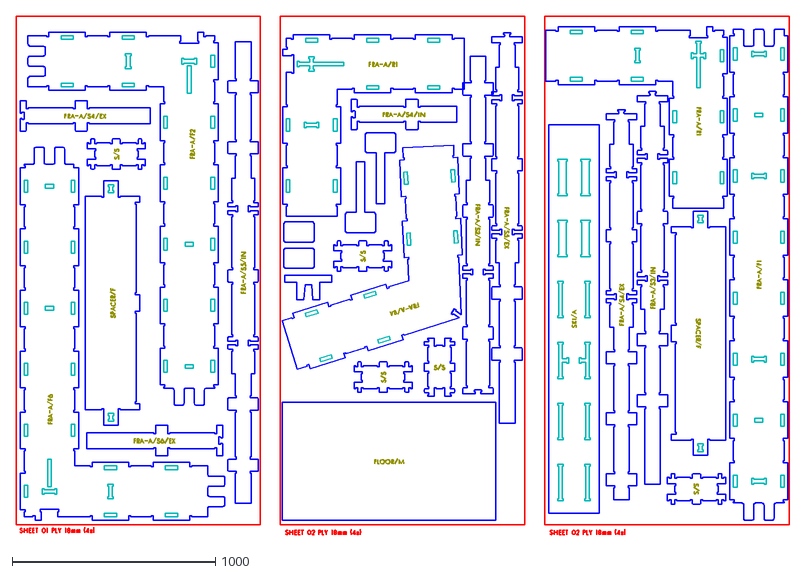
[picture p161: CAD file, 2017-02-08]
folhas de corte/teste cut sheet.dxf
3800.0 x 2548.9
