uncreatednet/wikilab-ufabc/fotos/construção da primeira costela/IMG_20170530_112556.jpg

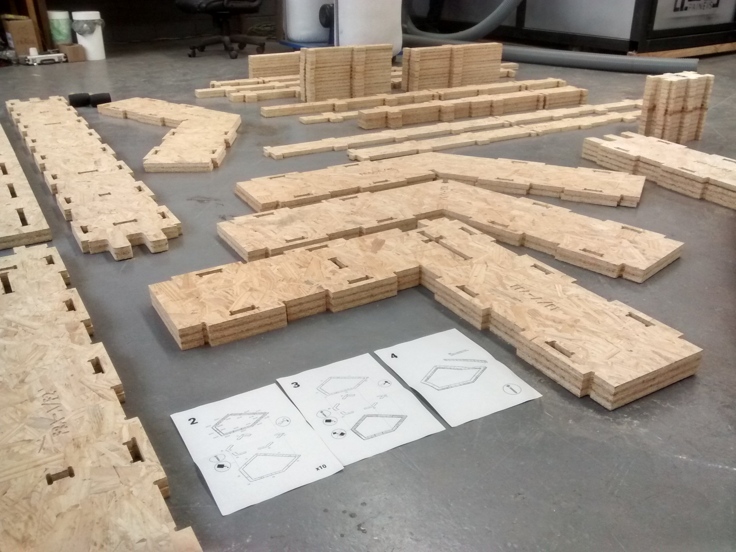
fotos/construção da primeira costela/IMG_20170530_112556.jpg
