uncreatednet/wikilab-ufabc/fotos/construção da primeira costela/IMG_20170530_114622.jpg

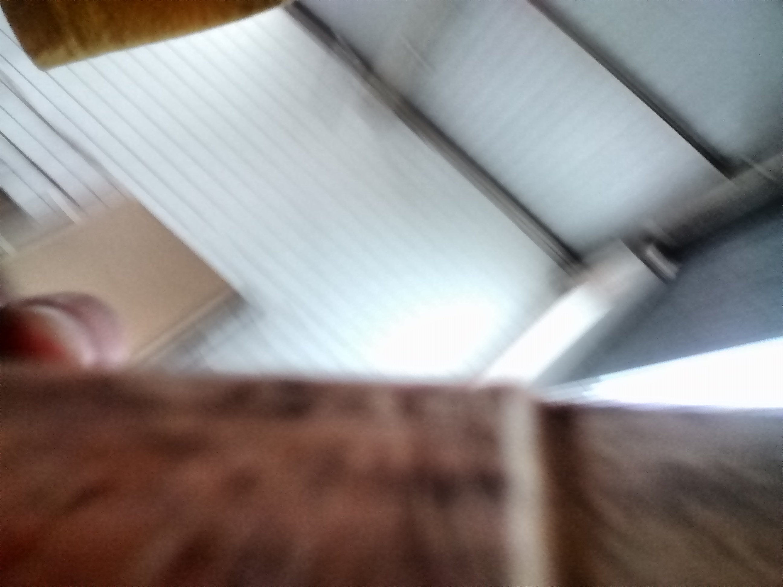
fotos/construção da primeira costela/IMG_20170530_114622.jpg
