uncreatednet/wikilab-ufabc/fotos/construção da primeira costela/IMG_20170530_114640.jpg

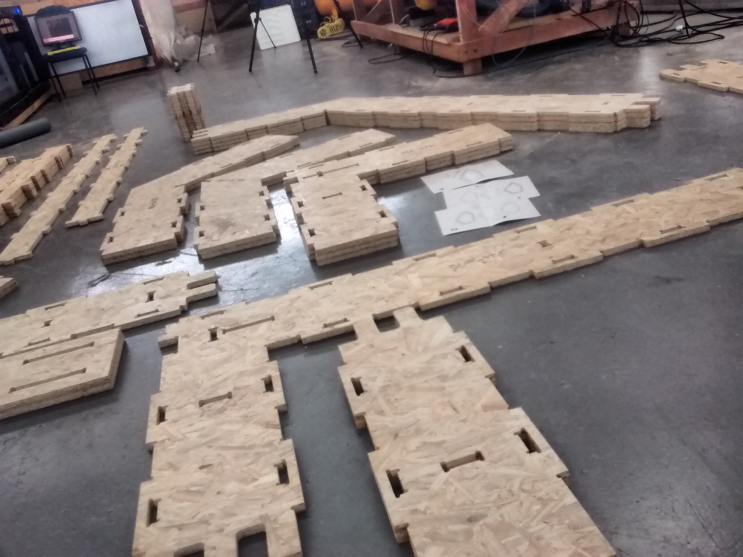
fotos/construção da primeira costela/IMG_20170530_114640.jpg
