uncreatednet/wikilab-ufabc/fotos/construção da primeira costela/IMG_20170530_122332.jpg

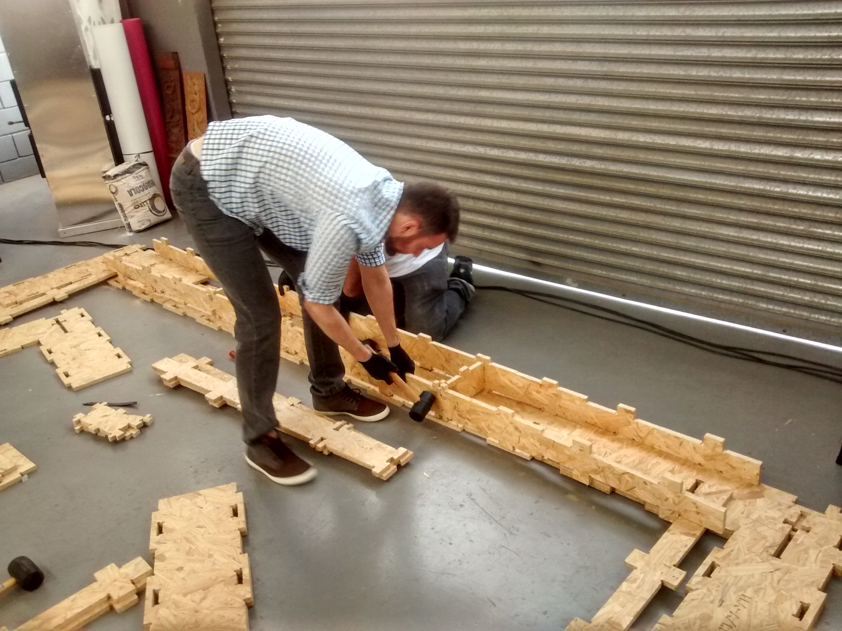
fotos/construção da primeira costela/IMG_20170530_122332.jpg
