uncreatednet/wikilab-ufabc/fotos/construção da primeira costela/IMG_20170530_124426.jpg

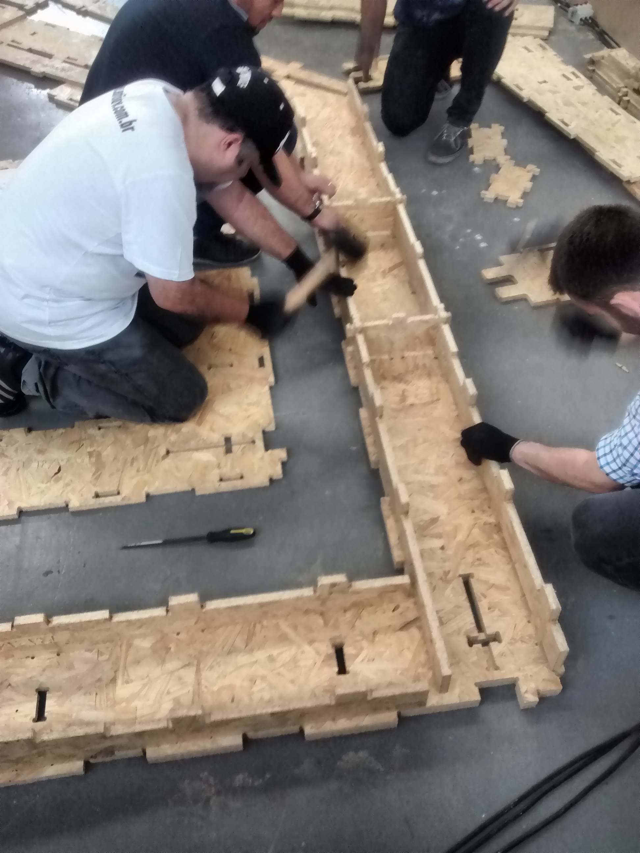
fotos/construção da primeira costela/IMG_20170530_124426.jpg
