uncreatednet/wikilab-ufabc/fotos/construção da primeira costela/IMG_20170530_124437.jpg

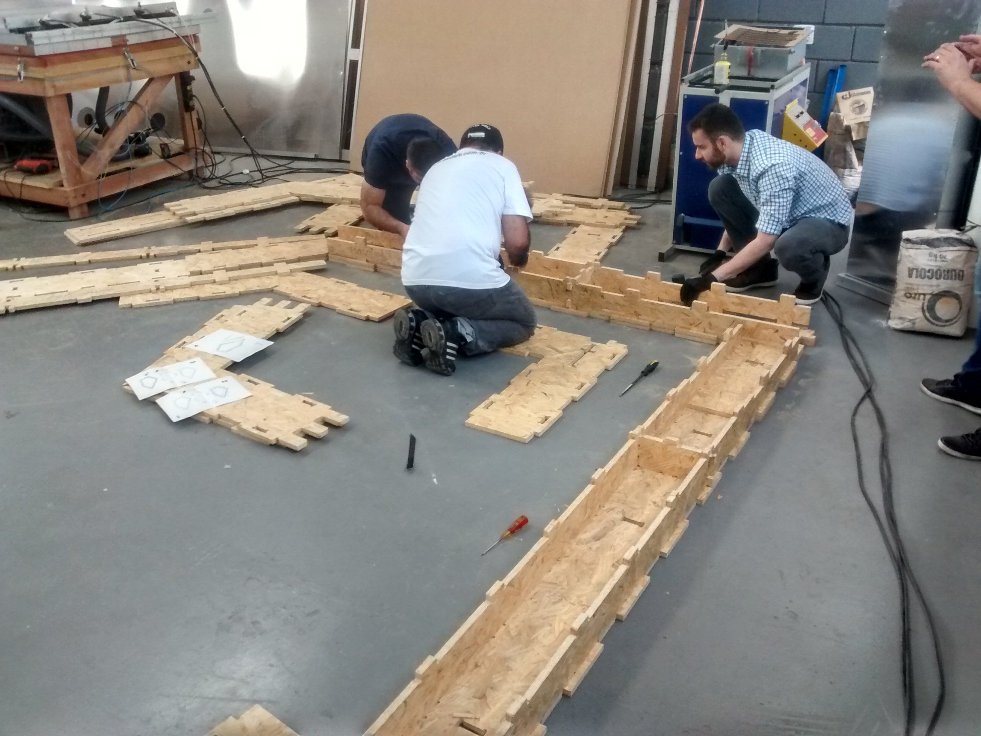
fotos/construção da primeira costela/IMG_20170530_124437.jpg
