uncreatednet/wikilab-ufabc/fotos/construção da primeira costela/IMG_20170530_125601.jpg

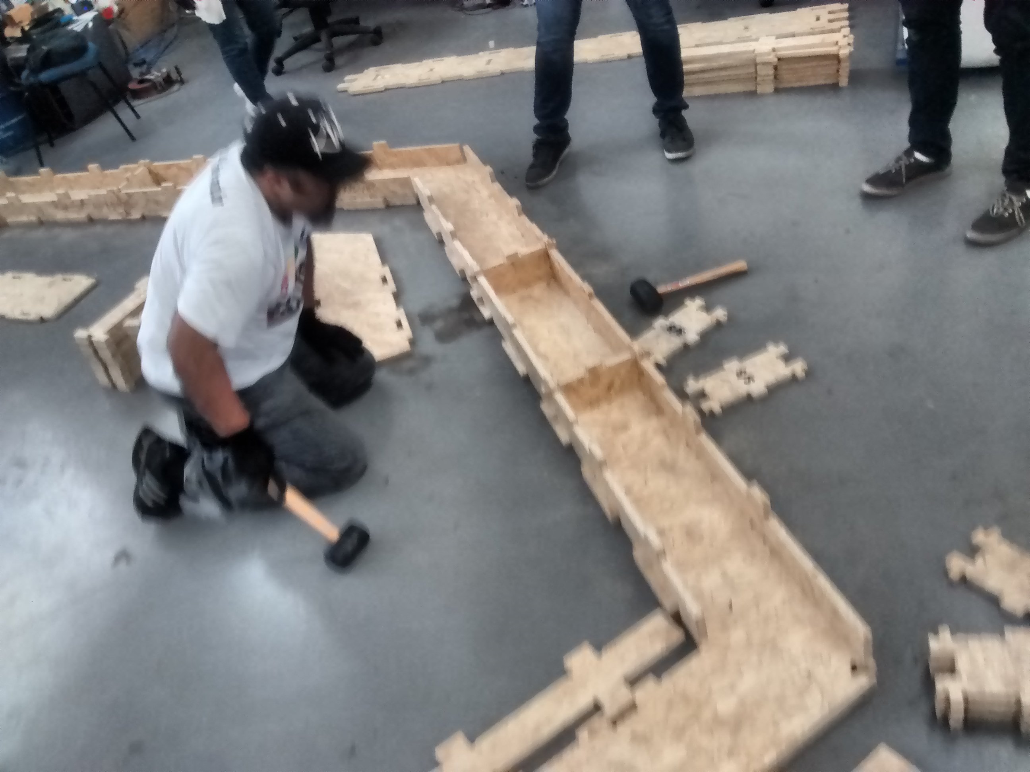
fotos/construção da primeira costela/IMG_20170530_125601.jpg
