uncreatednet/wikilab-ufabc/fotos/construção da primeira costela/IMG_20170530_134530.jpg

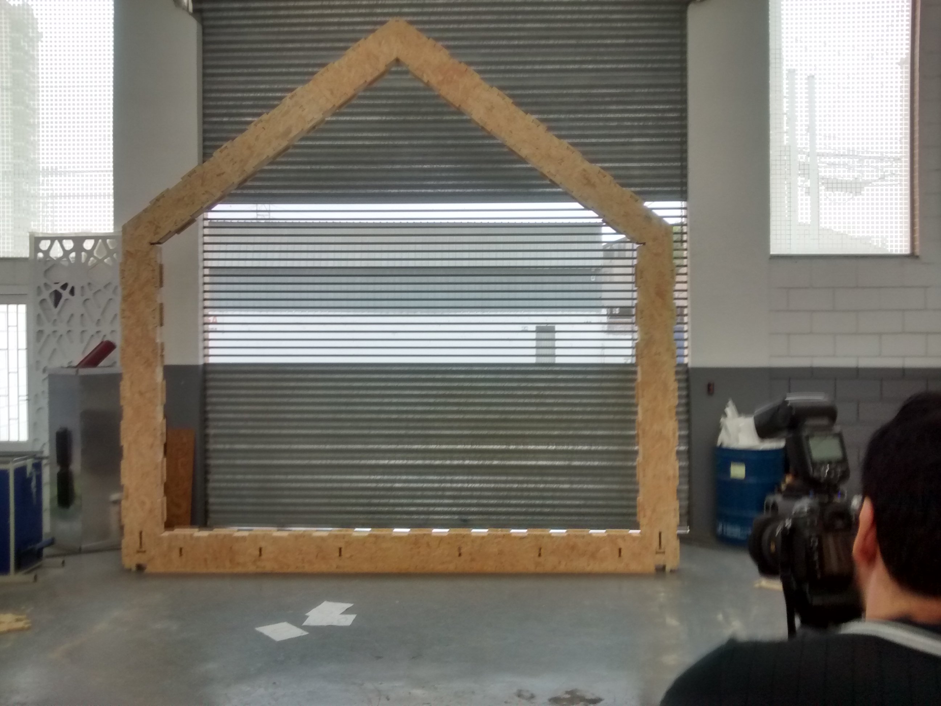
fotos/construção da primeira costela/IMG_20170530_134530.jpg
