uncreatednet/wikilab-ufabc/fotos/construção da primeira costela/IMG_20170530_135012.jpg

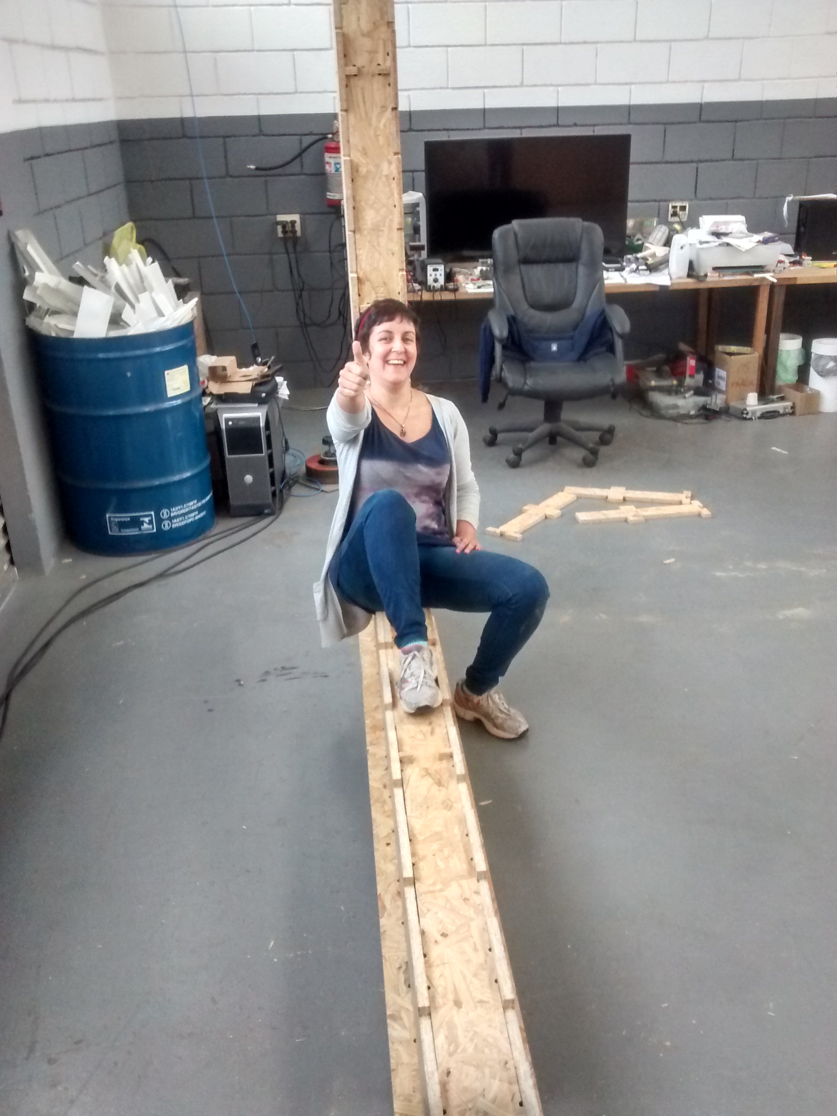
fotos/construção da primeira costela/IMG_20170530_135012.jpg
