uncreatednet/wikilab-ufabc/fotos/construção da primeira costela/IMG_20170530_160828.jpg

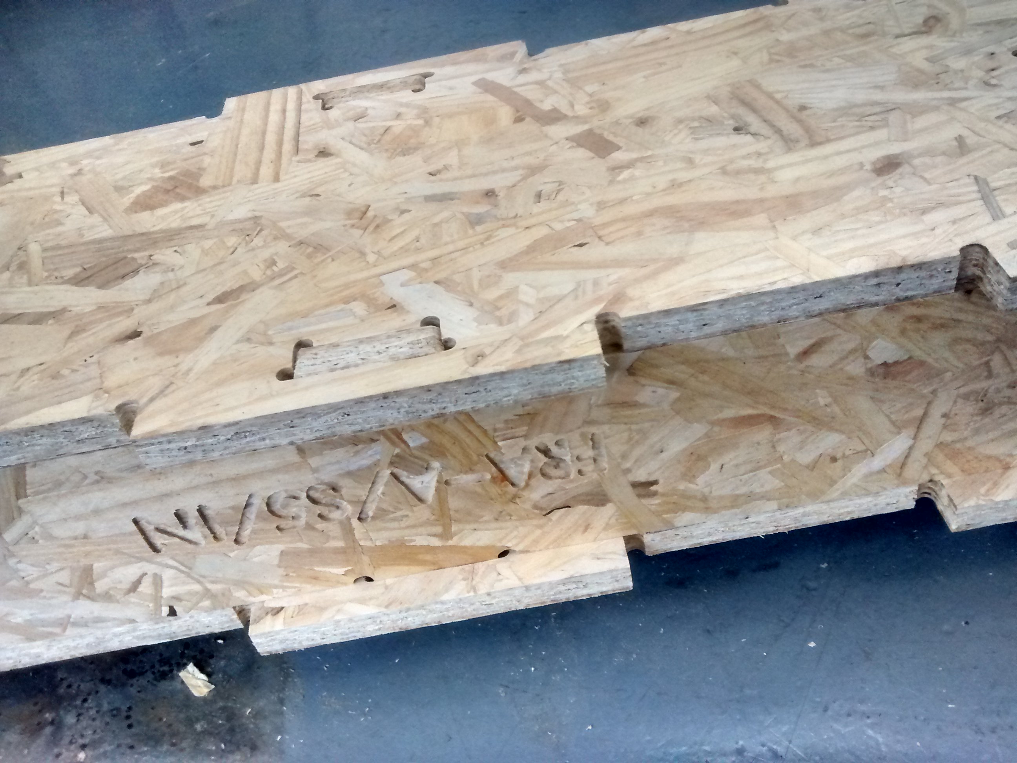
fotos/construção da primeira costela/IMG_20170530_160828.jpg
