uncreatednet/wikilab-ufabc/fotos/construção da primeira costela/IMG_20170530_161152.jpg

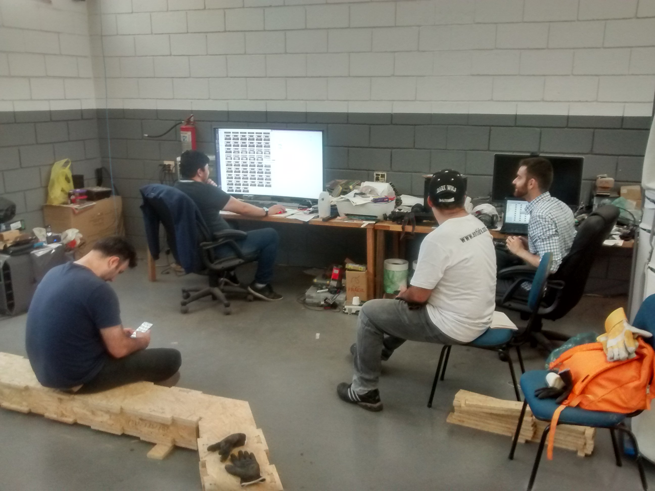
fotos/construção da primeira costela/IMG_20170530_161152.jpg
