uncreatednet/wikilab-ufabc/fotos/construção da primeira costela/IMG_20170530_161201.jpg

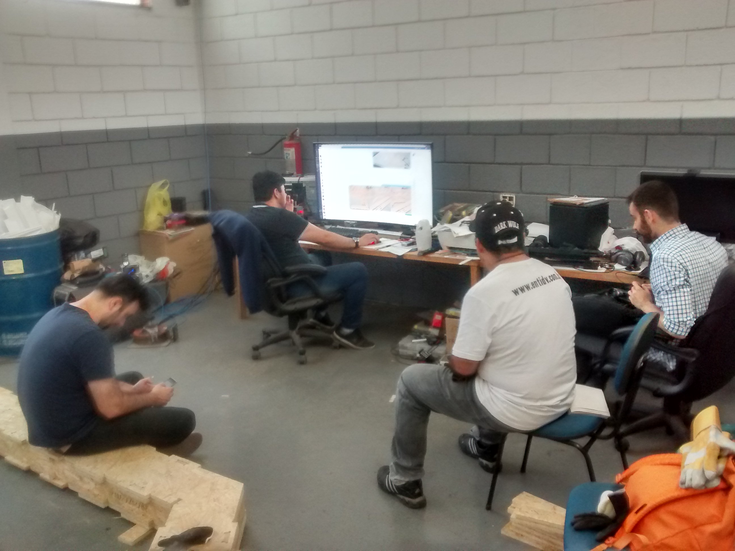
fotos/construção da primeira costela/IMG_20170530_161201.jpg
