uncreatednet/wikilab-ufabc/fotos/construção da primeira costela/IMG_20170530_161209.jpg

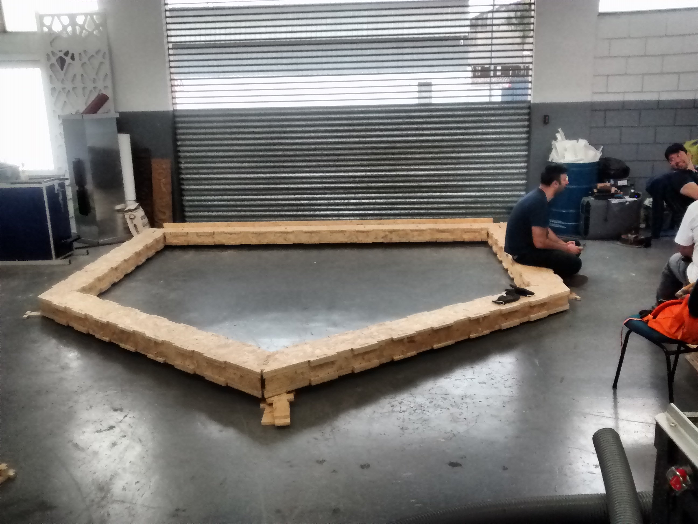
fotos/construção da primeira costela/IMG_20170530_161209.jpg
