uncreatednet/wikilab-ufabc/fotos/construção da primeira costela/IMG_20170530_161214.jpg

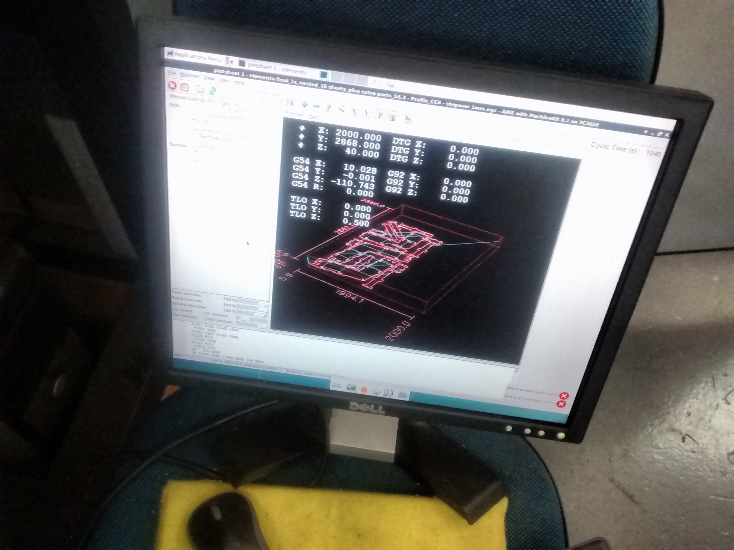
fotos/construção da primeira costela/IMG_20170530_161214.jpg
