uncreatednet/wikilab-ufabc/manual de construção/imagens/10.jpg

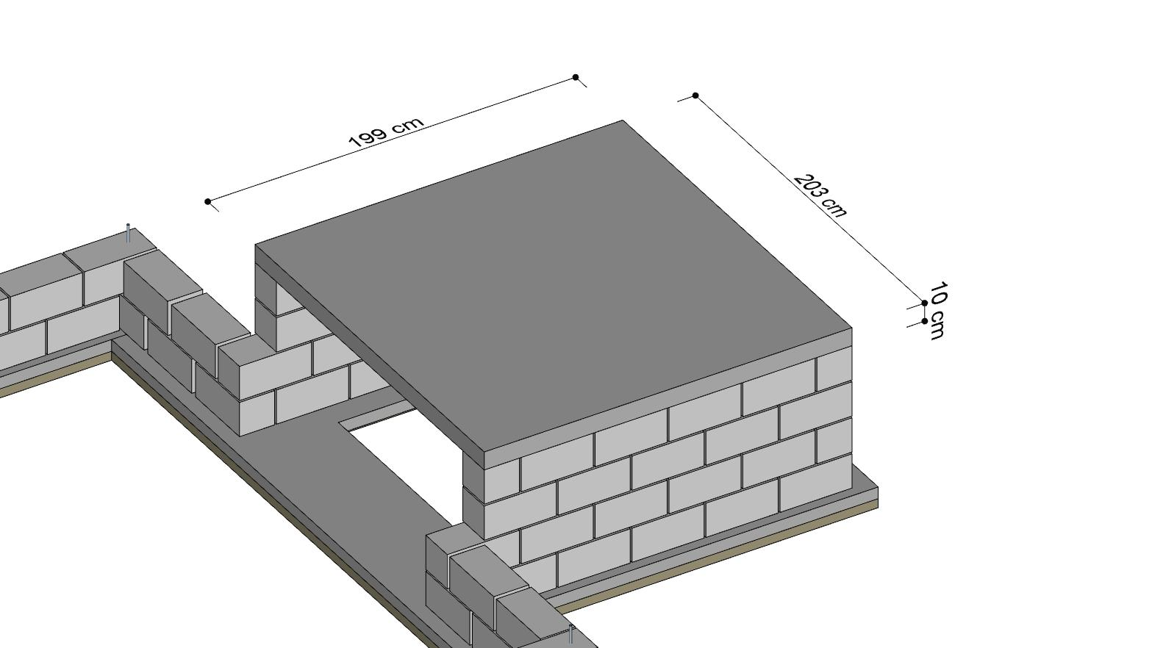
manual de construção/imagens/10.jpg
