uncreatednet/wikilab-ufabc/manual de construção/imagens/84.jpg

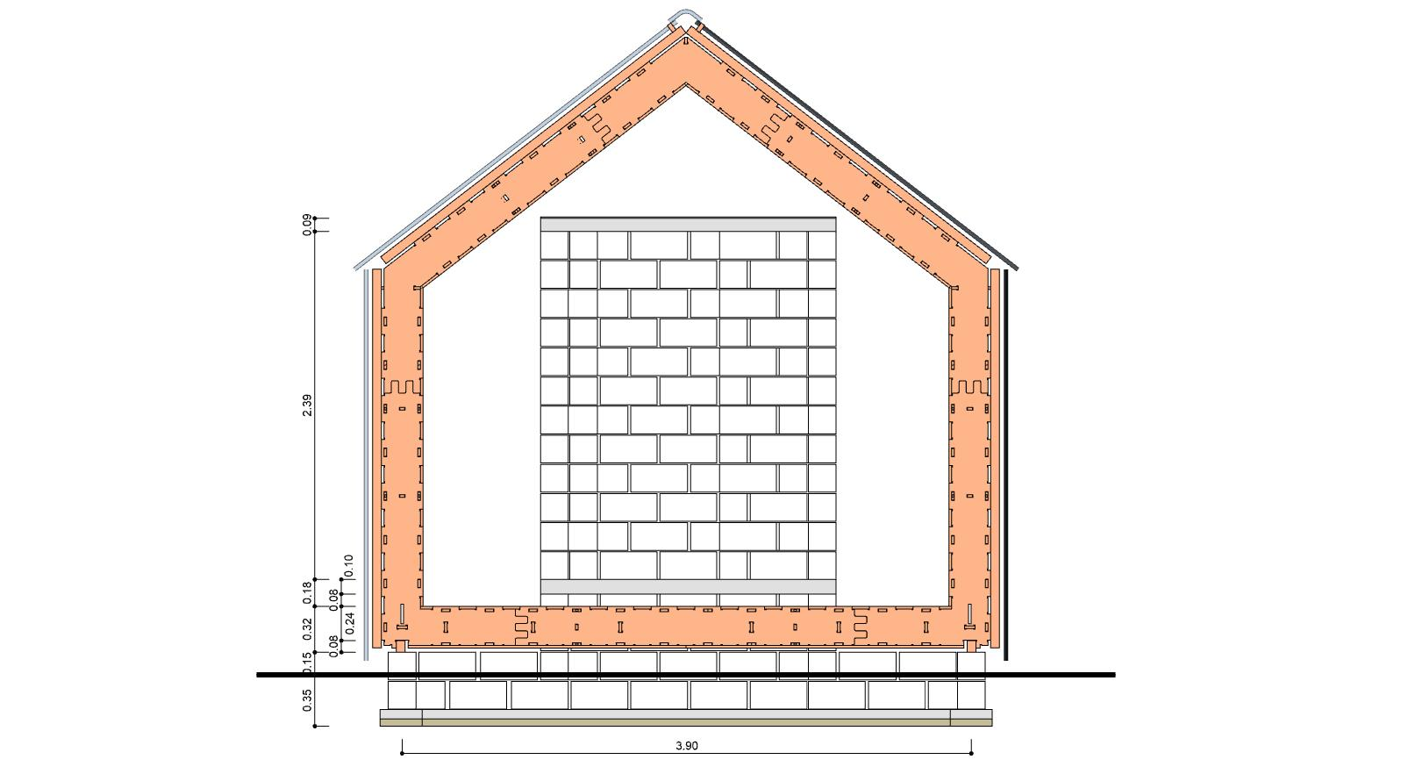
manual de construção/imagens/84.jpg
