uncreatednet/wikilab-ufabc/manual de construção/imagens/86.jpg

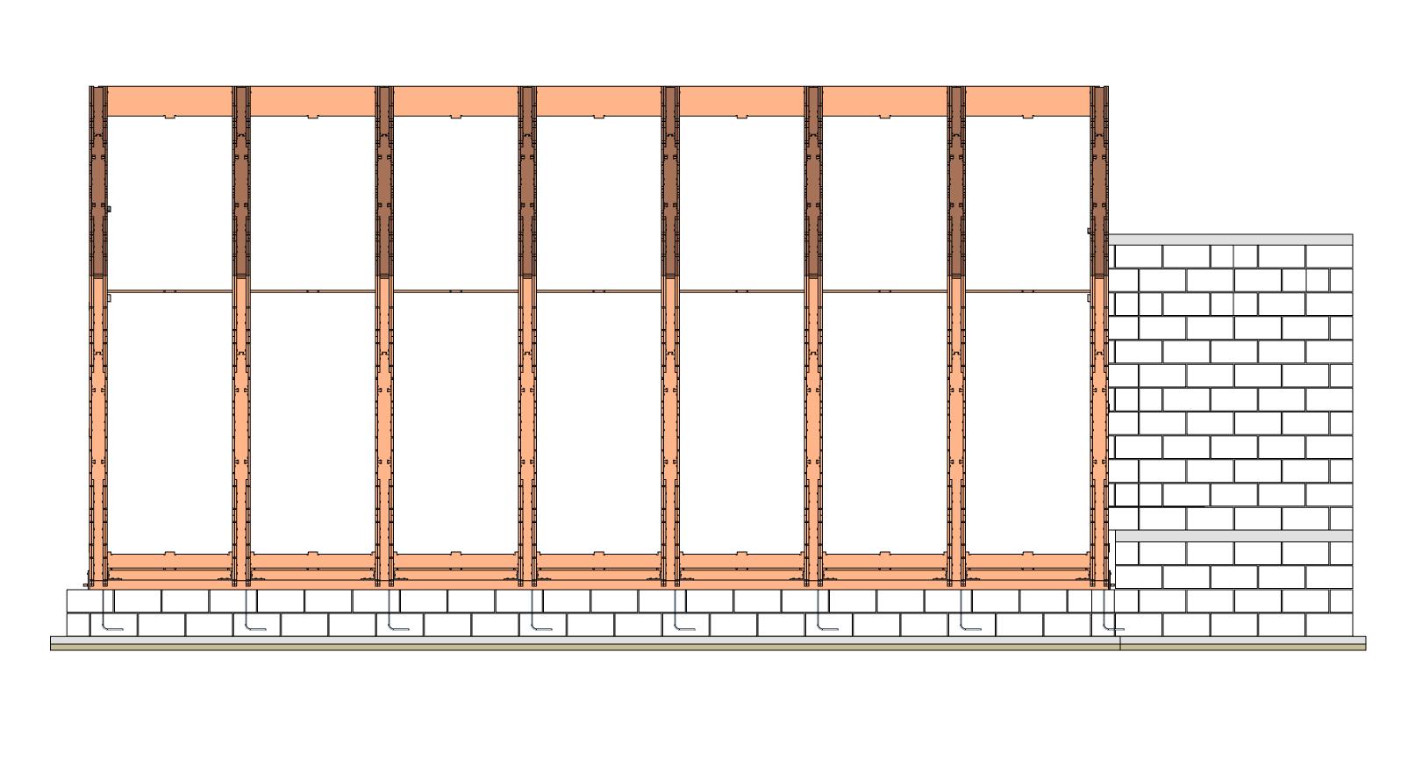
manual de construção/imagens/86.jpg
