uncreatednet/wikilab-ufabc/fotos/teste de encaixe/18596393_10158687201485635_686928746_o.jpg

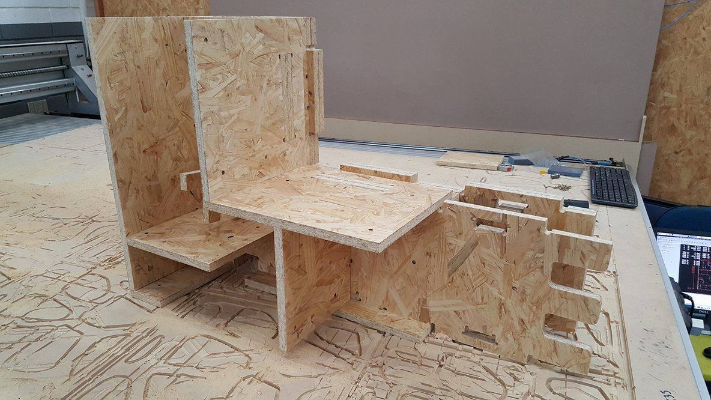
fotos/teste de encaixe/18596393_10158687201485635_686928746_o.jpg
