uncreatednet/wikilab-ufabc/fotos/teste de encaixe/_RSN6866.JPG

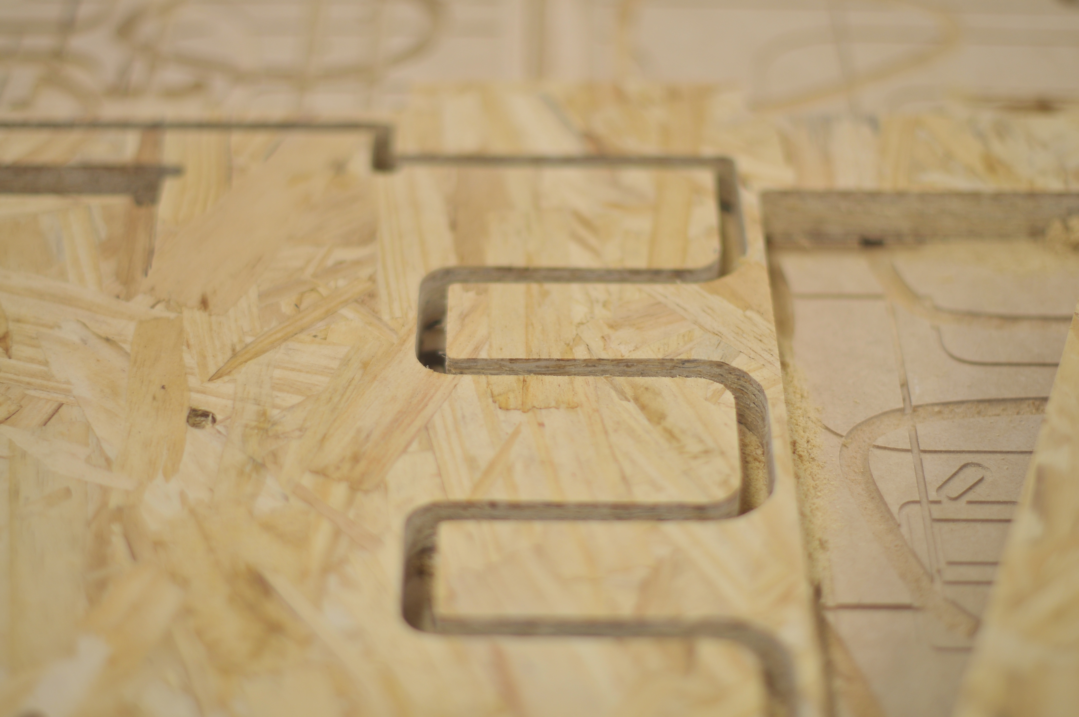
fotos/teste de encaixe/_RSN6866.JPG
