uncreatednet/wikilab-ufabc/fotos/teste de encaixe/IMG_20170519_121142.jpg

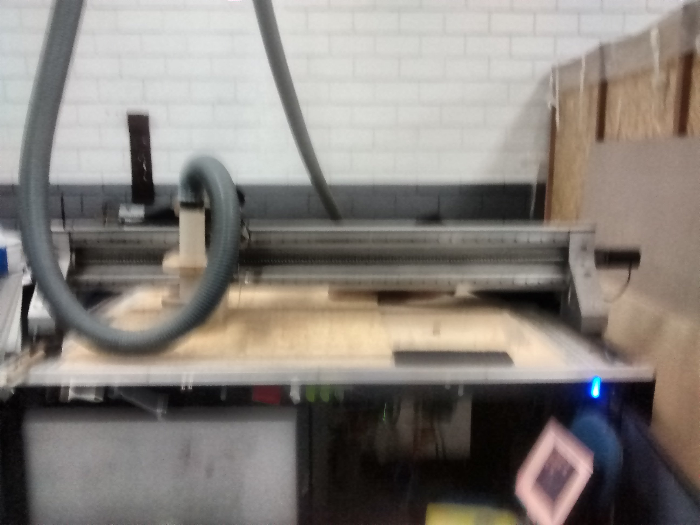
fotos/teste de encaixe/IMG_20170519_121142.jpg
