uncreatednet/wikilab-ufabc/fotos/teste de encaixe/IMG_20170519_121150.jpg

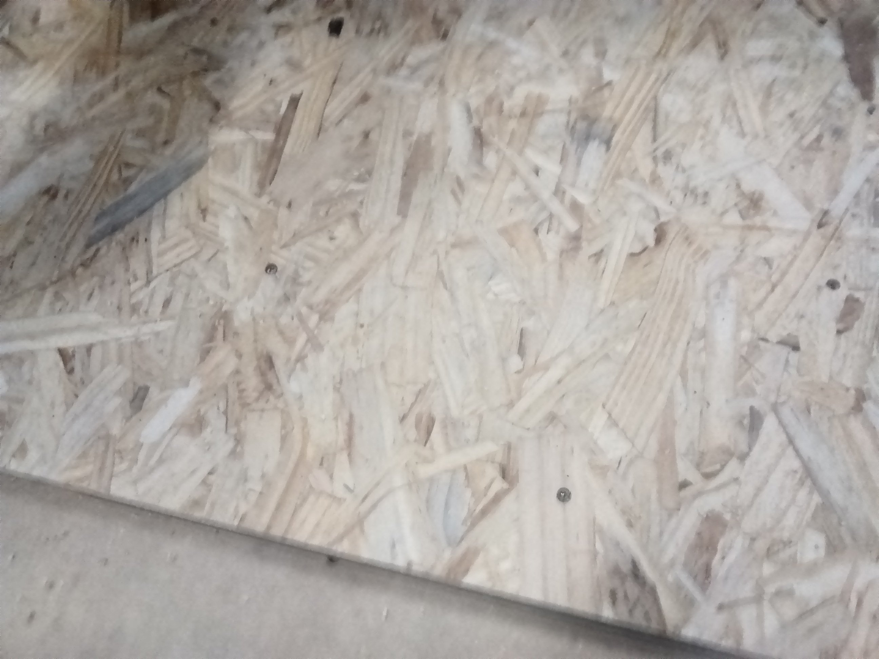
fotos/teste de encaixe/IMG_20170519_121150.jpg
