uncreatednet/wikilab-ufabc/fotos/teste de encaixe/IMG_20170519_121210.jpg

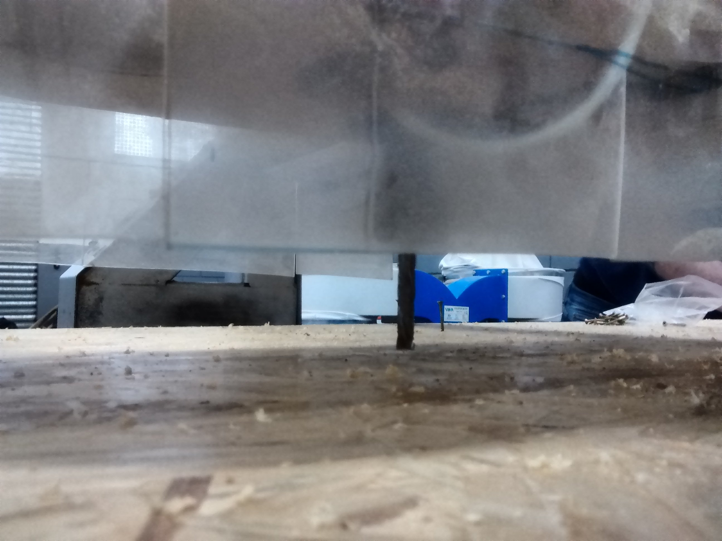
fotos/teste de encaixe/IMG_20170519_121210.jpg
