uncreatednet/wikilab-ufabc/fotos/teste de encaixe/IMG_20170519_122008.jpg

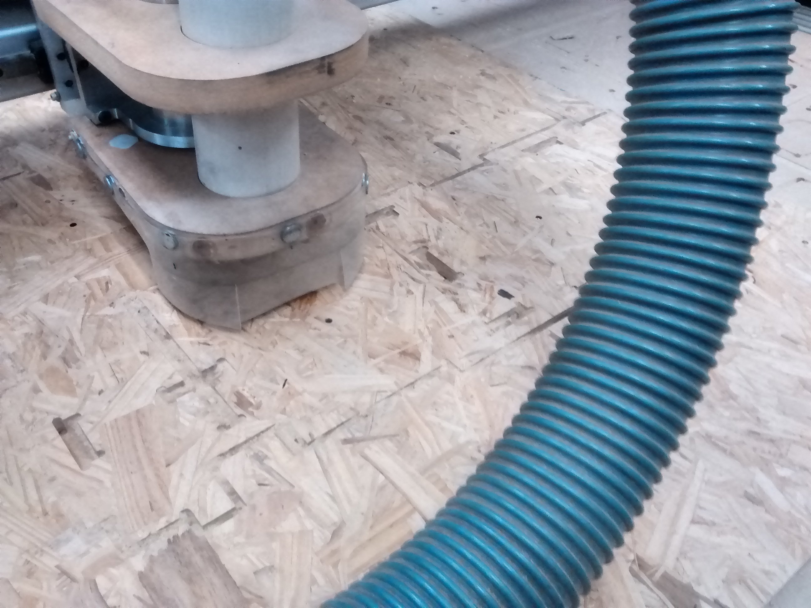
fotos/teste de encaixe/IMG_20170519_122008.jpg
