uncreatednet/wikilab-ufabc/fotos/teste de encaixe/IMG_20170519_122015.jpg

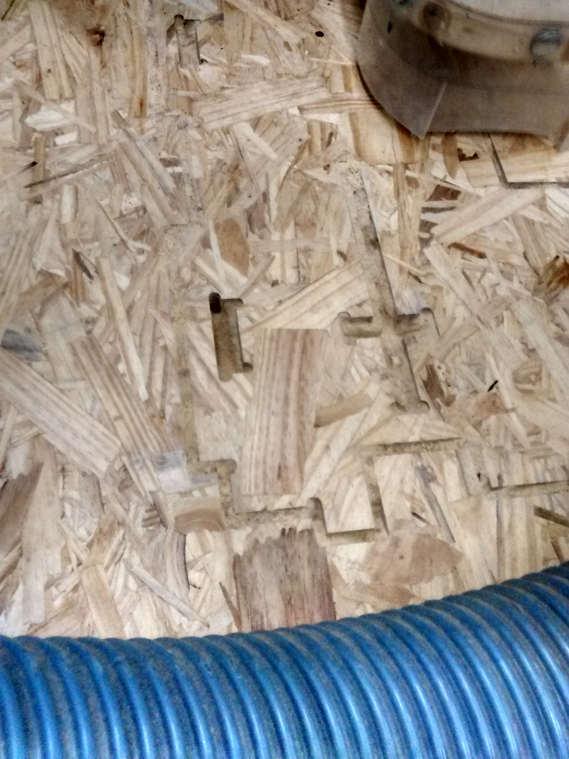
fotos/teste de encaixe/IMG_20170519_122015.jpg
