uncreatednet/wikilab-ufabc/fotos/teste de encaixe/IMG_20170519_122304.jpg

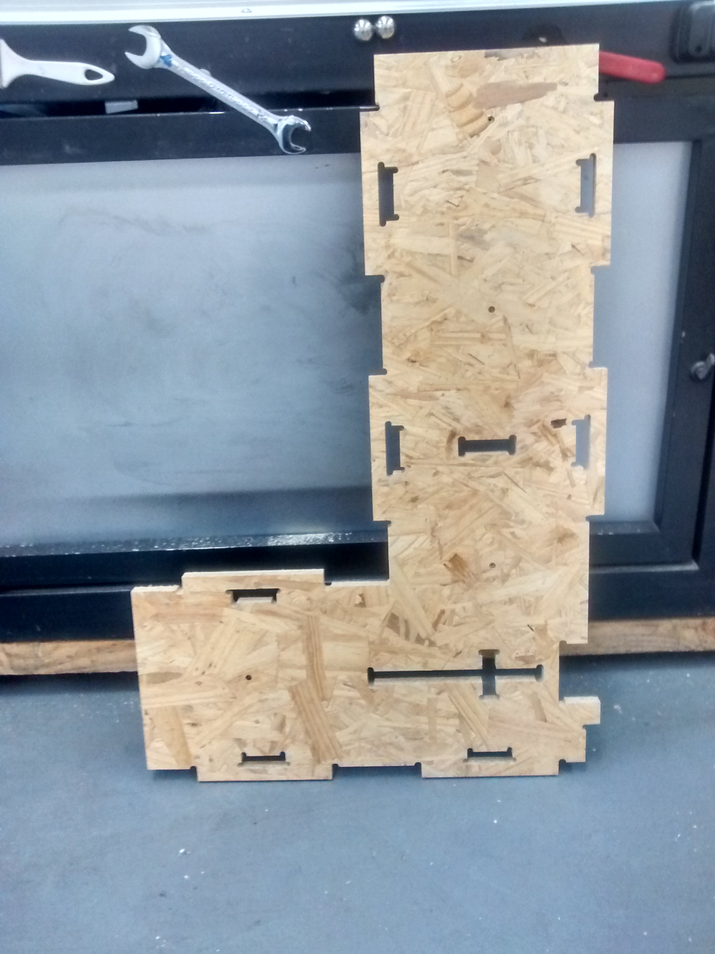
fotos/teste de encaixe/IMG_20170519_122304.jpg
