uncreatednet/wikilab-ufabc/fotos/teste de encaixe/IMG_20170519_122311.jpg

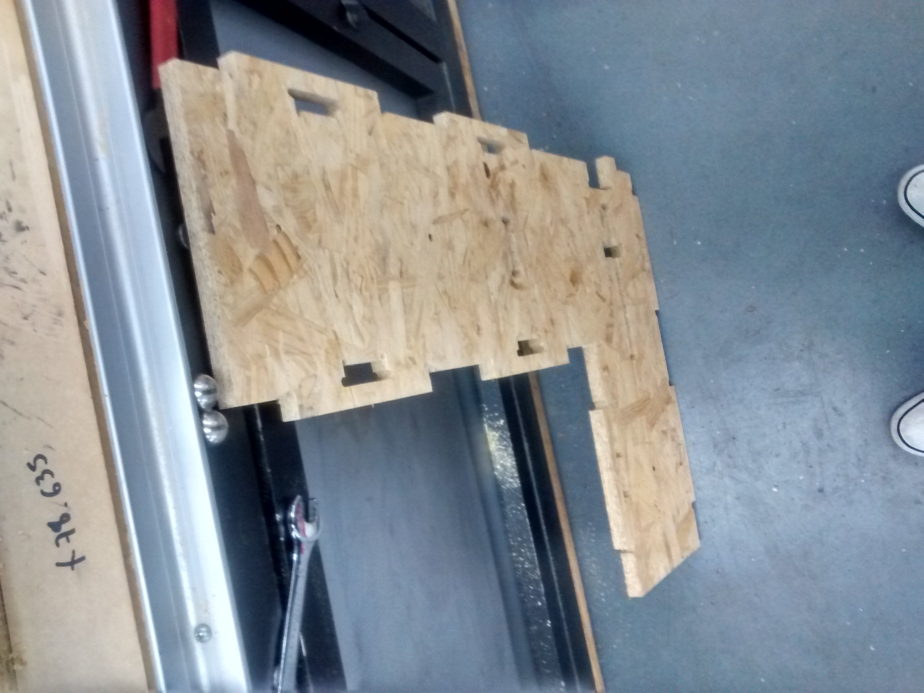
fotos/teste de encaixe/IMG_20170519_122311.jpg
