uncreatednet/wikilab-ufabc/fotos/teste de encaixe/IMG_20170519_131202.jpg

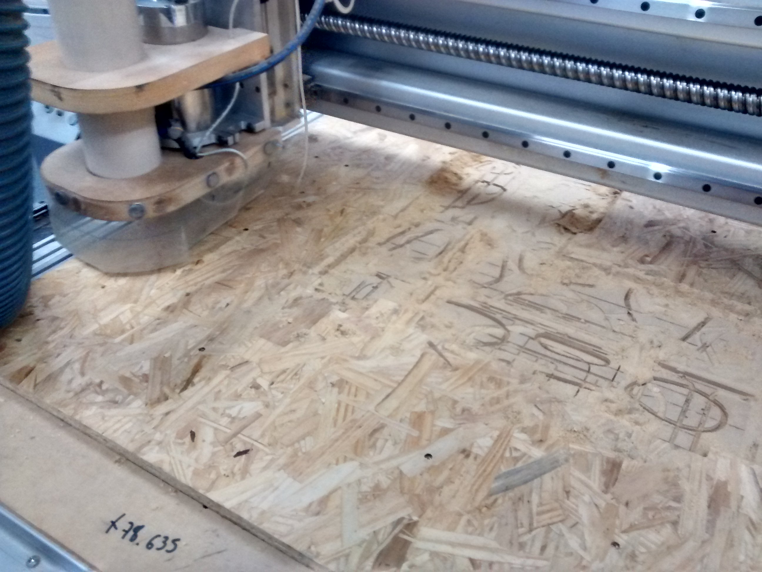
fotos/teste de encaixe/IMG_20170519_131202.jpg
