uncreatednet/wikilab-ufabc/fotos/teste de encaixe/IMG_20170519_141752.jpg

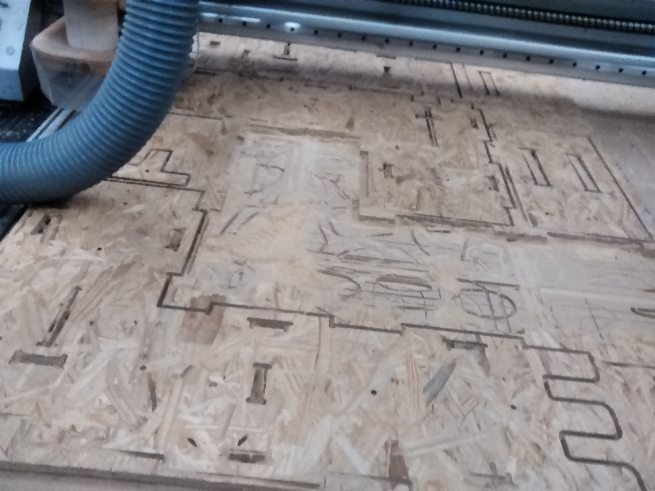
fotos/teste de encaixe/IMG_20170519_141752.jpg
