uncreatednet/wikilab-ufabc/fotos/teste de encaixe/IMG_20170519_141809.jpg

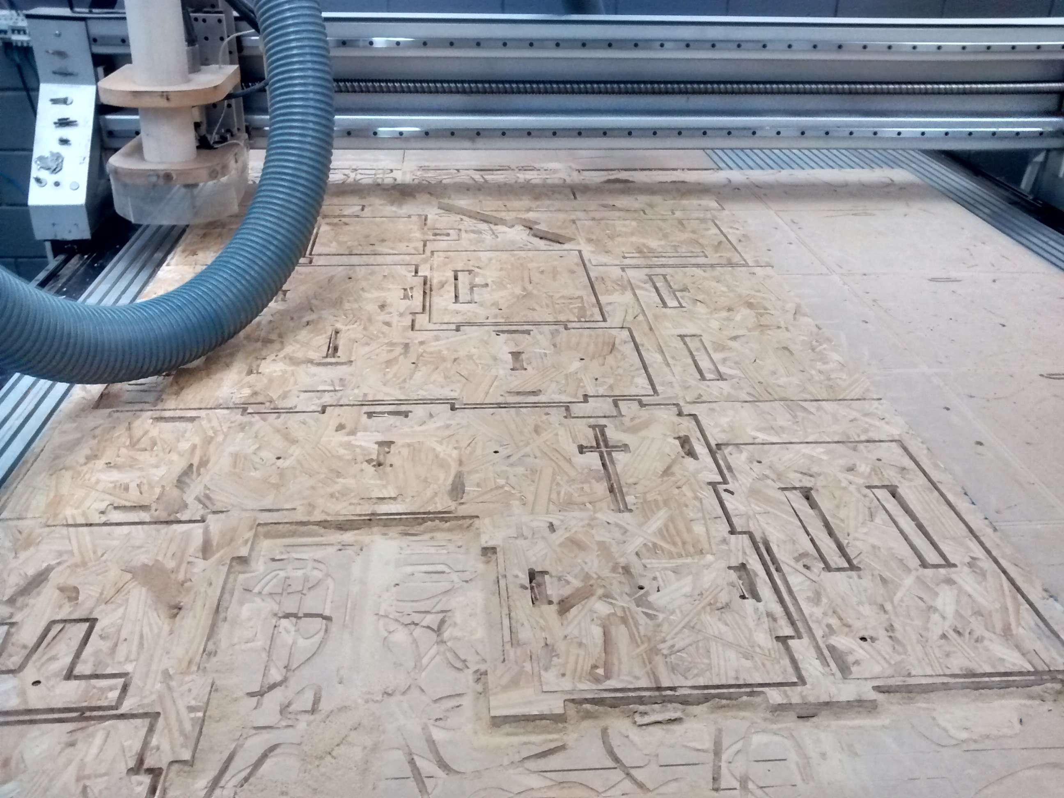
fotos/teste de encaixe/IMG_20170519_141809.jpg
