uncreatednet/wikilab-ufabc/fotos/teste de encaixe/IMG_20170519_142042.jpg

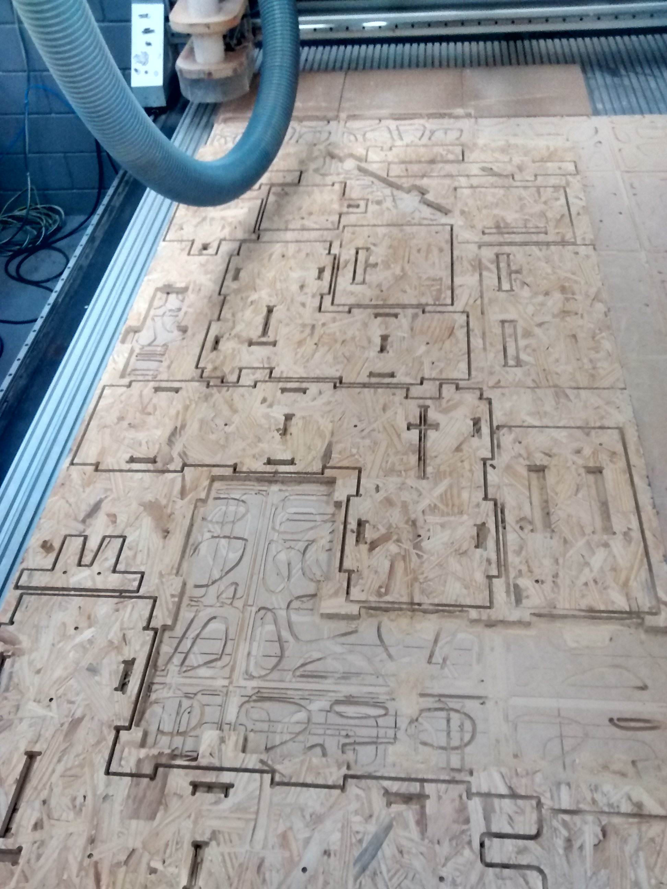
fotos/teste de encaixe/IMG_20170519_142042.jpg
