uncreatednet/wikilab-ufabc/fotos/teste de encaixe/IMG_20170519_142048.jpg

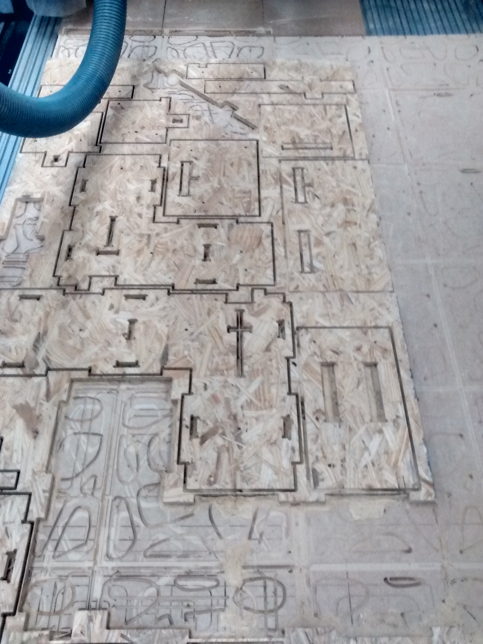
fotos/teste de encaixe/IMG_20170519_142048.jpg
