uncreatednet/wikilab-ufabc/fotos/teste de encaixe/IMG_20170519_142111.jpg

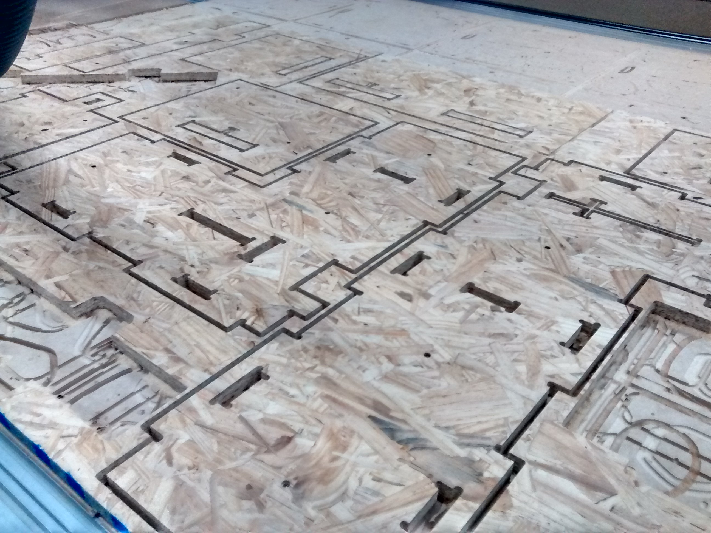
fotos/teste de encaixe/IMG_20170519_142111.jpg
