uncreatednet/wikilab-ufabc/fotos/teste de encaixe/IMG_20170519_142202.jpg

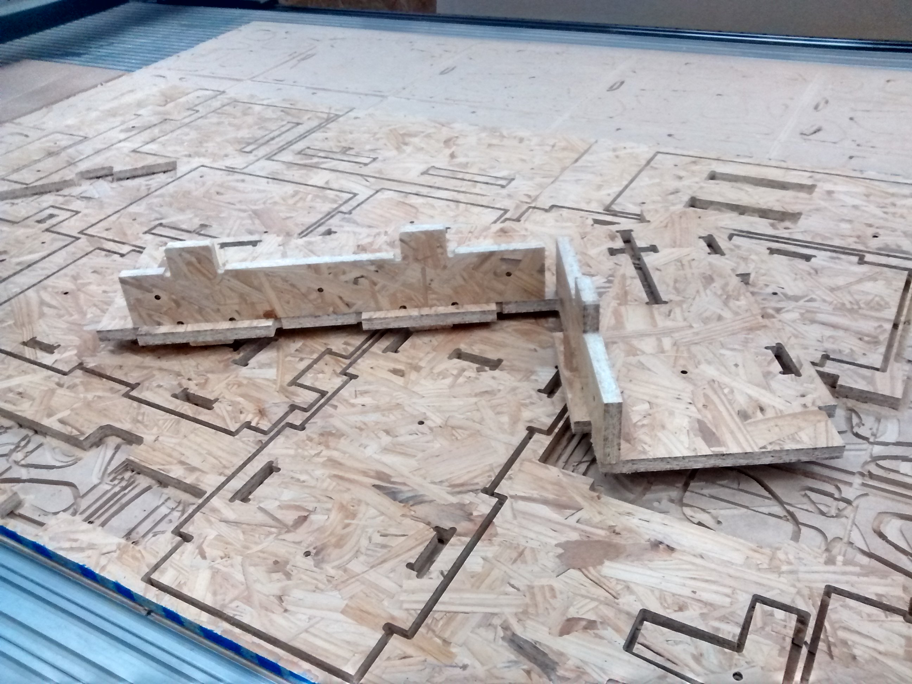
fotos/teste de encaixe/IMG_20170519_142202.jpg
