uncreatednet/wikilab-ufabc/fotos/teste de encaixe/IMG_20170519_143202.jpg

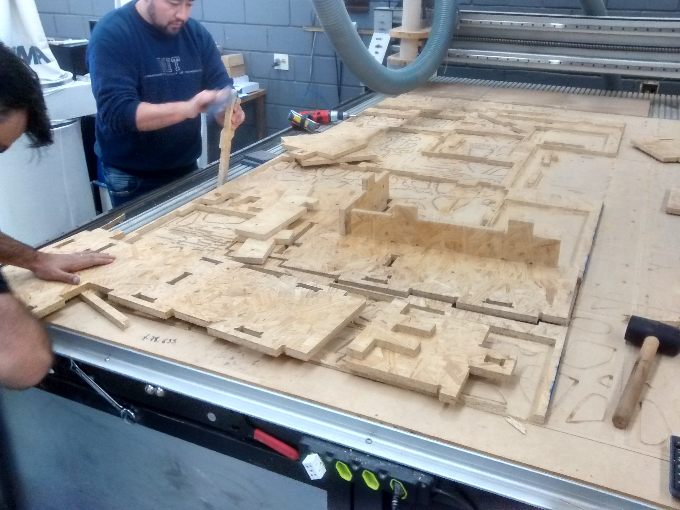
fotos/teste de encaixe/IMG_20170519_143202.jpg
