uncreatednet/wikilab-ufabc/fotos/teste de encaixe/IMG_20170519_143213.jpg

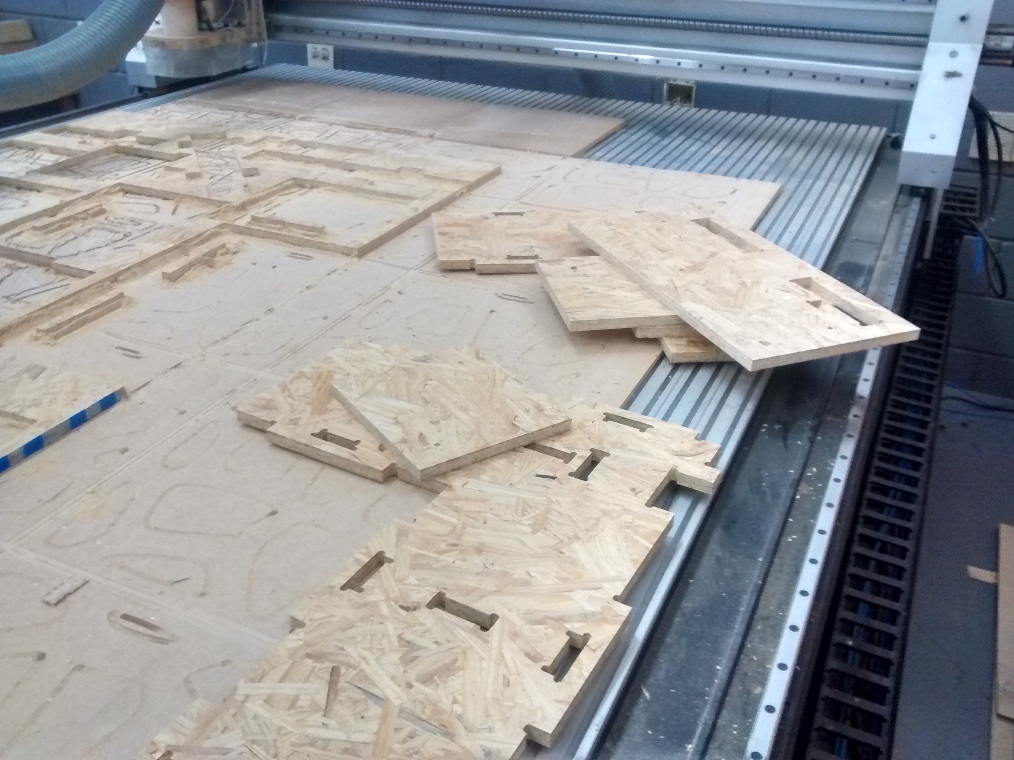
fotos/teste de encaixe/IMG_20170519_143213.jpg
