uncreatednet/wikilab-ufabc/fotos/teste de encaixe/IMG_20170519_145425.jpg

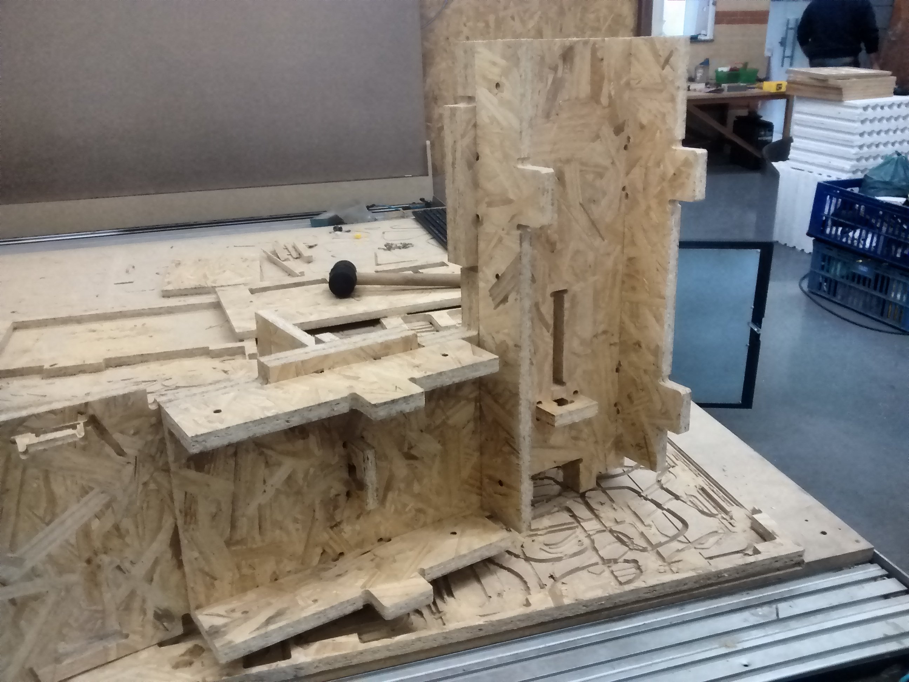
fotos/teste de encaixe/IMG_20170519_145425.jpg
