uncreatednet/wikilab-ufabc/fotos/teste de encaixe/IMG_20170519_145433.jpg

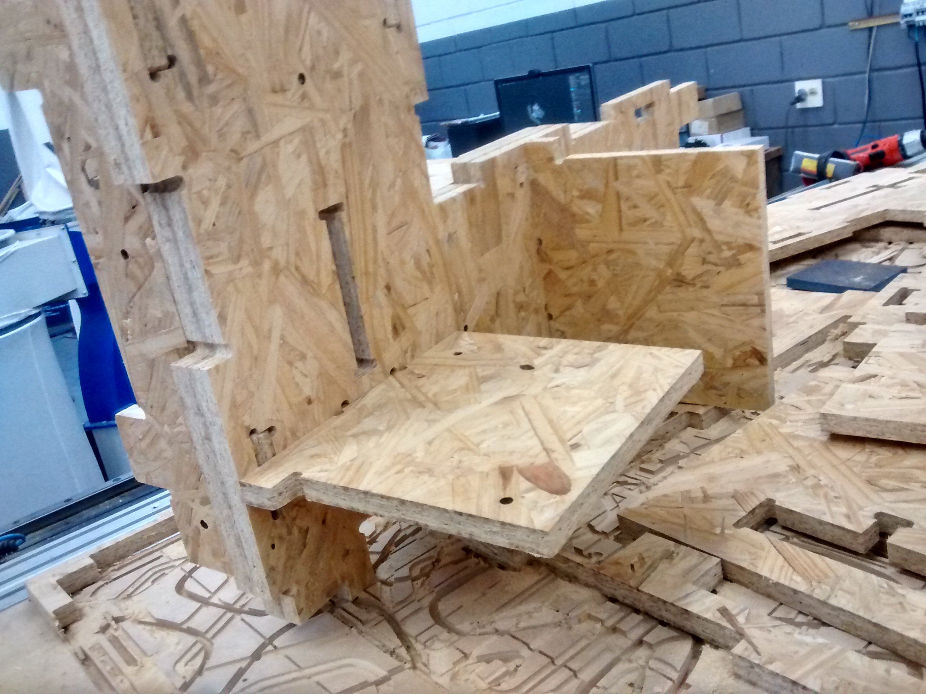
fotos/teste de encaixe/IMG_20170519_145433.jpg
