uncreatednet/wikilab-ufabc/fotos/teste de encaixe/IMG_20170519_145909.jpg

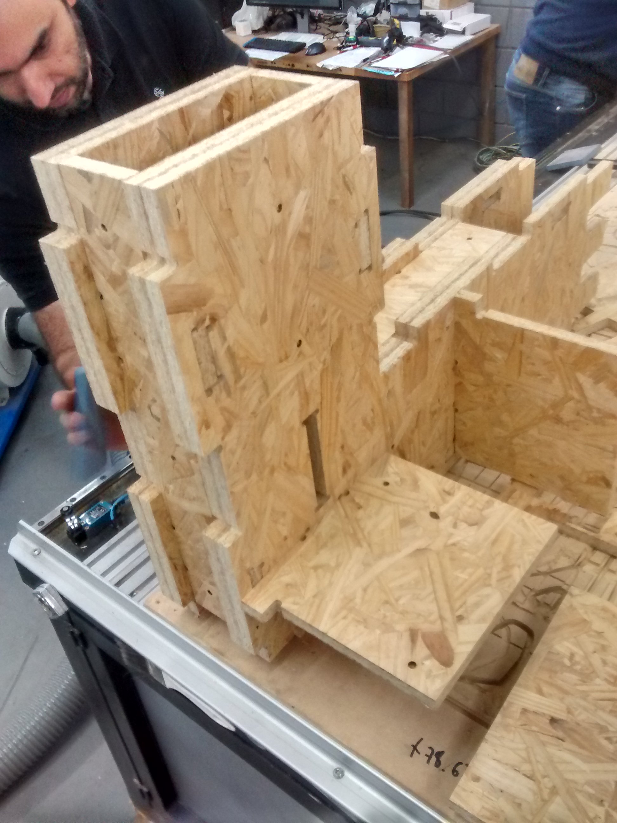
fotos/teste de encaixe/IMG_20170519_145909.jpg
