uncreatednet/wikilab-ufabc/fotos/teste de encaixe/IMG_20170519_150851.jpg

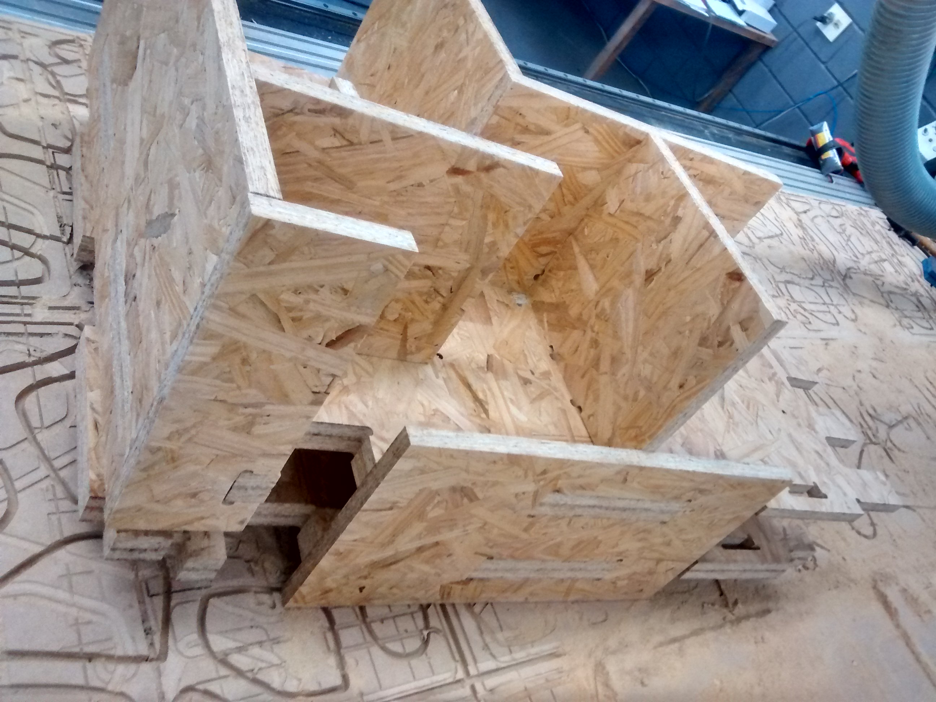
fotos/teste de encaixe/IMG_20170519_150851.jpg
