uncreatednet/wikilab-ufabc/fotos/teste de encaixe/IMG_20170519_150911.jpg

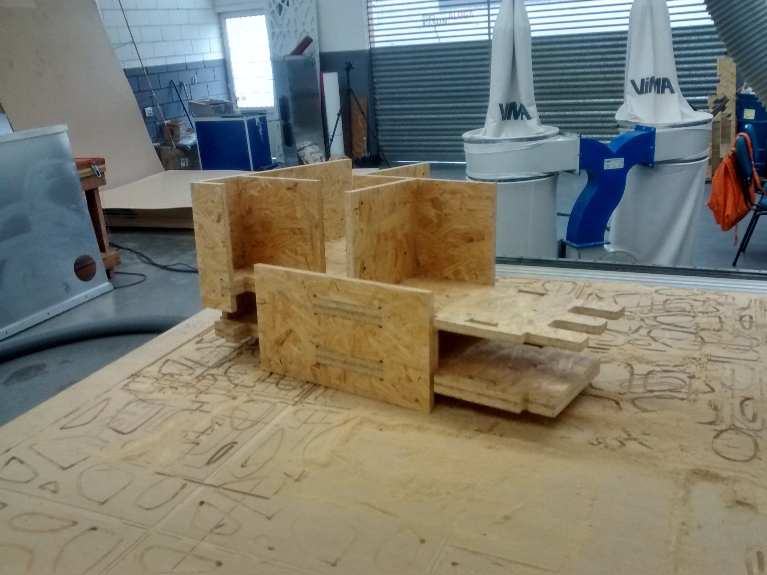
fotos/teste de encaixe/IMG_20170519_150911.jpg
