uncreatednet/wikilab-ufabc/fotos/teste de encaixe/IMG_20170519_150921.jpg

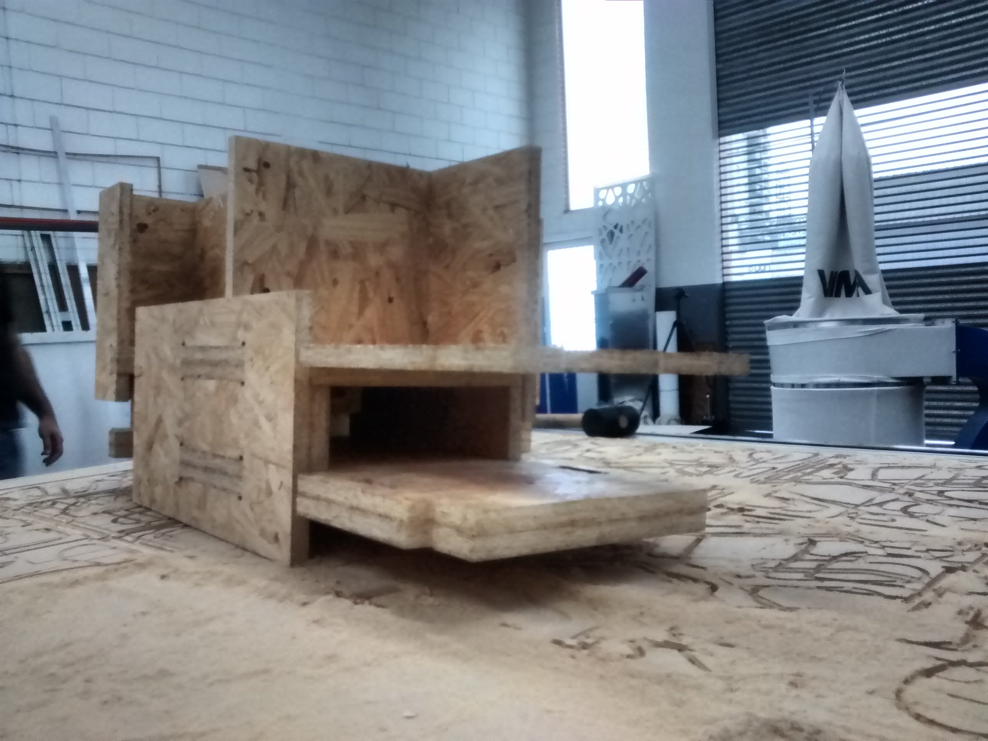
fotos/teste de encaixe/IMG_20170519_150921.jpg
