uncreatednet/wikilab-ufabc/fotos/teste de encaixe/IMG_20170519_152041.jpg

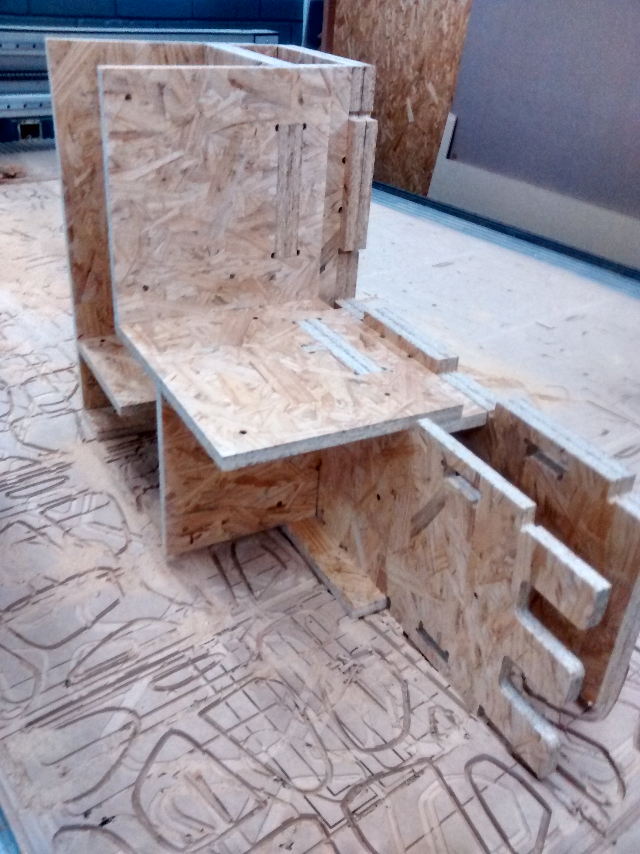
fotos/teste de encaixe/IMG_20170519_152041.jpg
