uncreatednet/wikilab-ufabc/teste de encaixe/test part 01.jpg

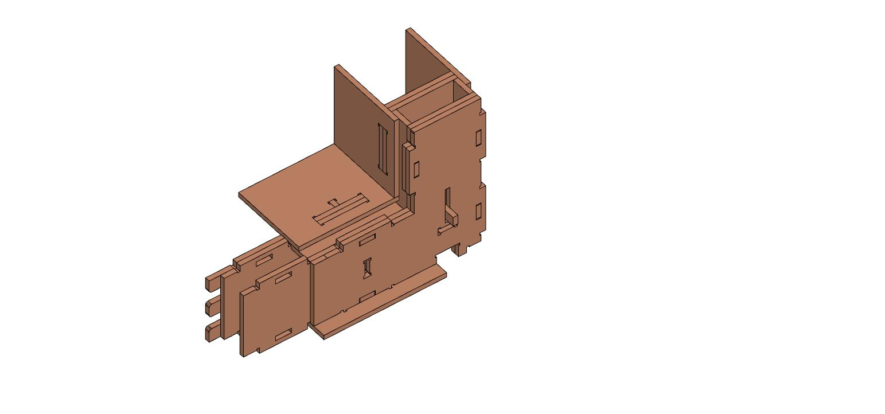
teste de encaixe/test part 01.jpg
