uncreatednet/wikilab-ufabc/teste de encaixe/test part 02.jpg

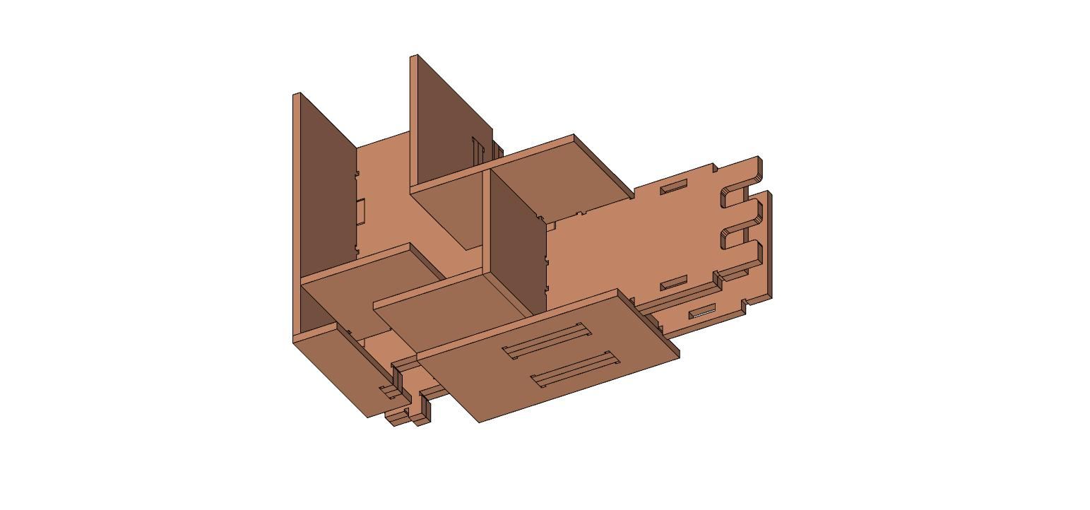
teste de encaixe/test part 02.jpg
