uncreatednet/wikilab-ufabc/elétrico/final/1718-EL-DE-01-R00.pdf

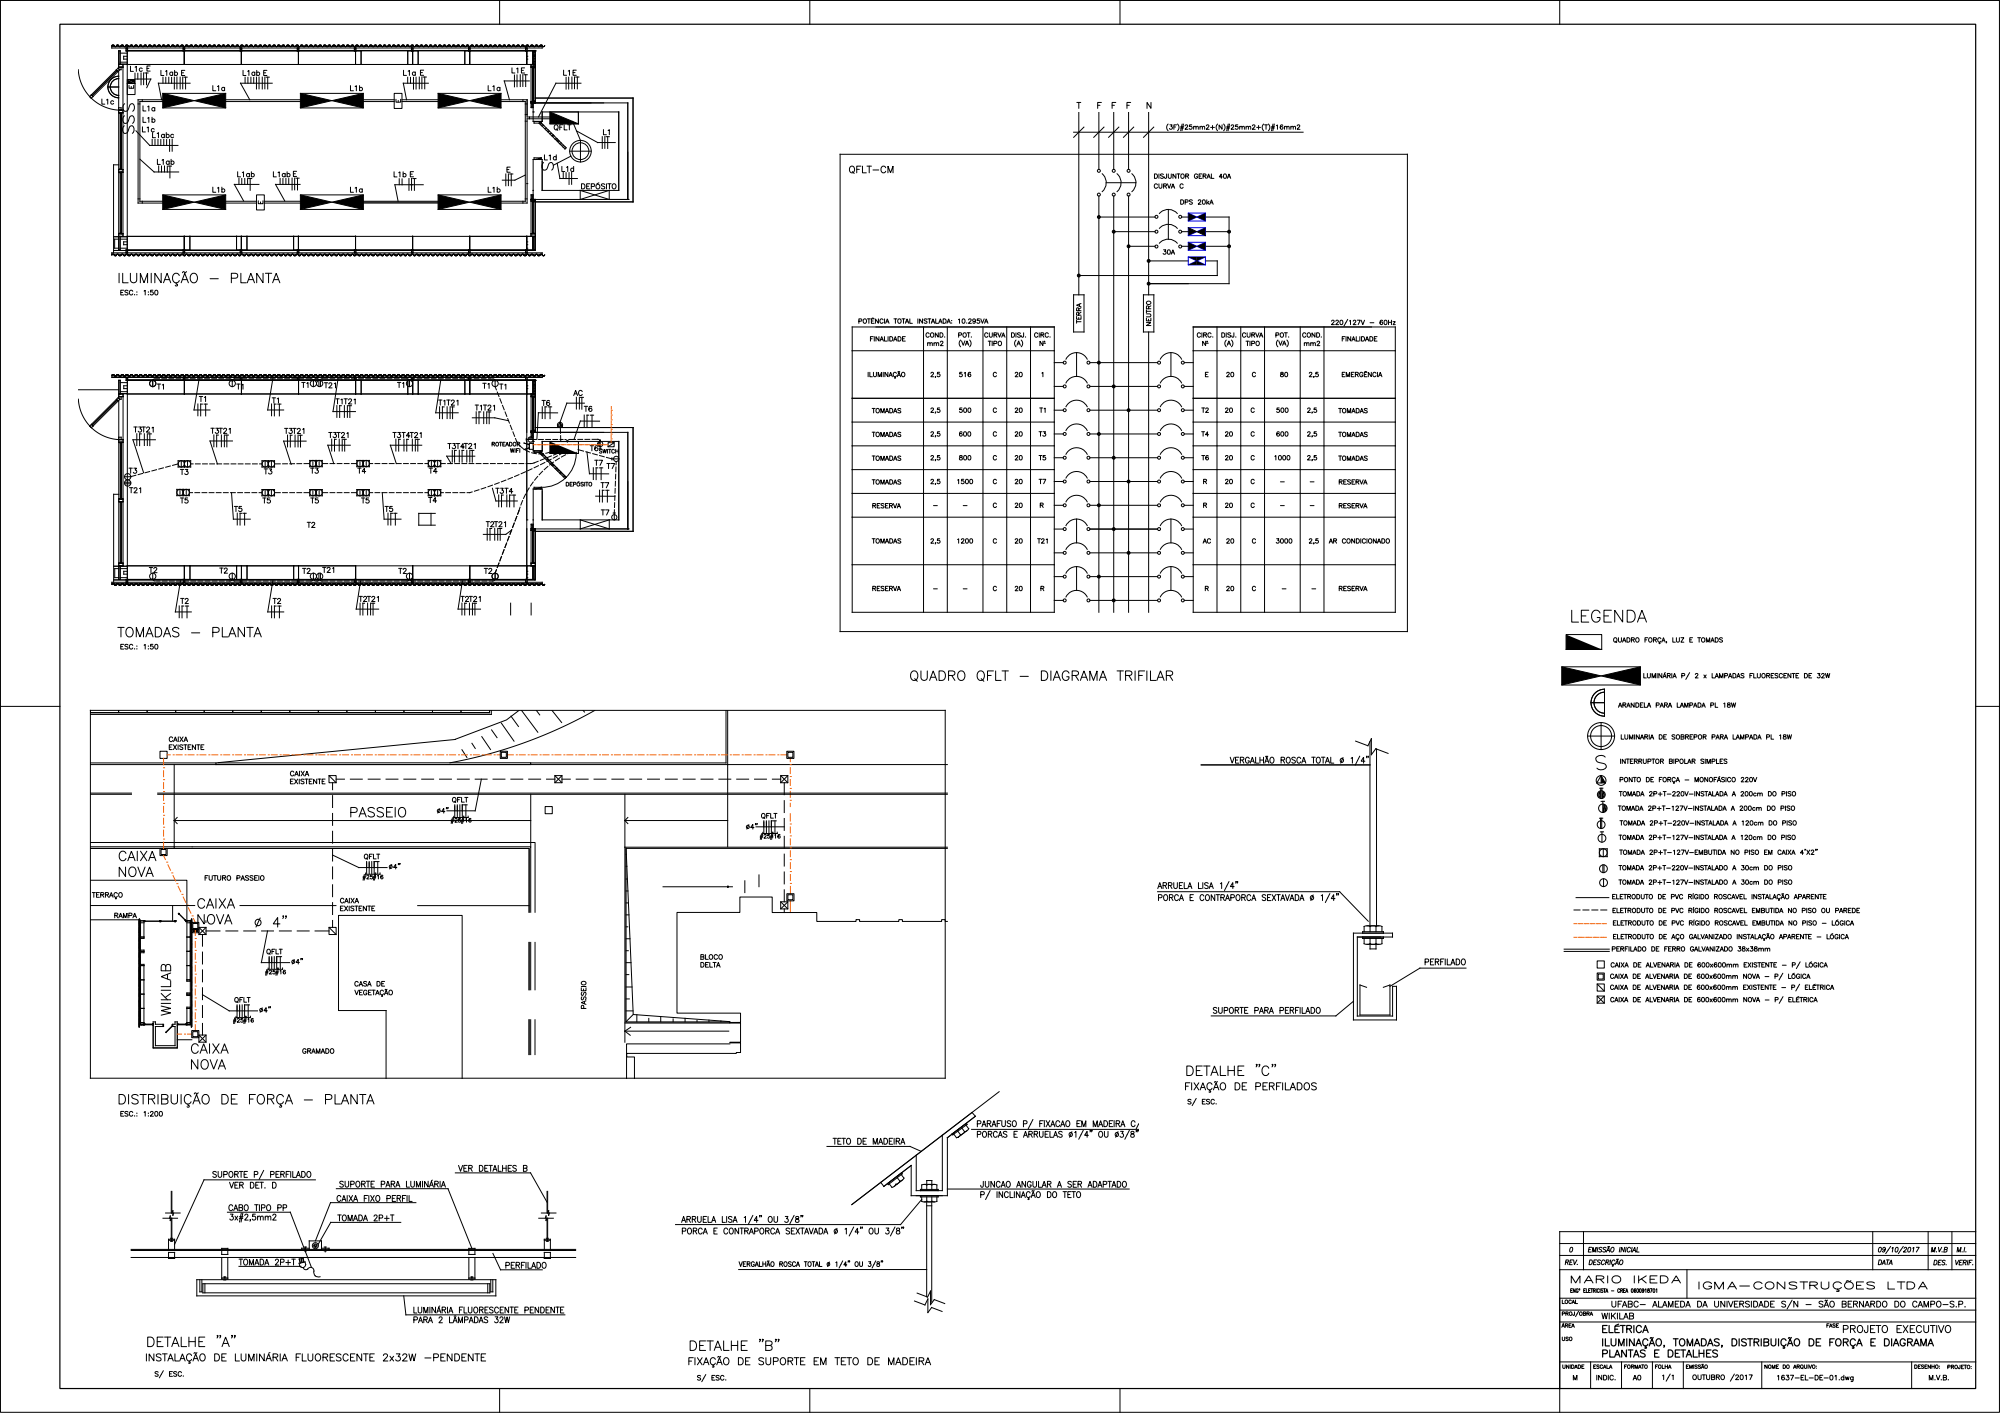
[picture p354: page 1]
