uncreatednet/wikilab-ufabc/elétrico/anteprojeto/Elétrica - Projeto Básico - proposta.pdf

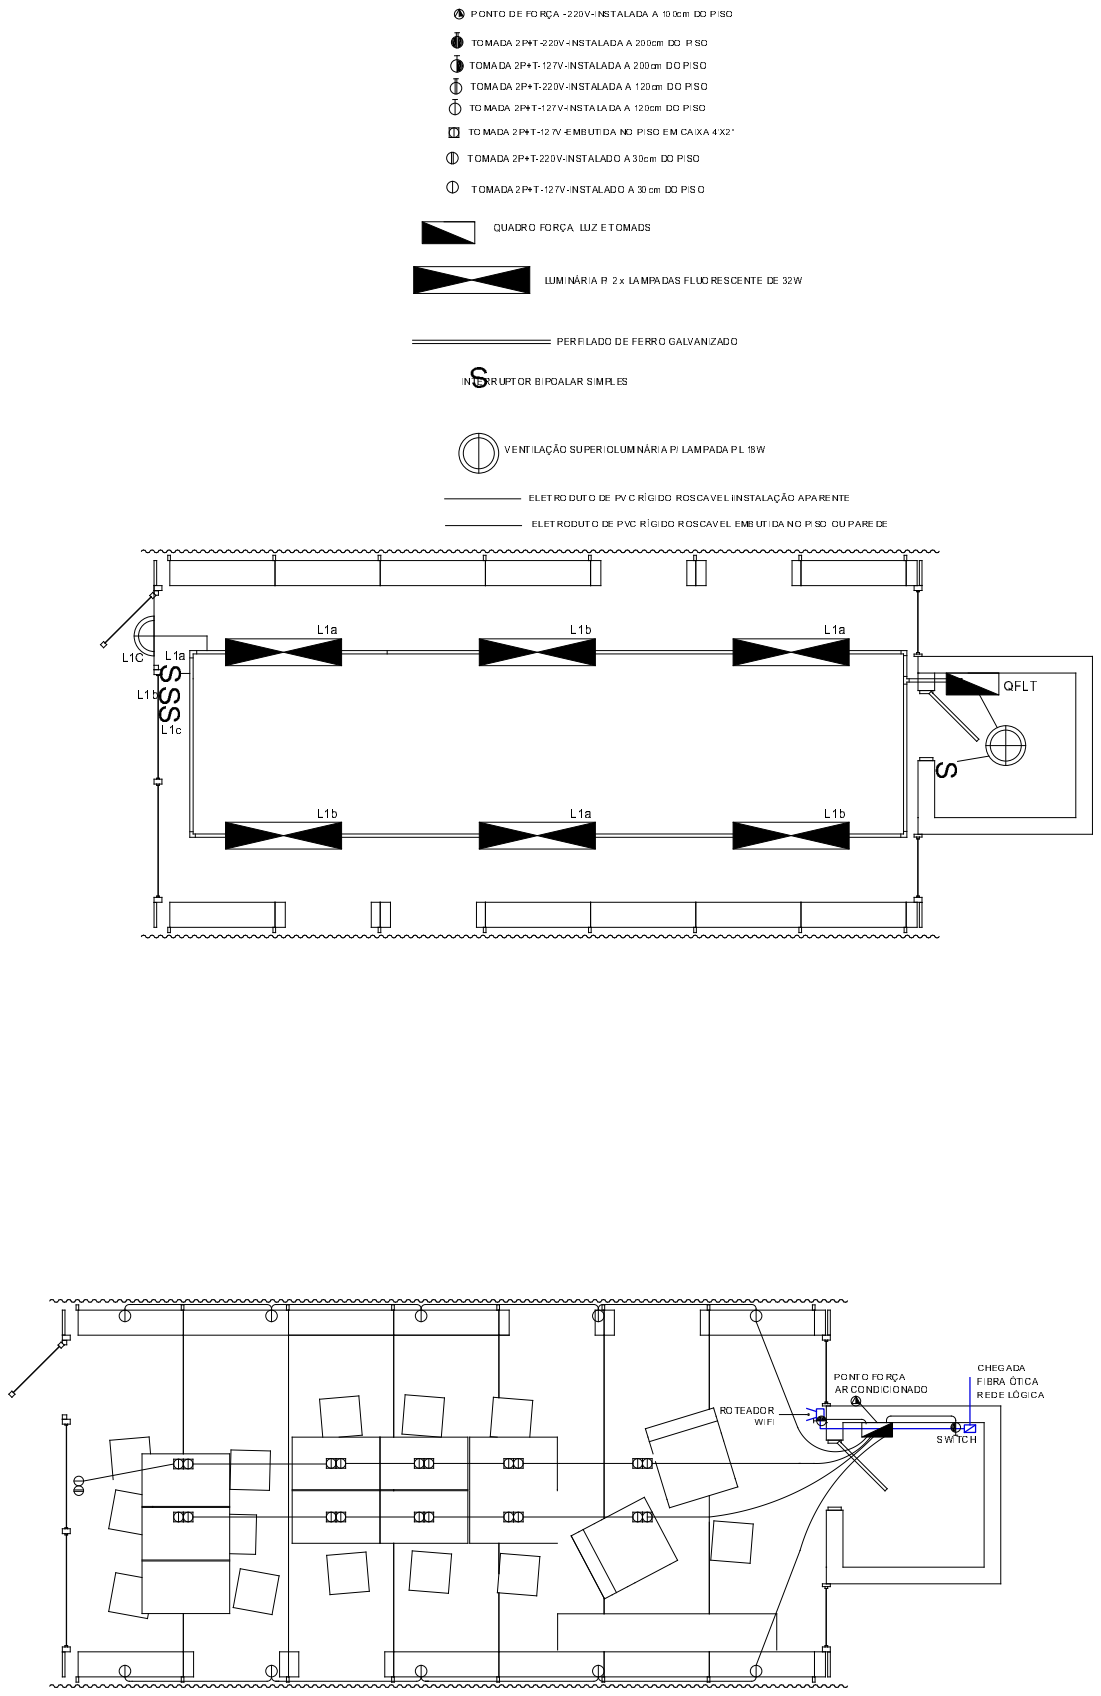
[picture p355: page 1]
❼❽❾❿➀➁ ➂➃➄➅➆➇➈➉➊➋➌➍➎➏➐➑➒➓➔ → ➣↔↕➙➛ ➜➝ ➞➟➠➡; ➢➤➥➦➧➨ ➩➫➭➯➲➳➵➸➺➻➼➽➾➚➪➶➹➘➴ ➷ ➬➮➱✃❐ ❒❮ ❰ÏÐÑ; ÷øùúûü ýþÿ✁✂✄☎✆✝✞✟✠✡☛☞✌✍✎ ✏ ✑✒✓✔✕ ✖✗ ✘✙✚✛

ÒÓÔÕÖ× ØÙÚÛÜÝÞßàáâãäåæçèéê ë ìíîïð ñò óôõö

❞❡❢❣❤✐ ❥❦❧♠♥♦♣qrst✉✈✇①②③④⑤ ⑥ ⑦⑧⑨⑩ ❶❷ ❸❹❺❻

❝❞❡❢❣❤✐❥❦ ❧♠ ♥ ♦ ♣qrst✉✈✇ ①②③④⑤⑥⑦⑧⑨⑩❶❷ ❸❹ ❺❻❼

❽❾❿➀➁➂➃➄➅ ➆➇ ➈➉➊➋➌ ➍➎➏➐➑➒➓➔→➣↔

➽➾➚➪➶➹➘➴➷➬ ➮➱✃❐❒❮❰ÏÐÑ ÒÓÔÕ Ö× ØÙ ÚÛÜÝÞßà áâ ãäå

æçèéêëìíîï ðñ òóô õ ö÷ øùú ûüýþÿ✁✂ ✄☎✆✝✞✟✠✡☛☞✌ ✍✎✏✑✒✓✔✕

❜❝❞❡❢❣❤✐❥❦ ❧♠ ♥♦♣ qrst✉✈ ✇①②③④⑤⑥⑦ ⑧⑨⑩❶❷❸❹❺ ❻❼ ❽❾❿➀ ➁➂ ➃➄➅➆➇➈
