uncreatednet/wikilab-ufabc/aprovação UFABC/discussão infraestrutura/Infraestrutura para Wikilab.pdf

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

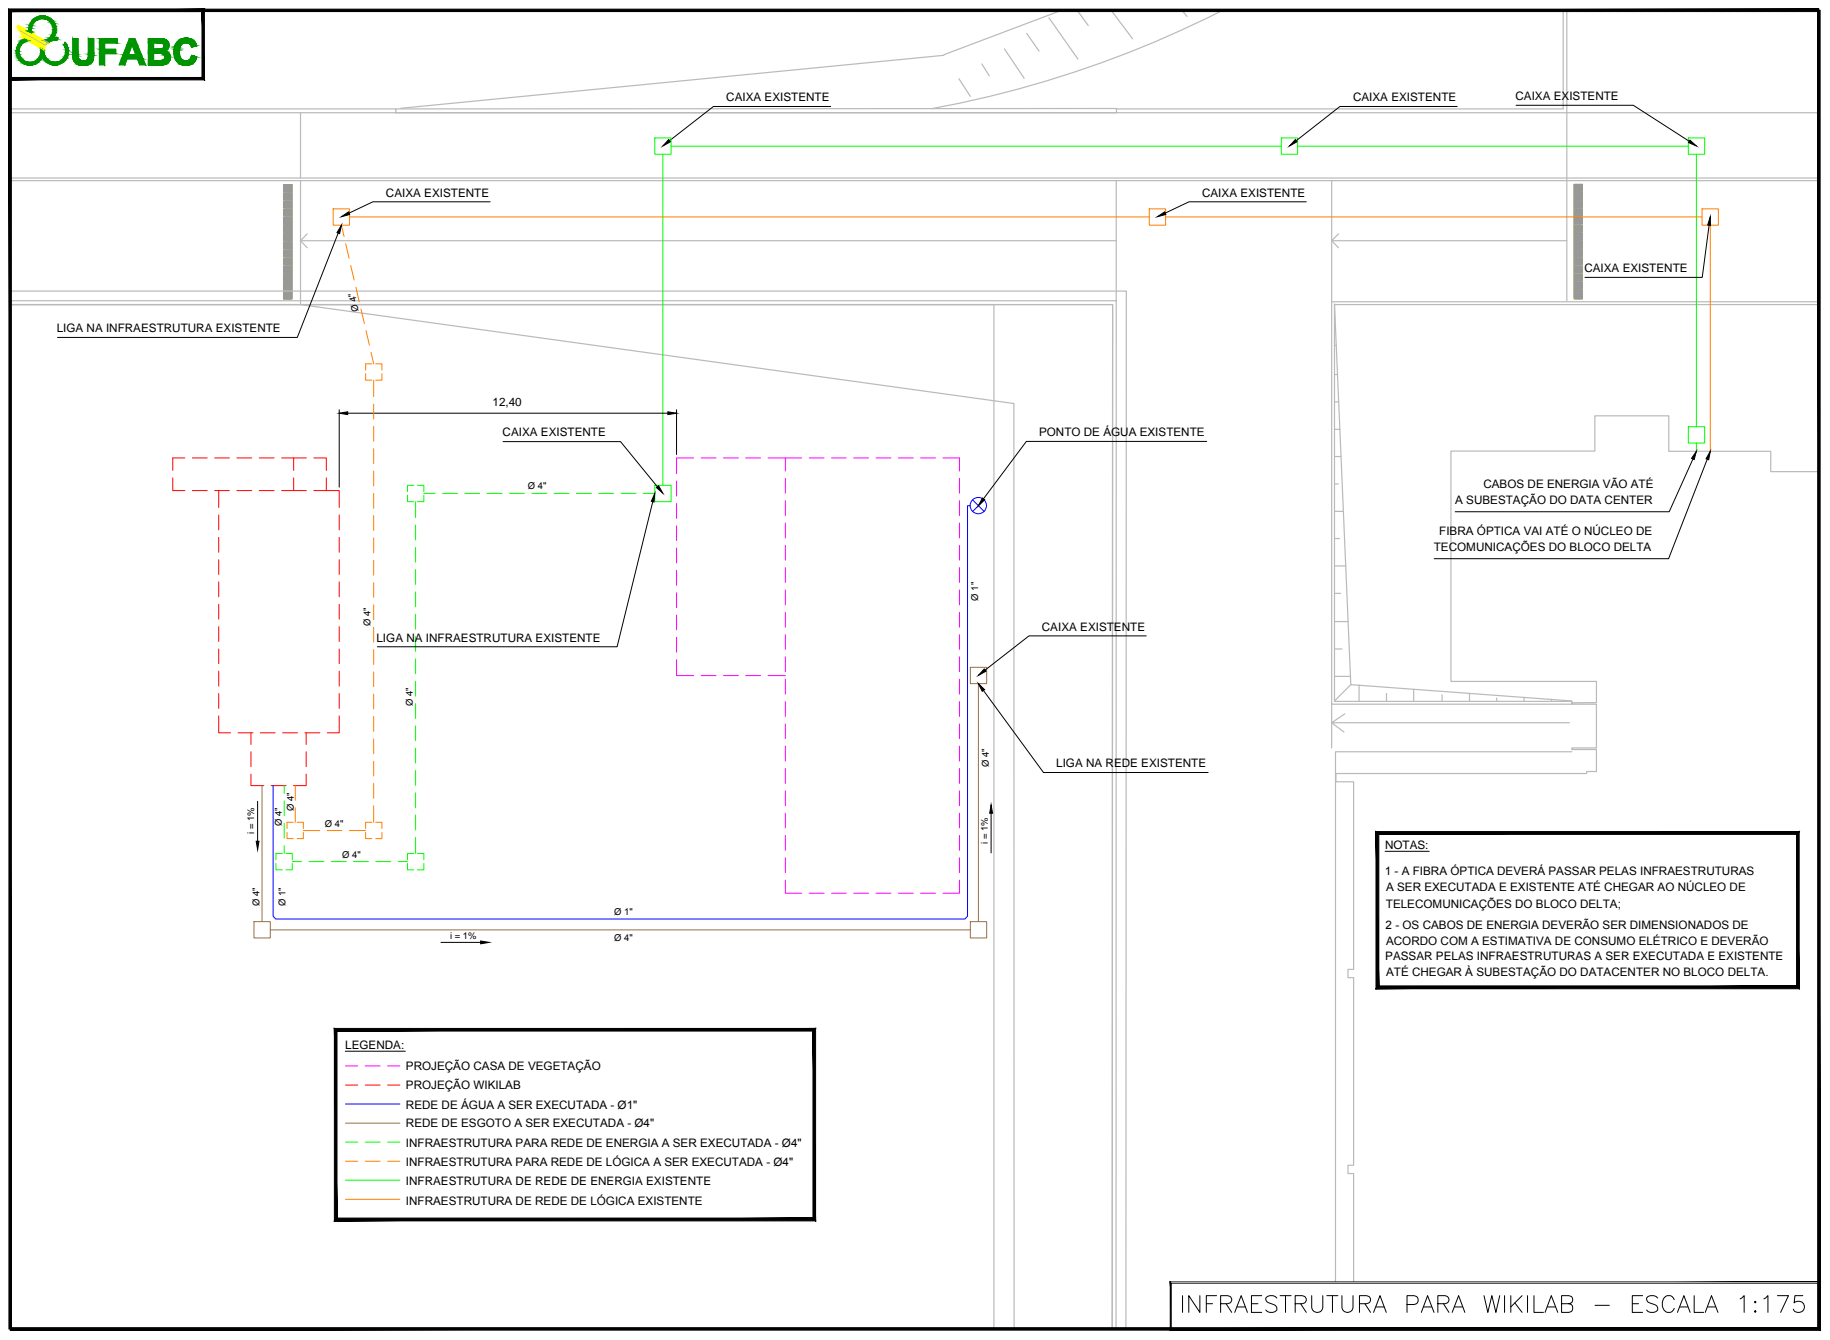
[picture p356: page 1]
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
