uncreatednet/wikilab-ufabc/estudos/versão antiga para licitação/Projeto executivo.pdf

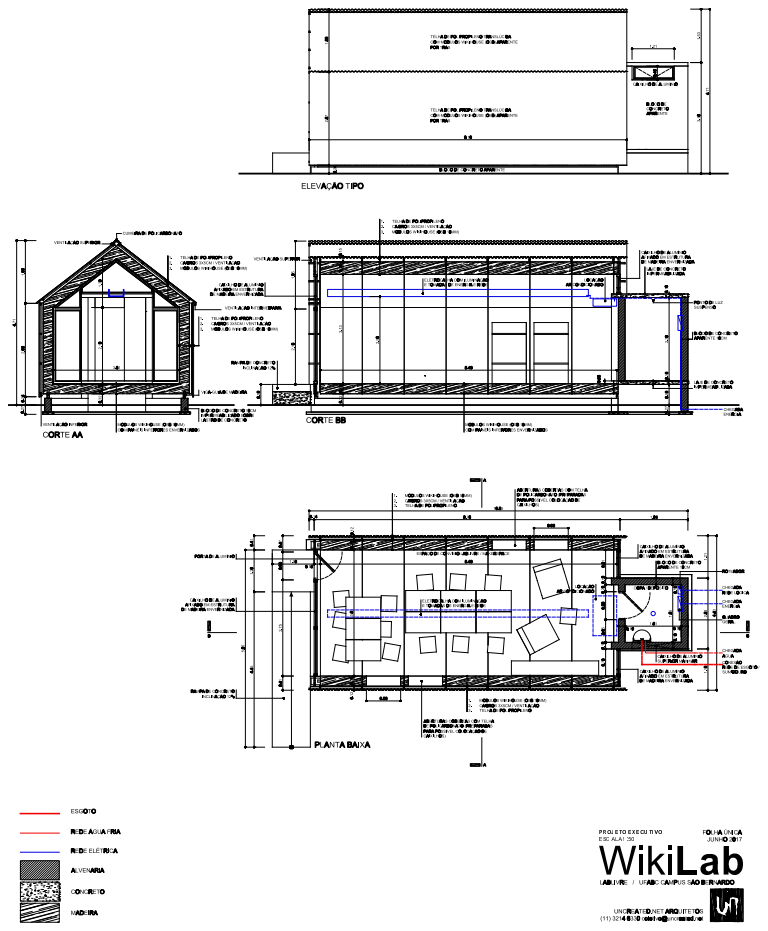
[picture p357: page 1]
