uncreatednet/wikilab-ufabc/apresentação/apresentação inicial/folhas pdf/folha A1.pdf

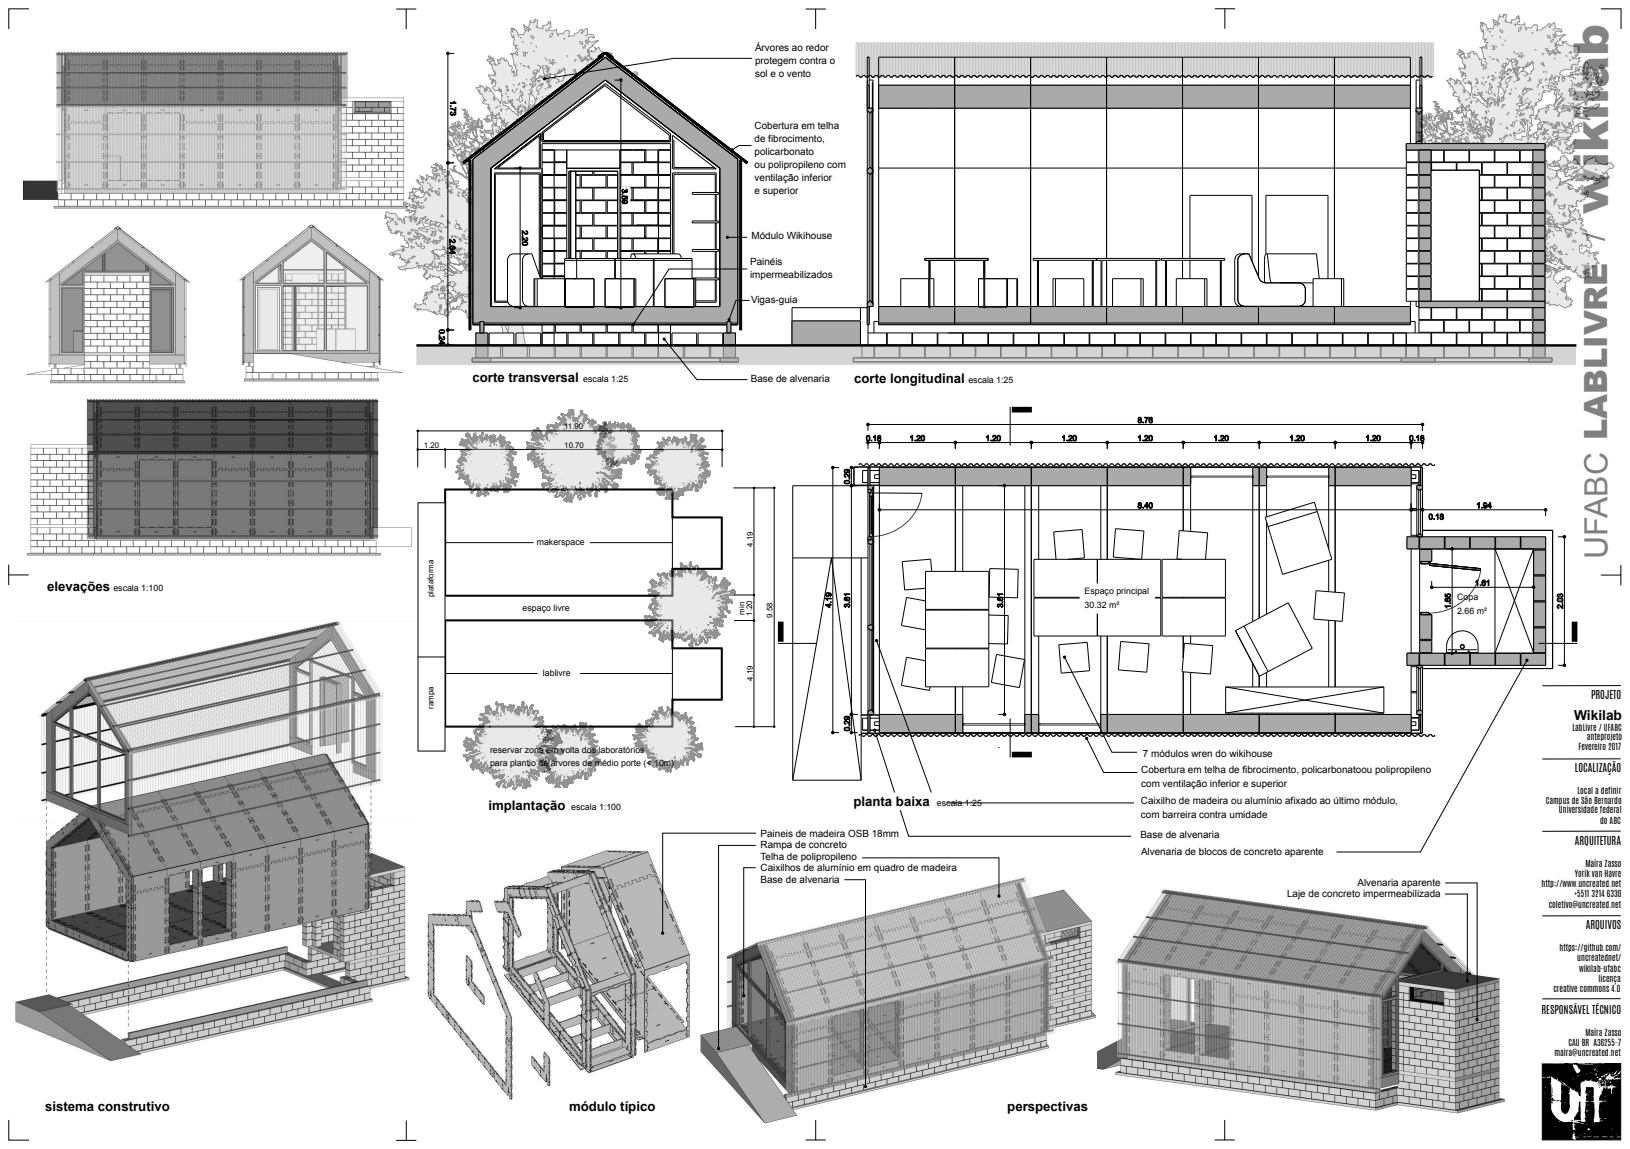
[picture p358: page 1]
elevações escala 1:100; sistema construtivo; ARQUITETURA; RESPONSÁVEL TÉCNICO; LOCALIZAÇÃO; do ABC; corte transversal escala 1:25; corte longitudinal escala 1:25; Espaço principal; Copa; Vigas-guia; Módulo Wikihouse; Painéis impermeabilizados; implantação escala 1:100; escala 1:100; lablivre; makerspace; rampa plataforma; espaço livre; min; Wikilab LabLivre / UFABC; PROJETO; anteprojeto Fevereiro 2017; creative commons 4.0; módulo típico; perspectivas; Alvenaria aparente

wikilab UFABC LABLIVRE /

Árvores ao redor
protegem contra o
sol e o vento

Cobertura em telha
de fibrocimento,
policarbonato
ou polipropileno com
ventilação inferior
e superior

Base de alvenaria

reservar zona em volta dos laboratórios
para plantio de árvores de médio porte (< 10m)

7 módulos wren do wikihouse
Cobertura em telha de fibrocimento, policarbonatoou polipropileno
com ventilação inferior e superior
Caixilho de madeira ou alumínio afixado ao último módulo,
com barreira contra umidade
Alvenaria de blocos de concreto aparente

Local a definir
Campus de São Bernardo
Universidade federal

planta baixa escala 1:25

Paineis de madeira OSB 18mm
Rampa de concreto
Telha de polipropileno
Caixilhos de alumínio em quadro de madeira

Maíra Zasso
Yorik van Havre
http://www.uncreated.net
coletivo@uncreated.net
ARQUIVOS

Laje de concreto impermeabilizada

https://github.com/
uncreatednet/
wikilab-ufabc
licença

CAU BR A36255-7
maira@uncreated.net
