uncreatednet/wikilab-ufabc/apresentação/apresentação inicial/folhas pdf/corte long.pdf

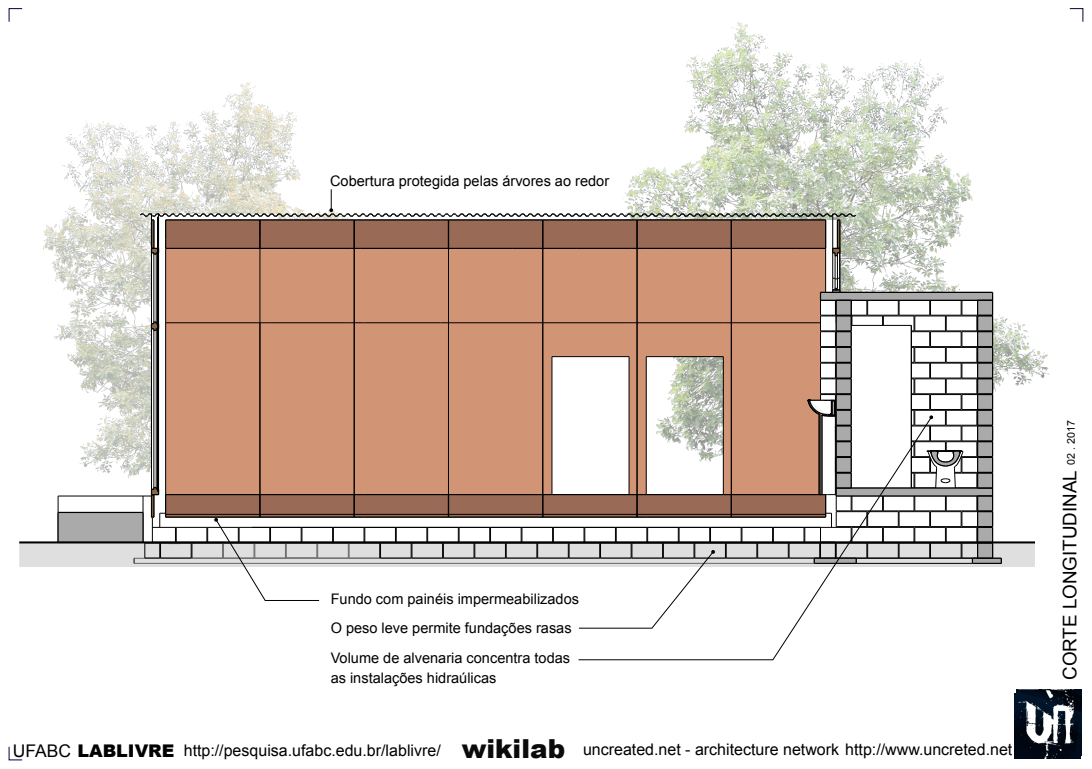
[picture p359: page 1]
CORTE LONGITUDINAL 02 . 2017

Cobertura protegida pelas árvores ao redor

Fundo com painéis impermeabilizados
O peso leve permite fundações rasas
Volume de alvenaria concentra todas
as instalações hidraúlicas

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
