uncreatednet/wikilab-ufabc/apresentação/apresentação inicial/folhas pdf/corte trans.pdf

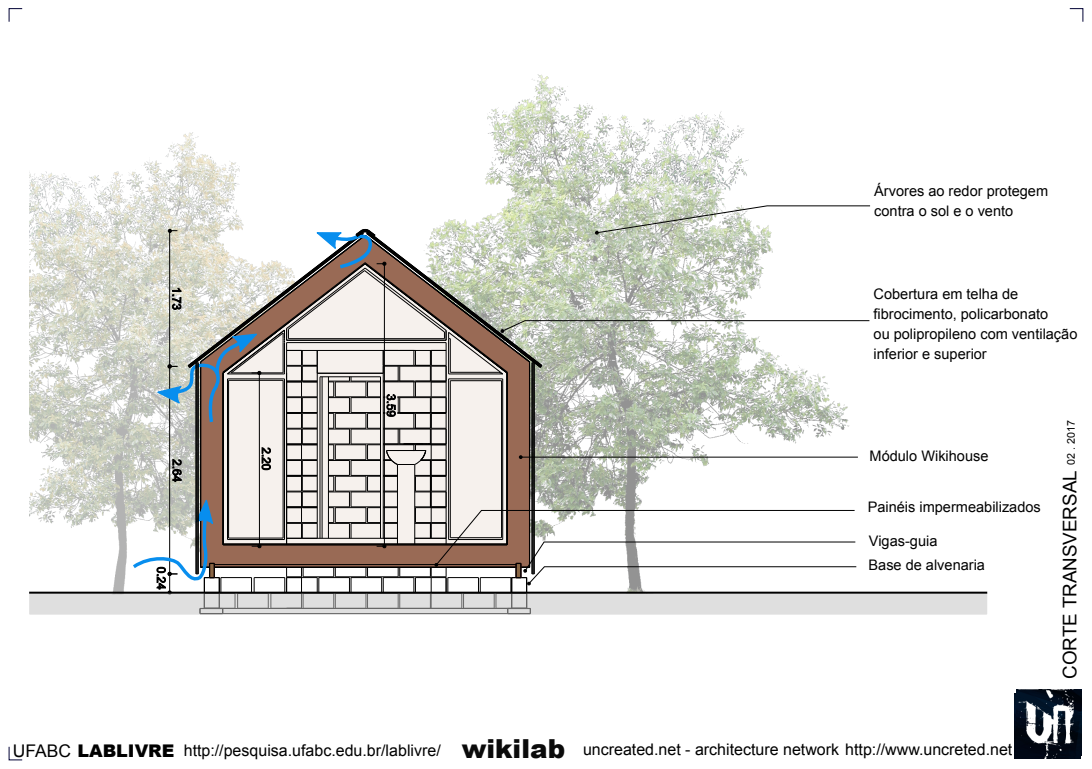
[picture p360: page 1]
CORTE TRANSVERSAL 02 . 2017; Módulo Wikihouse; Painéis impermeabilizados

Árvores ao redor protegem
contra o sol e o vento

Cobertura em telha de
fibrocimento, policarbonato
ou polipropileno com ventilação
inferior e superior

Vigas-guia
Base de alvenaria

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
